sonocotta/esp32-audio-dock/hardware/3-louder-esp32/rev-h7/2508-louder-esp32-h7-schematic.pdf

## U1³⁹ GND

## MCU

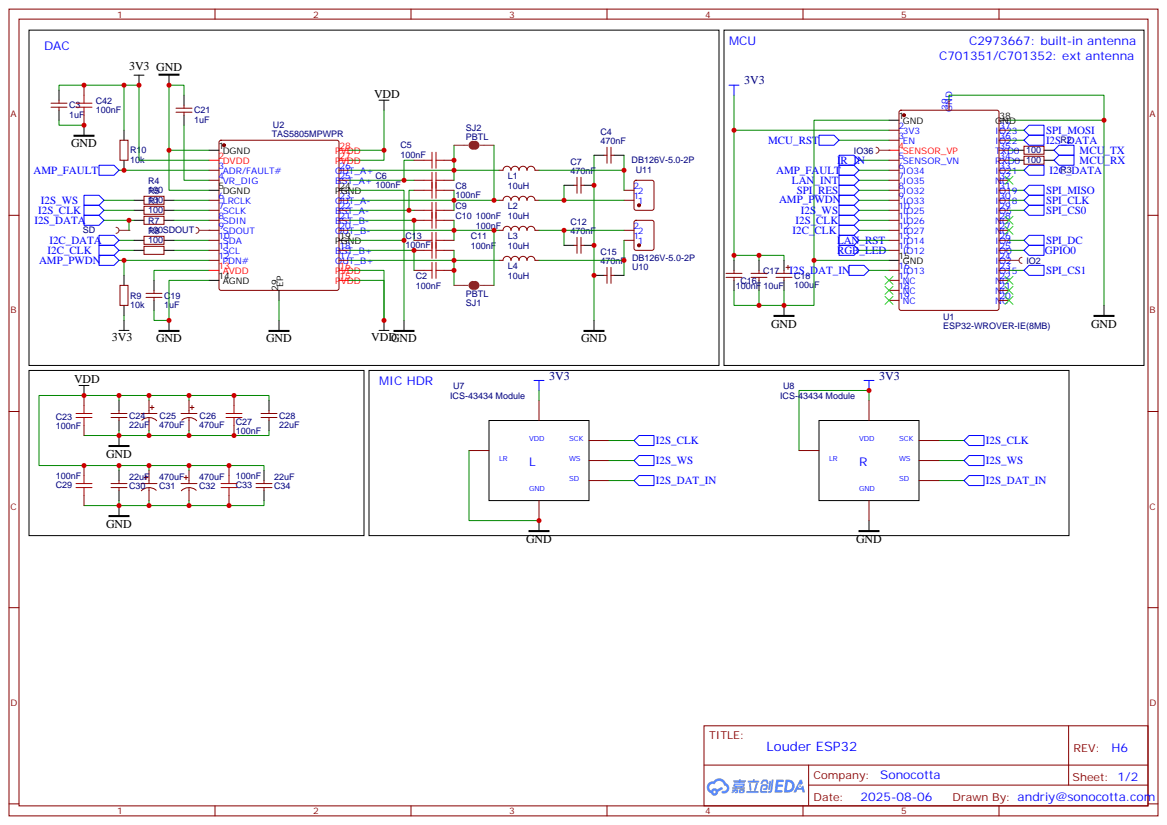
[picture p3: page 1]

Drawn By: andriy@sonocotta.com

## USB-TO-SERIAL BRIDGE USR-ES1 LAN module (W5500)

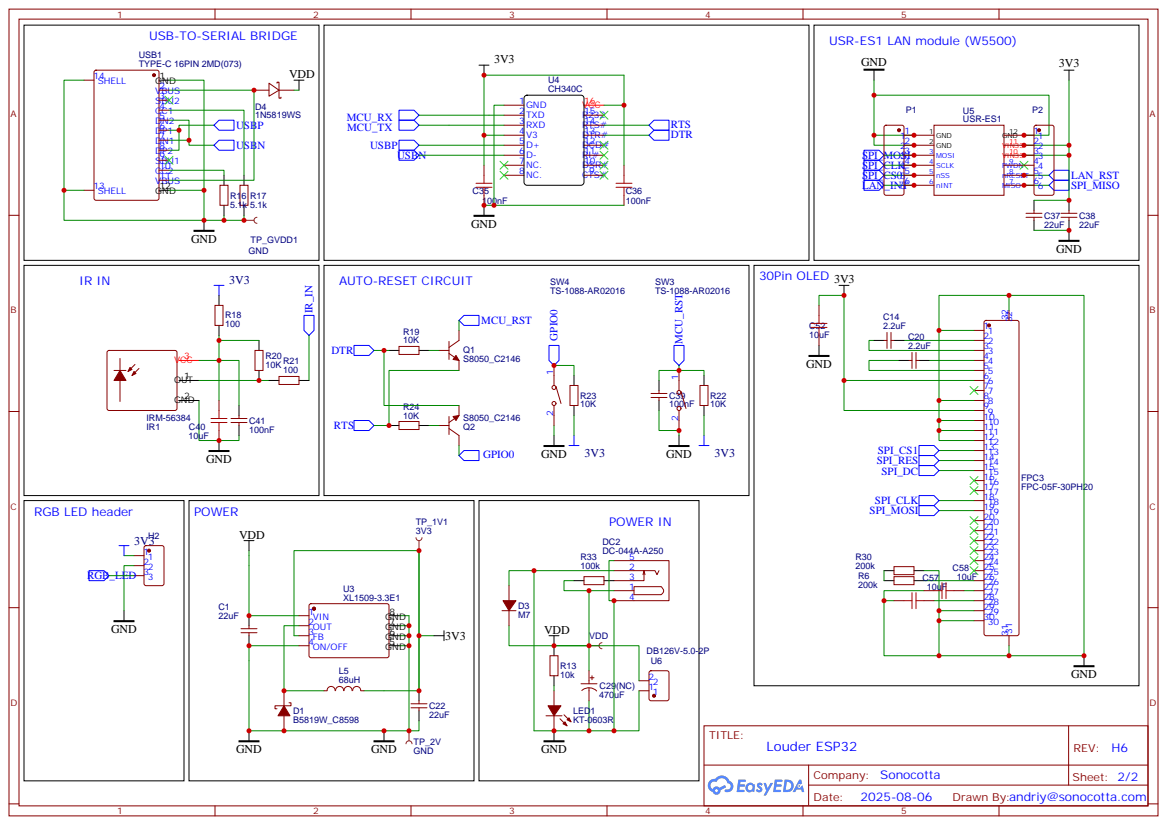
[picture p4: page 2]

Drawn By:andriy@sonocotta.com
