sonocotta/esp32-audio-dock/hardware/10-louder-esp32-pro/rev-c-pd-edition/2605-louder-esp32s3-plus-pd-c-schematic.pdf

# IO20 14IO19 13IO8 12IO18 11IO17 10IO16 9

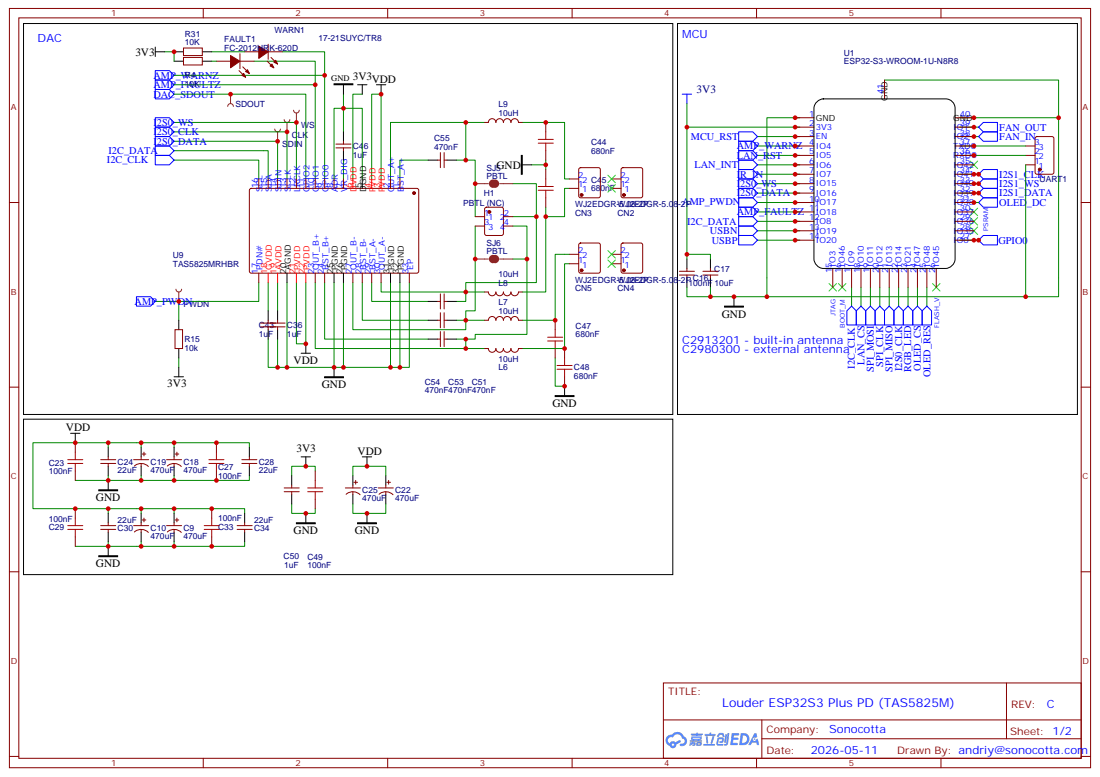
[picture p5: page 1]

9GPIO1 10 GPIO2 11 LRCLK 12 SCLK 13 SDIN 14 SDA 15 SCL 16 PDN# 17GVDD 18AVDD 19AGND 20PVDD 21PVDD 22OUT_B+ 23BST_B+ 24

Drawn By: andriy@sonocotta.com

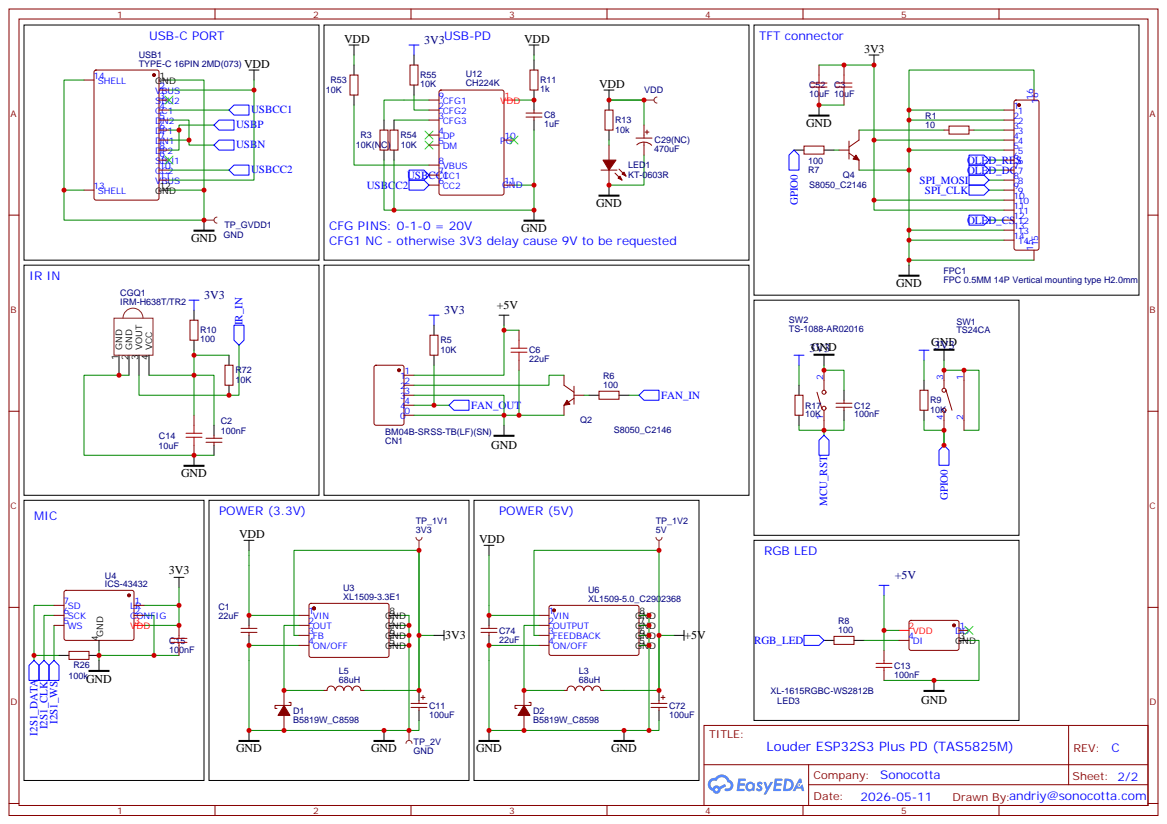
[picture p6: page 2]

CFG PINS: 0-1-0 = 20V
CFG1 NC - otherwise 3V3 delay cause 9V to be requested

FPC1
FPC 0.5MM 14P Vertical mounting type H2.0mm

Drawn By:andriy@sonocotta.com

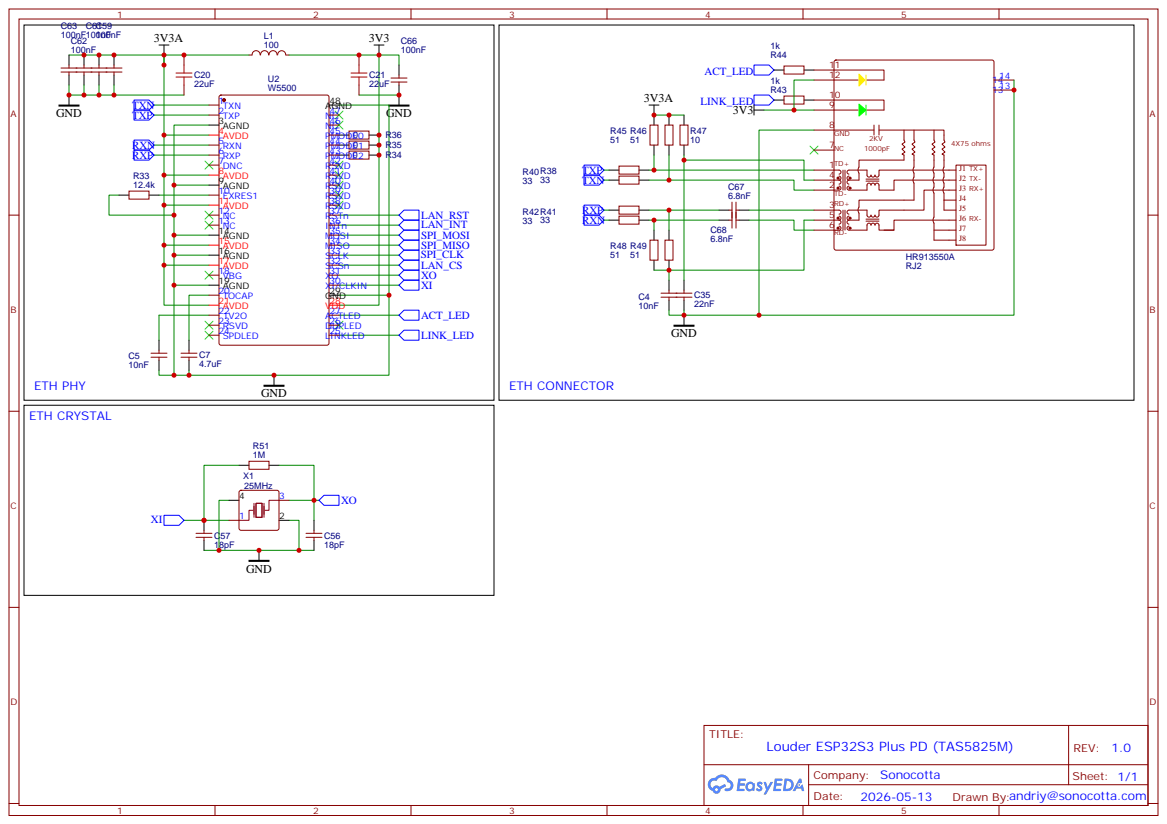
[picture p7: page 3]

Drawn By:andriy@sonocotta.com
