sonocotta/esp32-audio-dock/hardware/2-loud-esp32/rev-e3/2603-loud-esp32-e3-schematic.pdf

# OUTN 10 GND 11 N.C. 12 N.C. 13 LRCLK 14 GND 15 BCLK 16

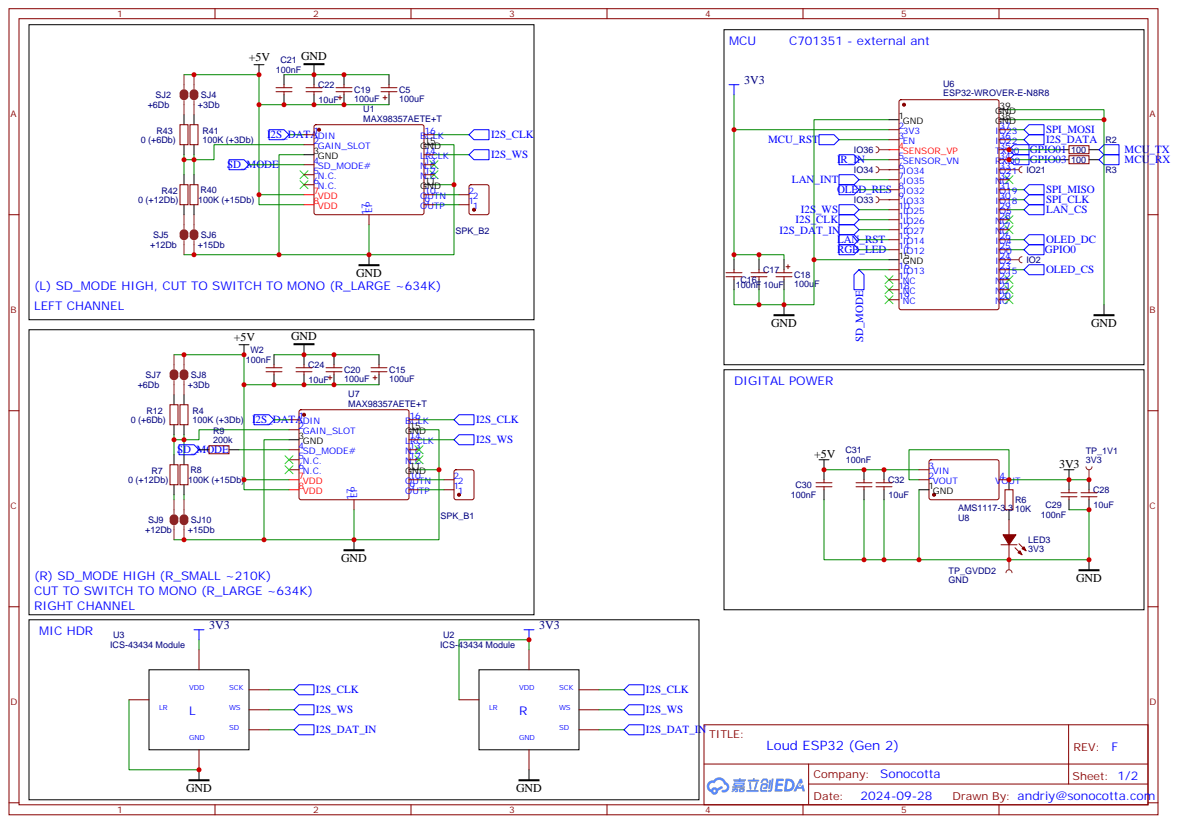
[picture p10: page 1]

(L) SD_MODE HIGH, CUT TO SWITCH TO MONO (R_LARGE ~634K)
LEFT CHANNEL

(R) SD_MODE HIGH (R_SMALL ~210K)
CUT TO SWITCH TO MONO (R_LARGE ~634K)
RIGHT CHANNEL
MIC HDR

Drawn By: andriy@sonocotta.com

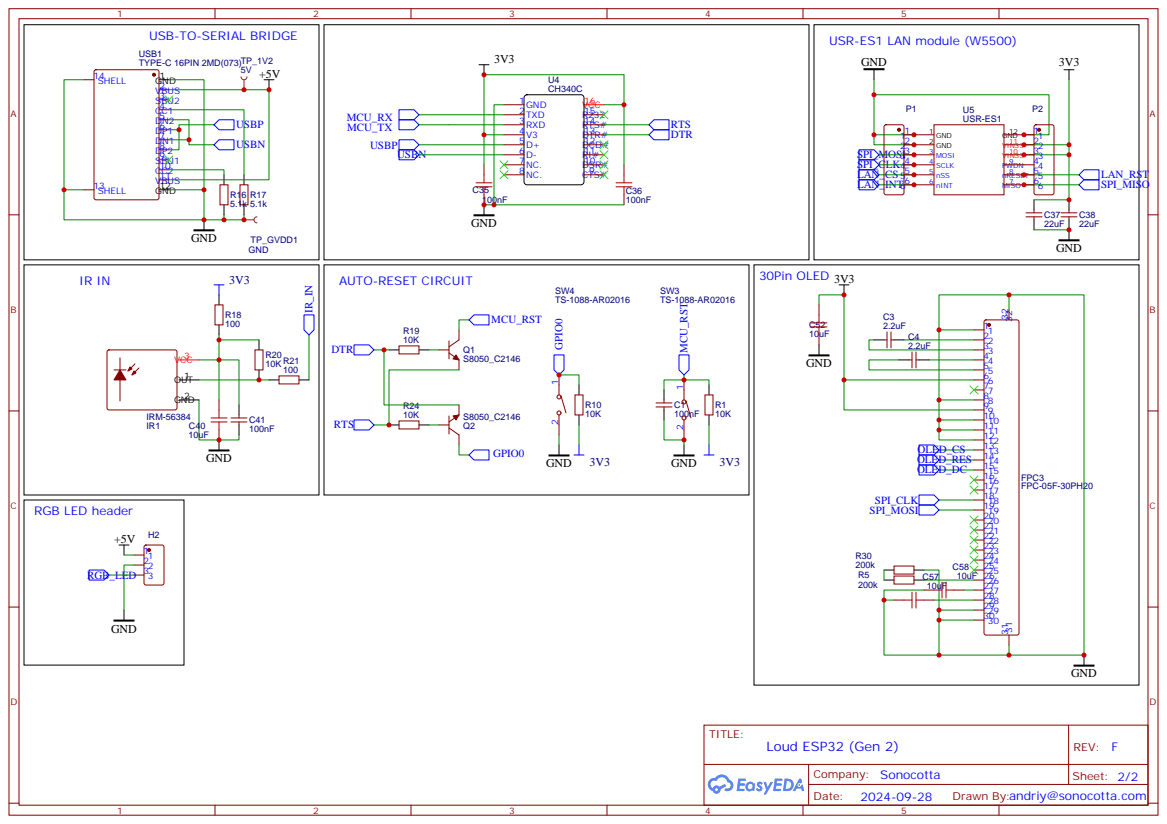
[picture p11: page 2]

Drawn By:andriy@sonocotta.com
