sonocotta/esp32-audio-dock/hardware/7-louder-esp32-plus/rev-b/2602-louder-esp32-plus-b-schematic.pdf

### U2³⁹ GND

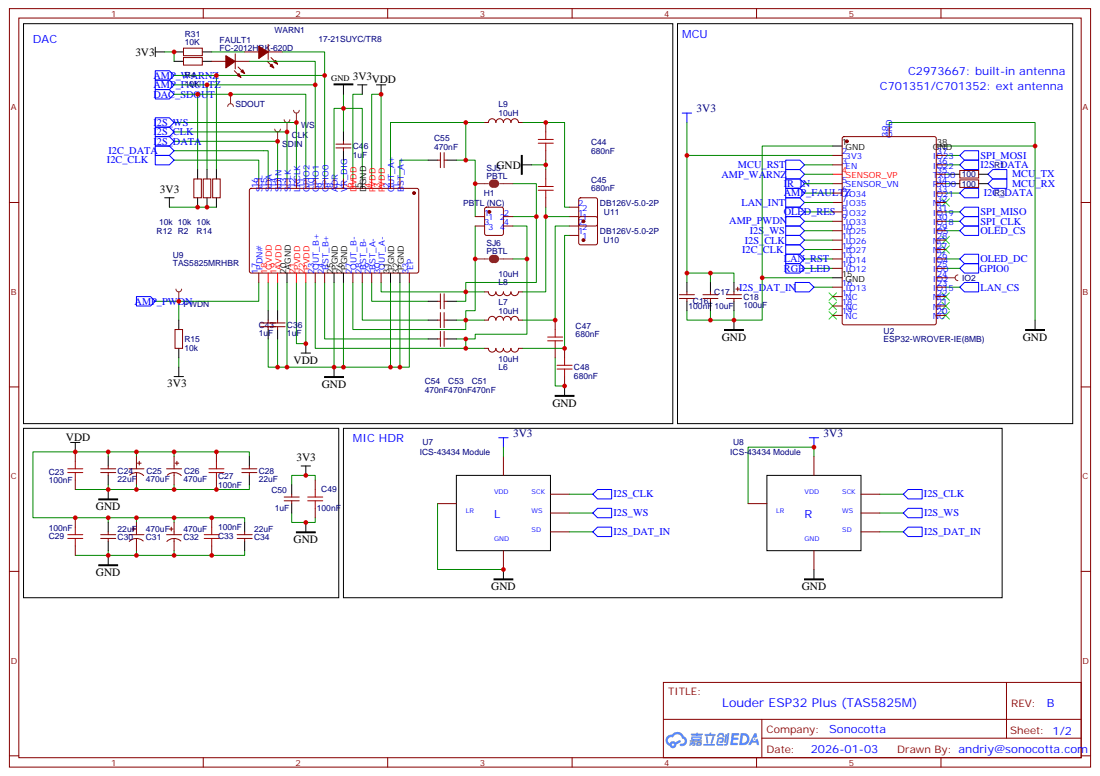
[picture p14: page 1]

9GPIO1 10 GPIO2 11 LRCLK 12 SCLK 13 SDIN 14 SDA 15 SCL 16 PDN# 17GVDD 18AVDD 19AGND 20PVDD 21PVDD 22OUT_B+ 23BST_B+ 24

Drawn By: andriy@sonocotta.com

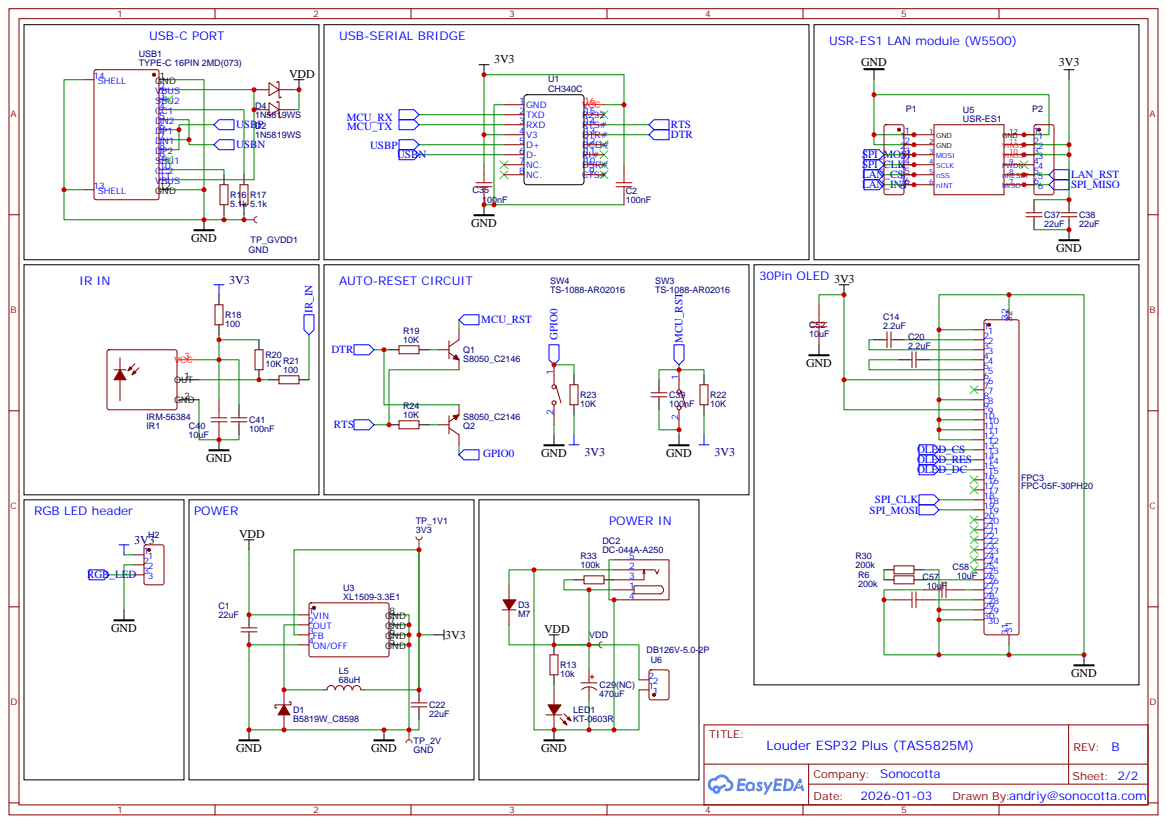
[picture p15: page 2]

Drawn By:andriy@sonocotta.com
