sonocotta/esp32-audio-dock/hardware/7-louder-esp32-plus/rev-a-s3/2601-louder-esp32s3-plus-a-schematic.pdf

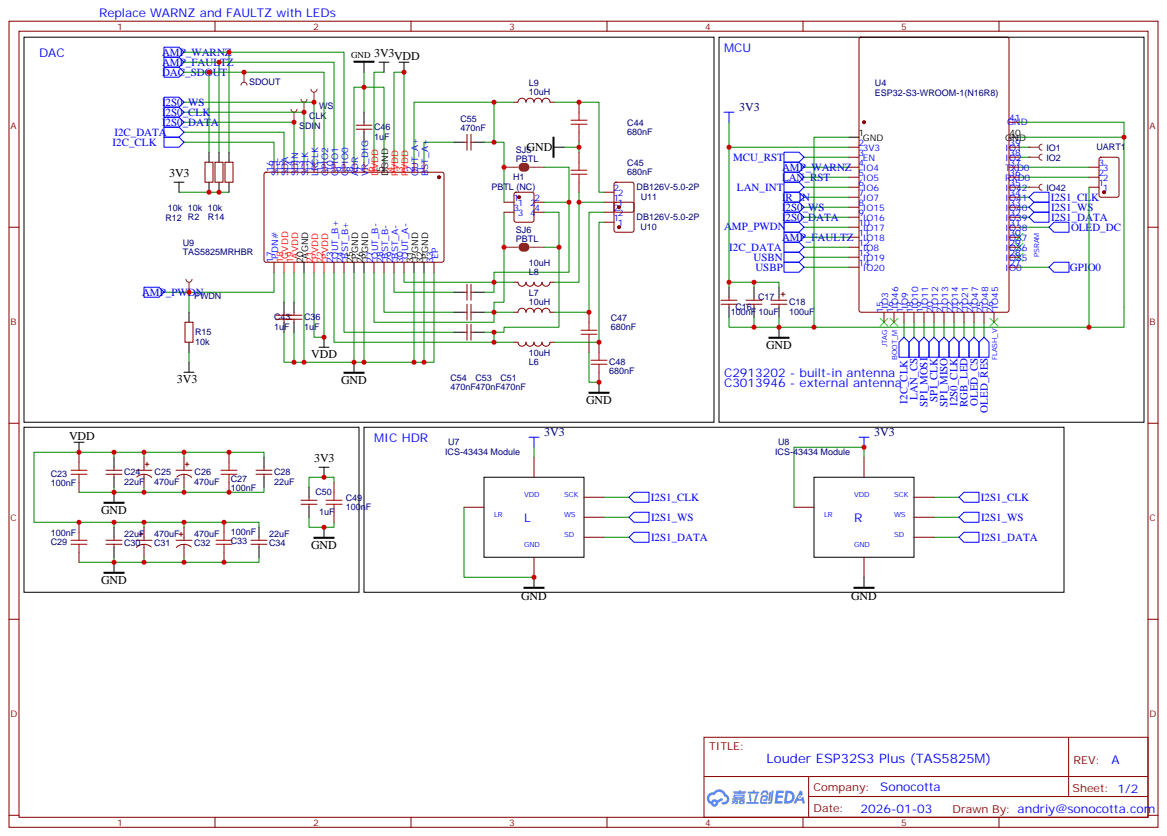
[picture p16: page 1]

Replace WARNZ and FAULTZ with LEDs

9GPIO1 10 GPIO2 11 LRCLK 12 SCLK 13 SDIN 14 SDA 15 SCL 16 PDN# 17GVDD 18AVDD 19AGND 20PVDD 21PVDD 22OUT_B+ 23BST_B+ 24

Drawn By: andriy@sonocotta.com

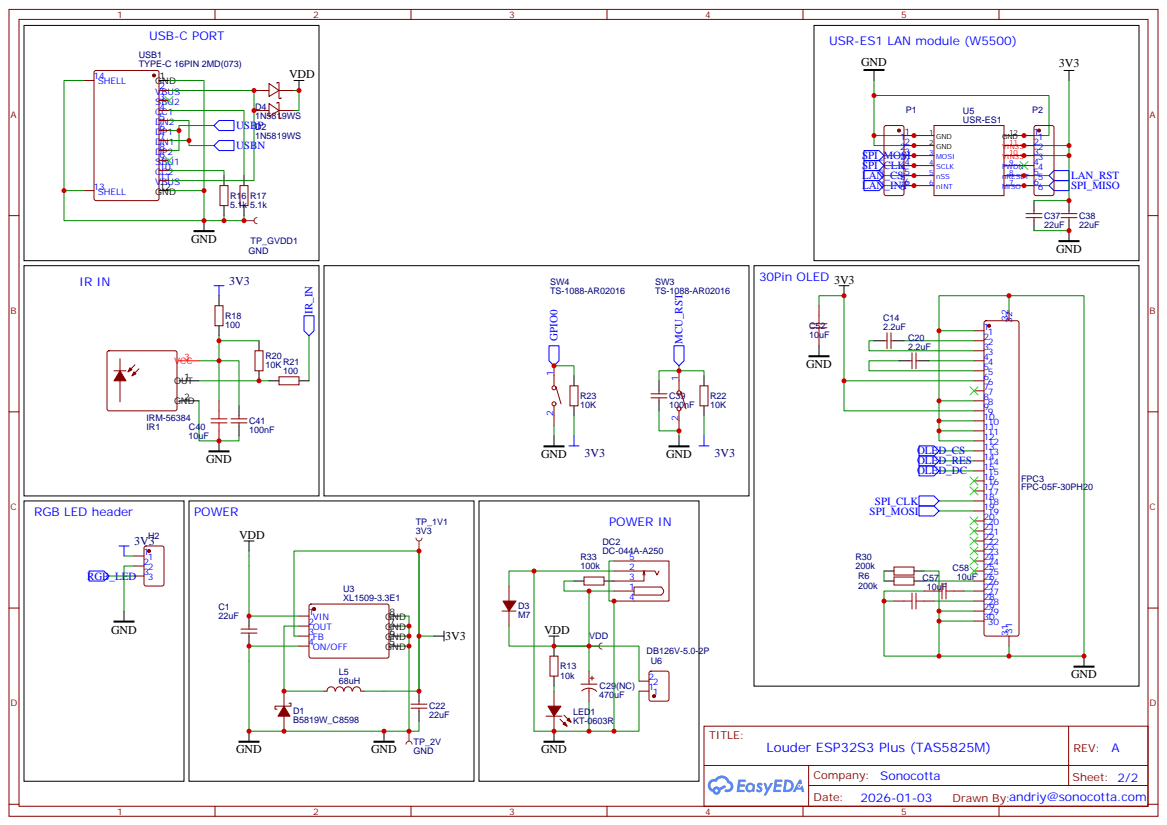
[picture p17: page 2]

Drawn By:andriy@sonocotta.com
