sonocotta/esp32-audio-dock/hardware/1-hifi-esp32/rev-f4/2511-hifi-esp32-f4-schematic.pdf

## MCU

## ANALOG POWER

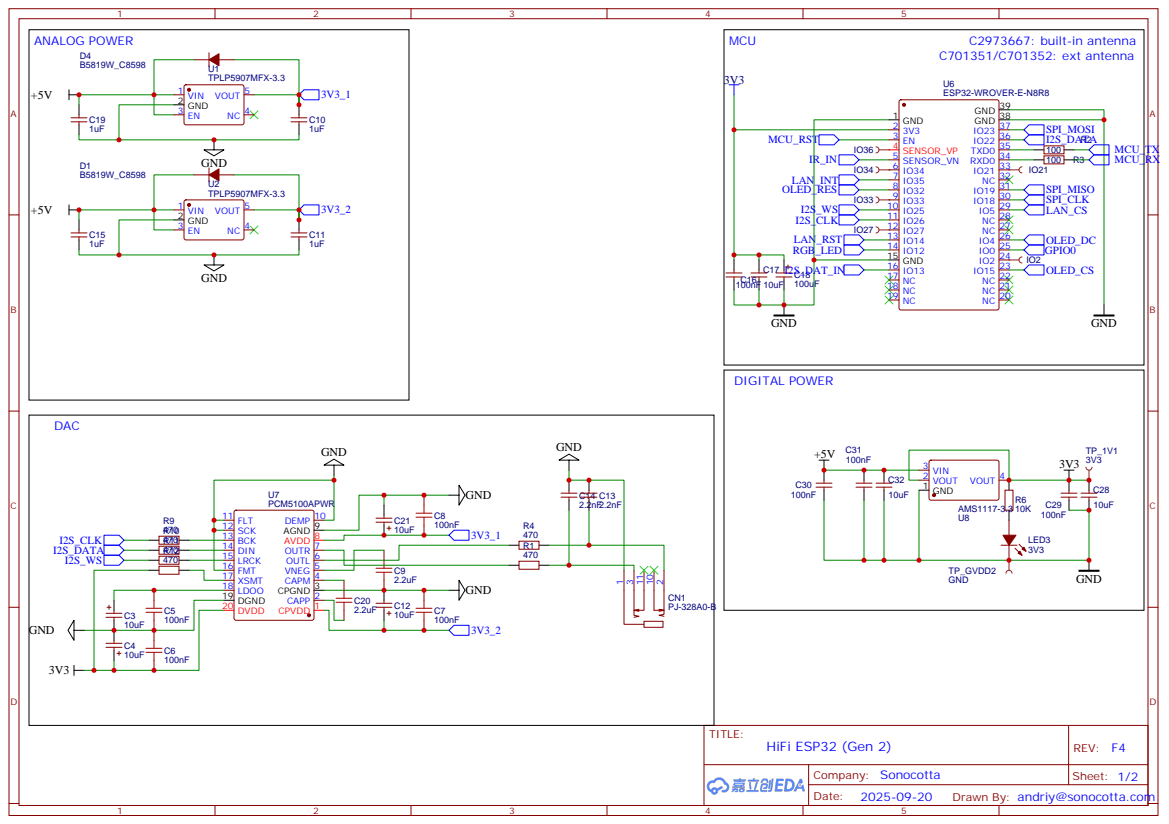
[picture p18: page 1]

Drawn By: andriy@sonocotta.com

## USB-TO-SERIAL BRIDGE USR-ES1 LAN module (W5500)

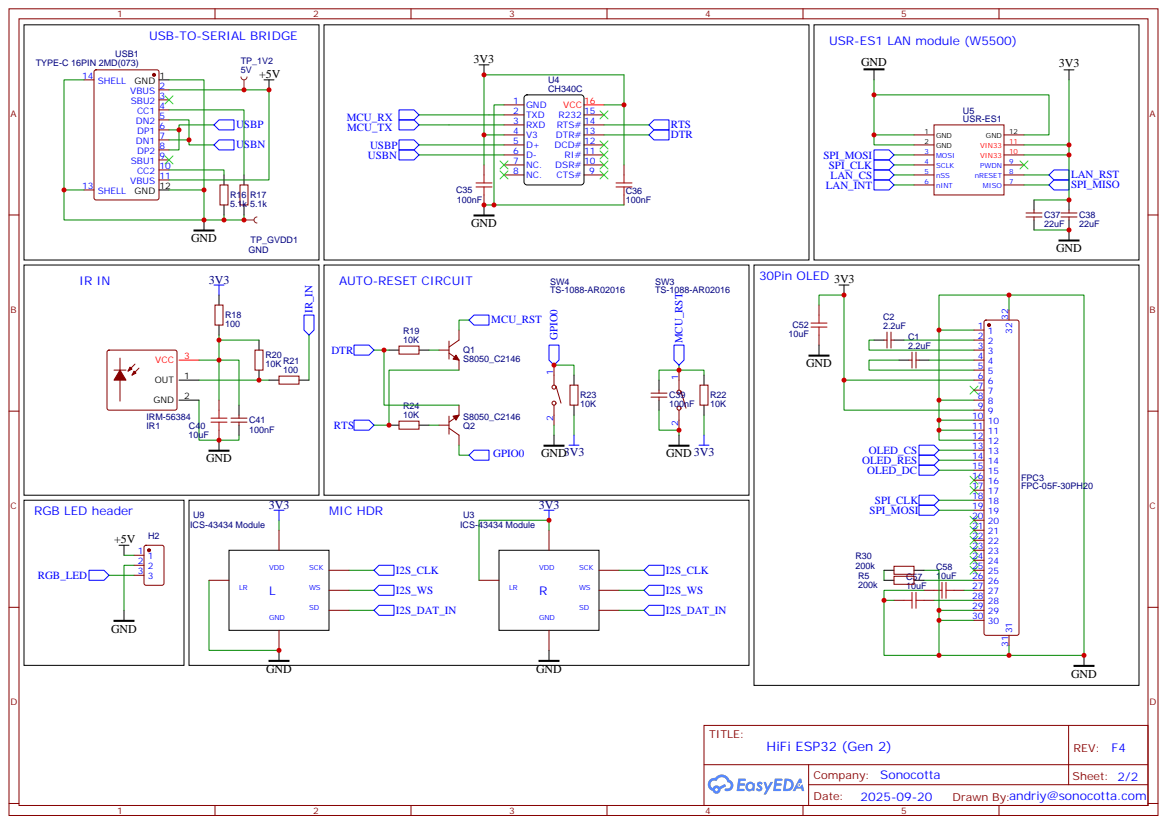
[picture p19: page 2]

Drawn By:andriy@sonocotta.com
