sonocotta/esp32-audio-dock/hardware/5-hifi-esp32-plus/rev-h1/2511-hifi-esp32s3-plus-h1-schematic.pdf

## ANALOG POWER

## MCU

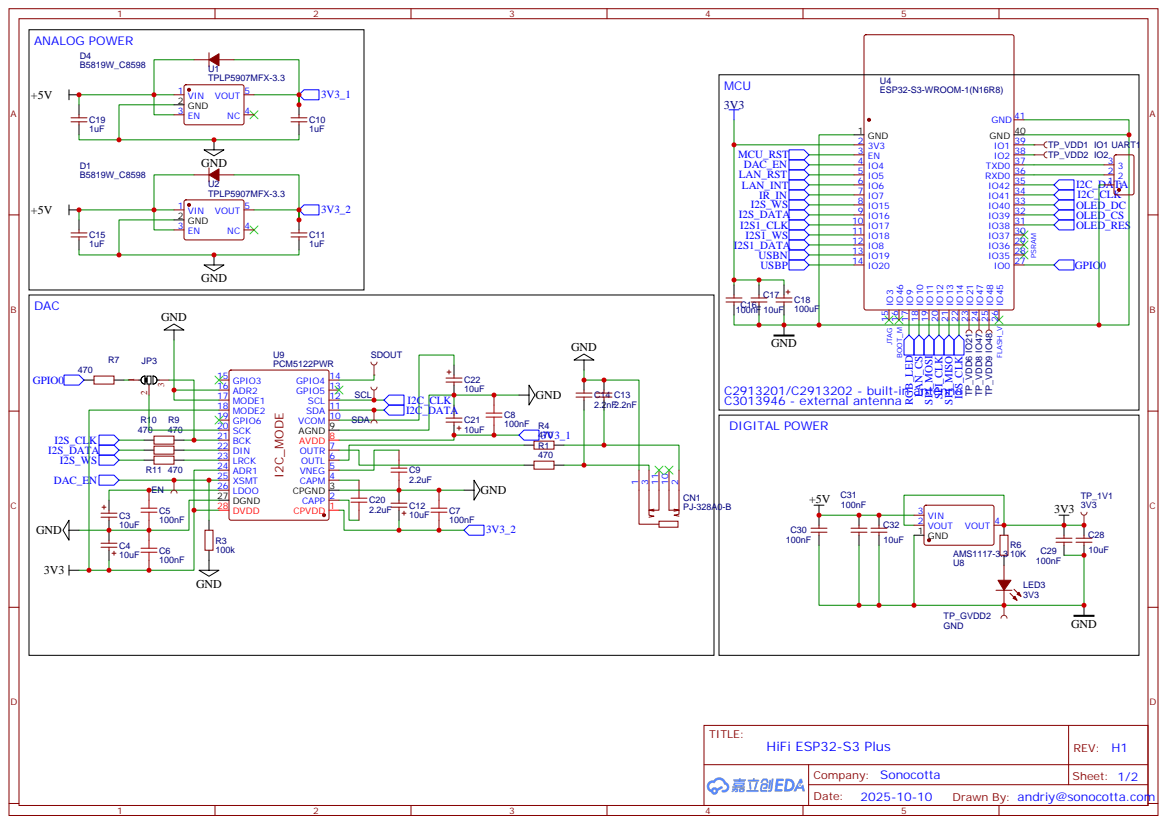
[picture p20: page 1]

Drawn By: andriy@sonocotta.com

## USB-TO-SERIAL BRIDGE USR-ES1 LAN module (W5500)

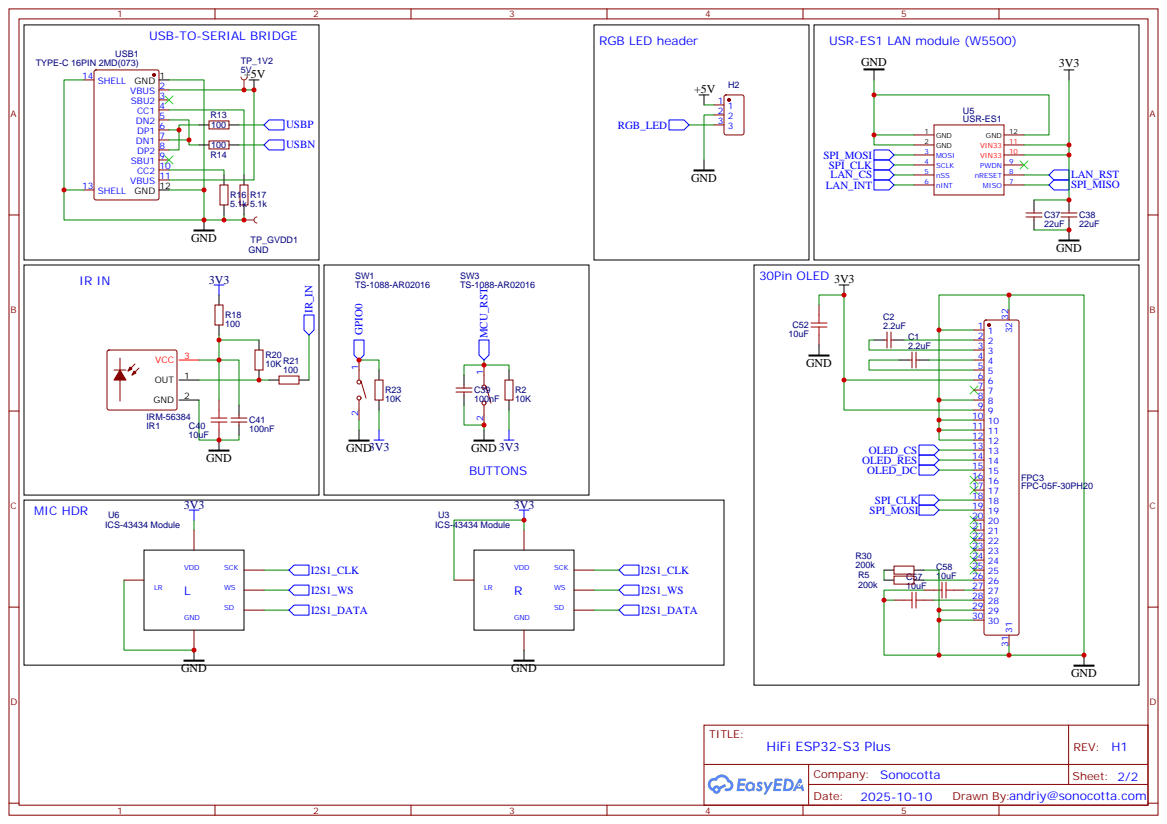
[picture p21: page 2]

Drawn By:andriy@sonocotta.com
