sonocotta/esp32-audio-dock/hardware/5-hifi-esp32-plus/rev-j/2511-hifi-esp32-plus-j-schematic.pdf

## ANALOG POWER

## C701351/C701352: ext antenna

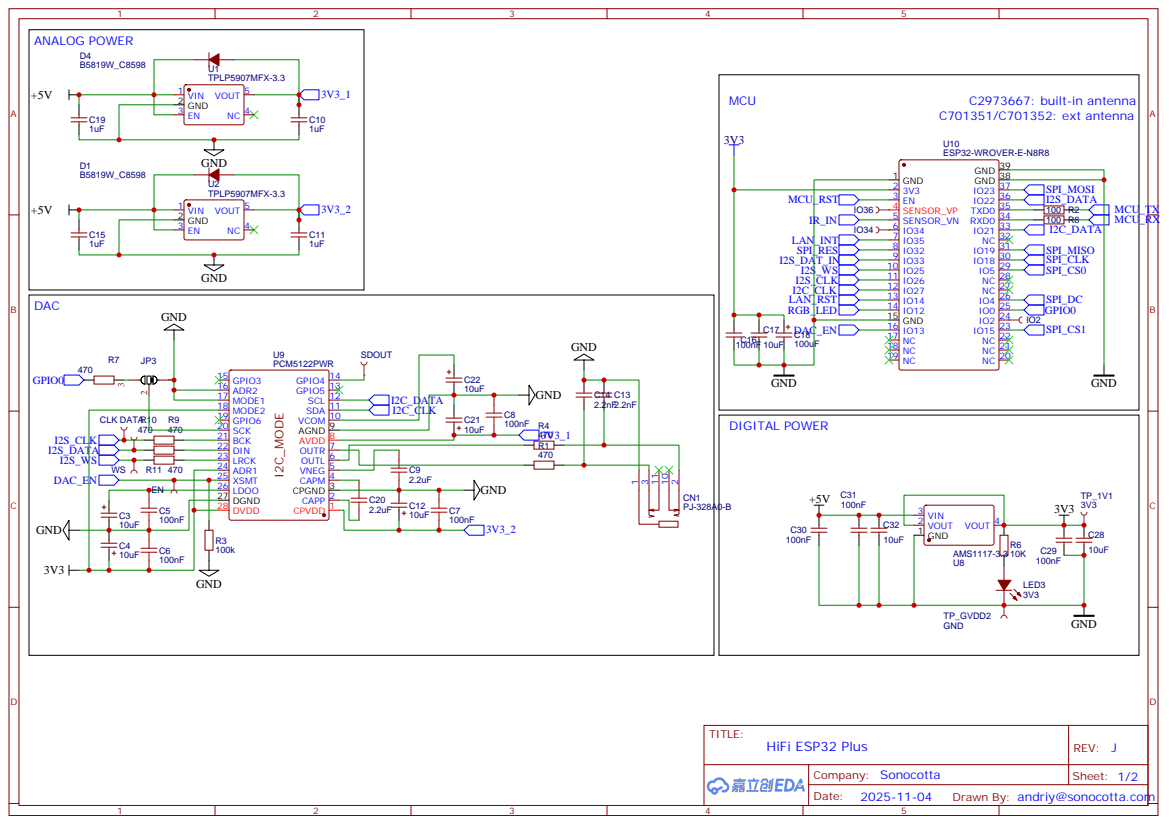
[picture p22: page 1]

Drawn By: andriy@sonocotta.com

## USB-TO-SERIAL BRIDGE USR-ES1 LAN module (W5500)

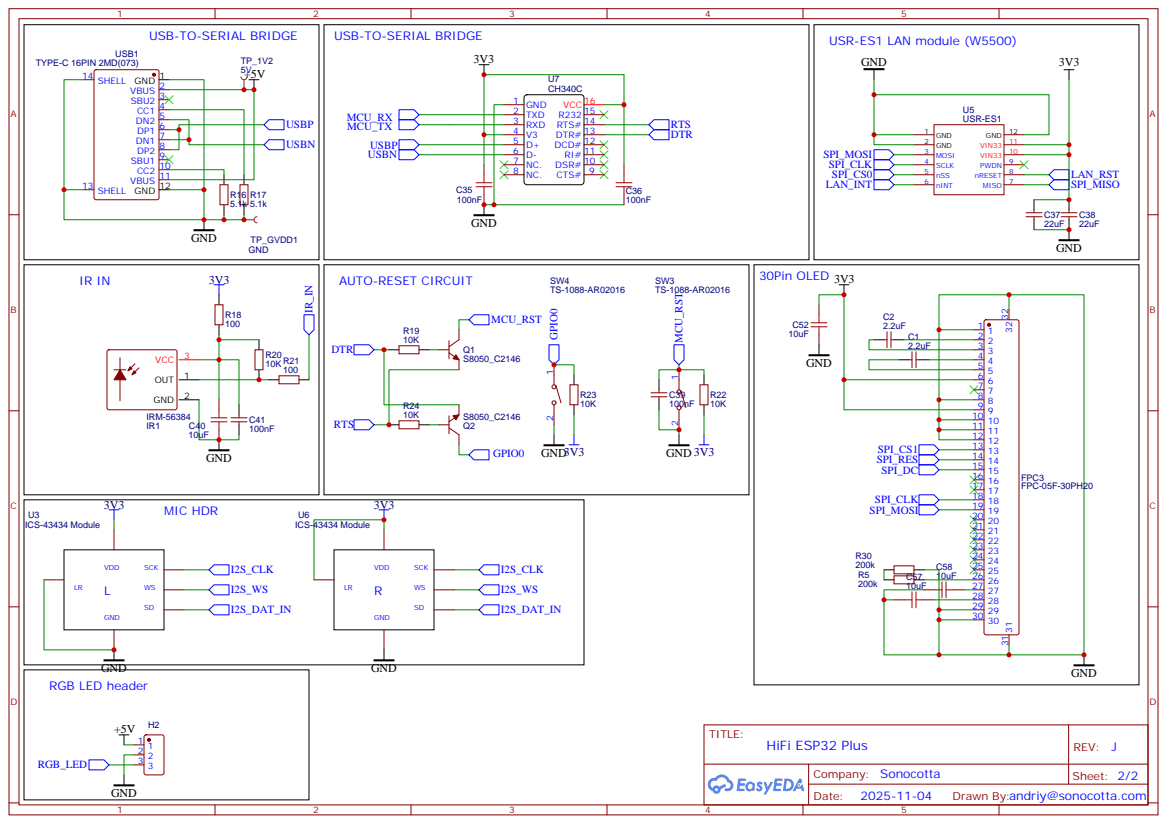
[picture p23: page 2]

USB-TO-SERIAL BRIDGE

Drawn By:andriy@sonocotta.com
