sonocotta/esp32-audio-dock/hardware/5-hifi-esp32-plus/rev-j1/2511-hifi-esp32-plus-j1-schematic.pdf

## ANALOG POWER

## C701351/C701352: ext antenna

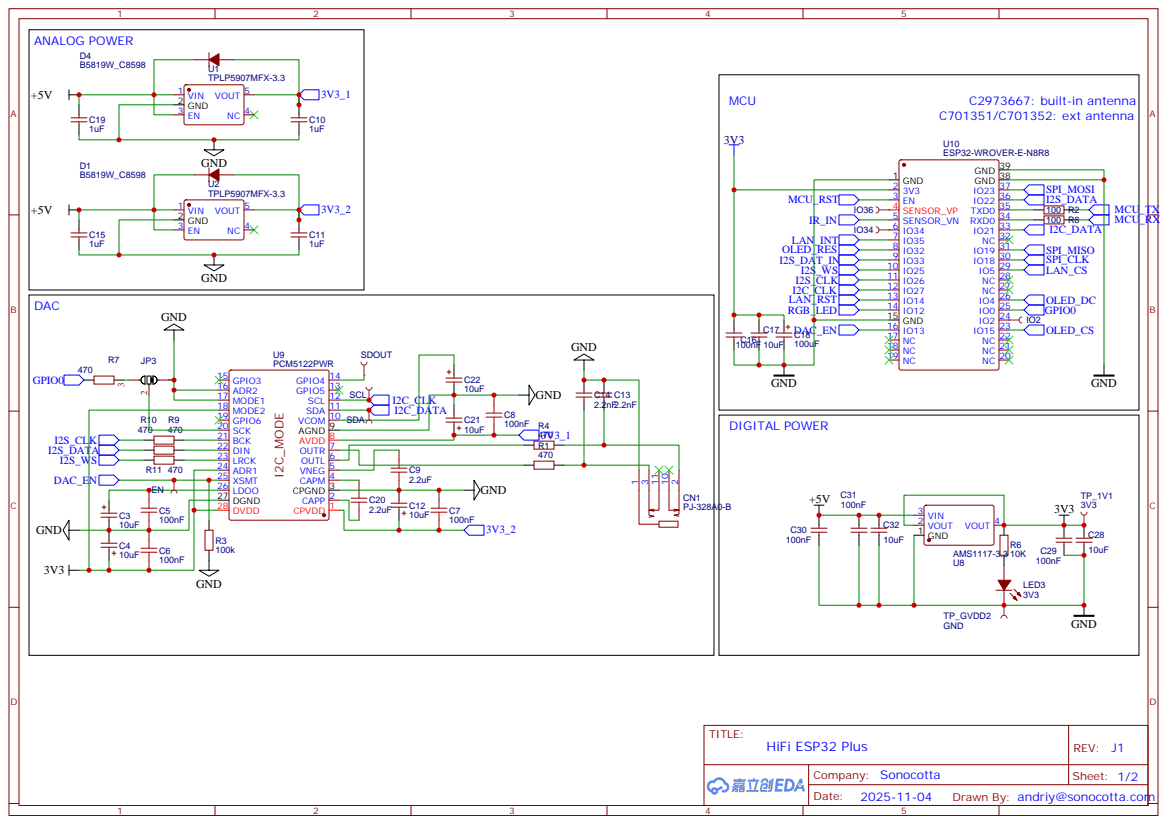
[picture p24: page 1]

Drawn By: andriy@sonocotta.com

## USB-TO-SERIAL BRIDGE USR-ES1 LAN module (W5500)

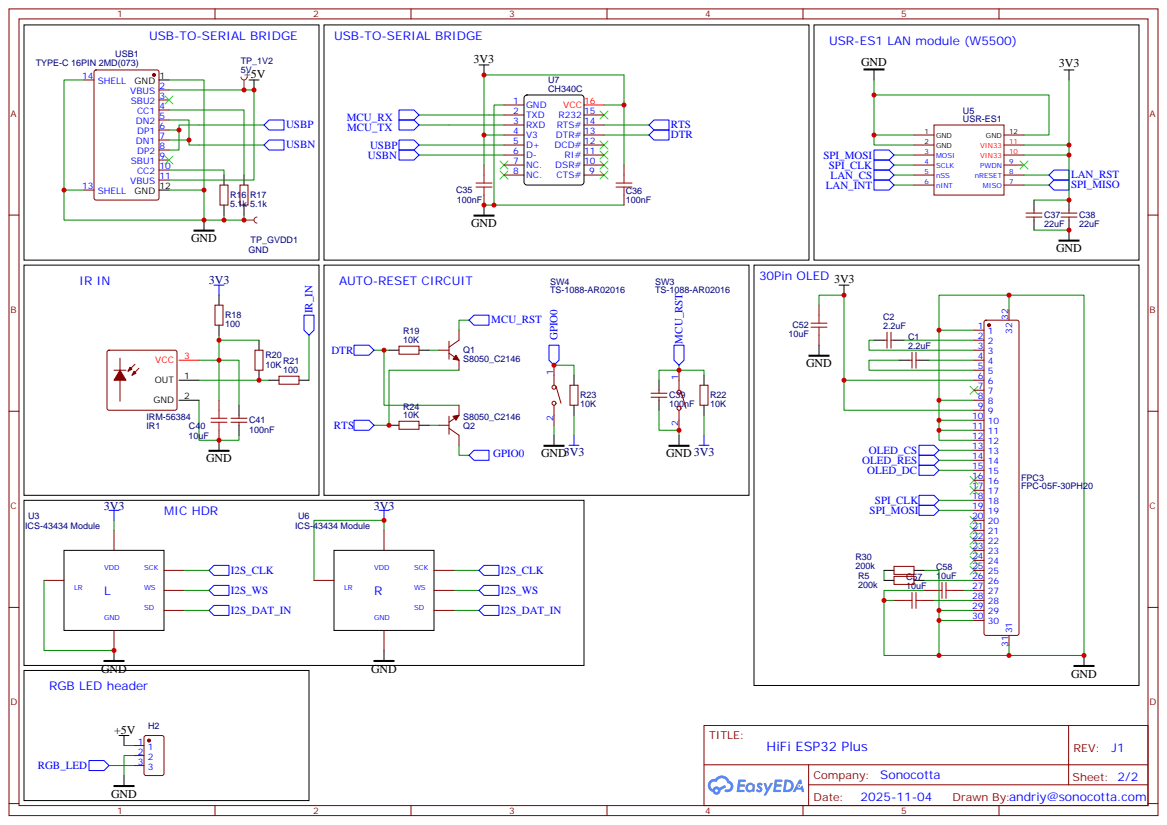
[picture p25: page 2]

USB-TO-SERIAL BRIDGE

Drawn By:andriy@sonocotta.com
