sonocotta/esp32-audio-dock/hardware/1-hifi-esp32/rev-f3/2509-hifi-esp32-f3-schematic.pdf

## MCU

## ANALOG POWER

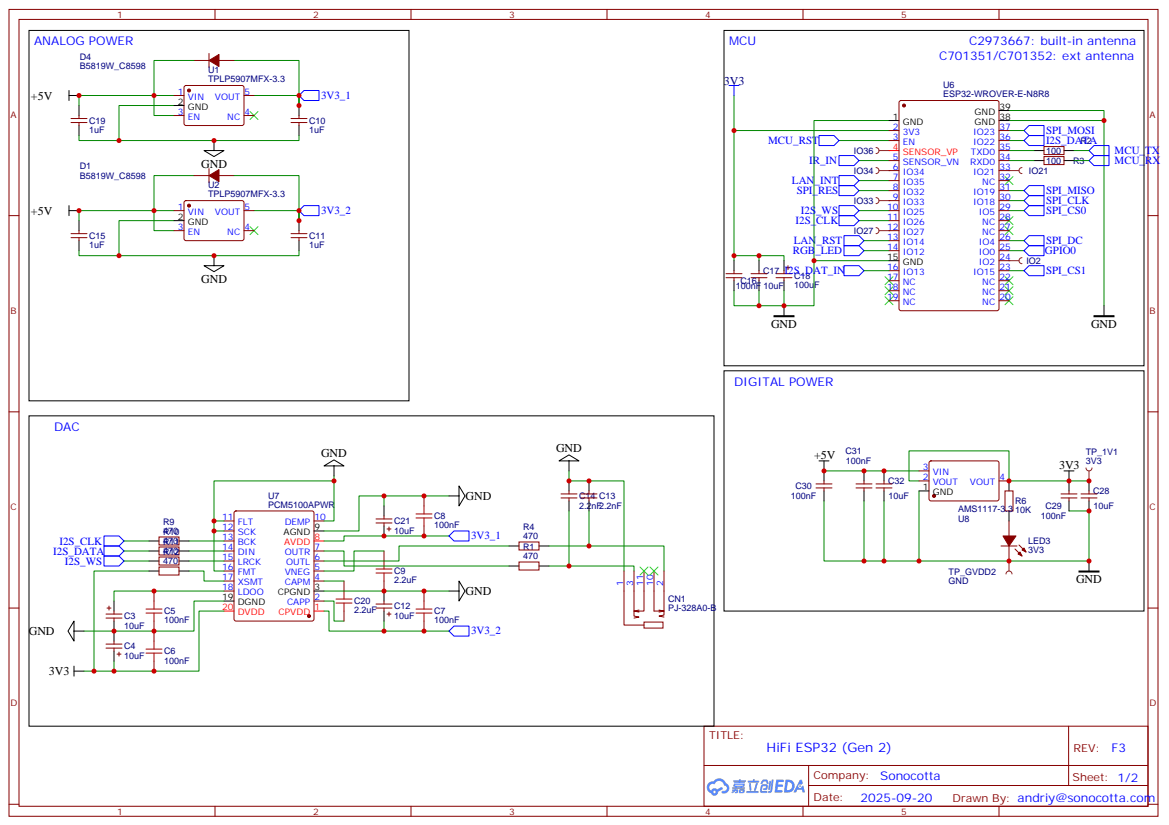
[picture p26: page 1]

Drawn By: andriy@sonocotta.com

## USB-TO-SERIAL BRIDGE USR-ES1 LAN module (W5500)

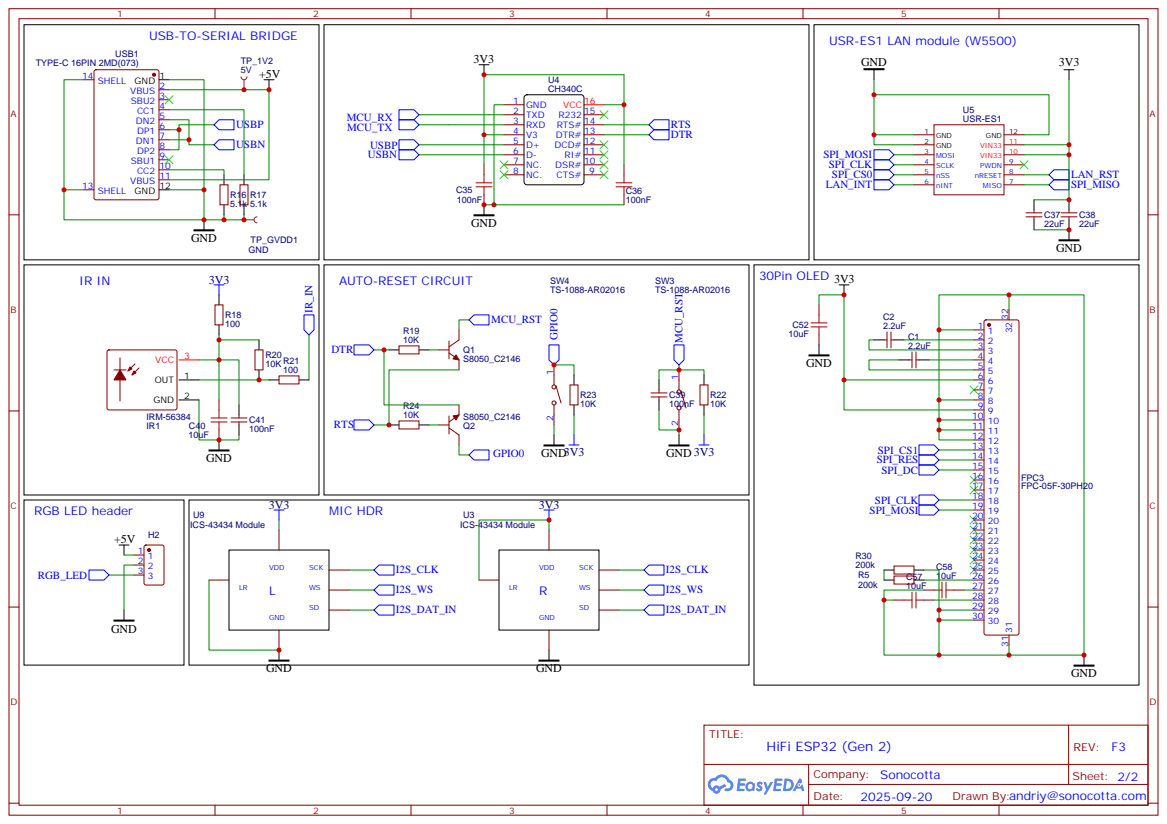
[picture p27: page 2]

Drawn By:andriy@sonocotta.com
