sonocotta/esp32-audio-dock/hardware/3-louder-esp32/rev-h7/2508-louder-esp32-h7-pcb.pdf

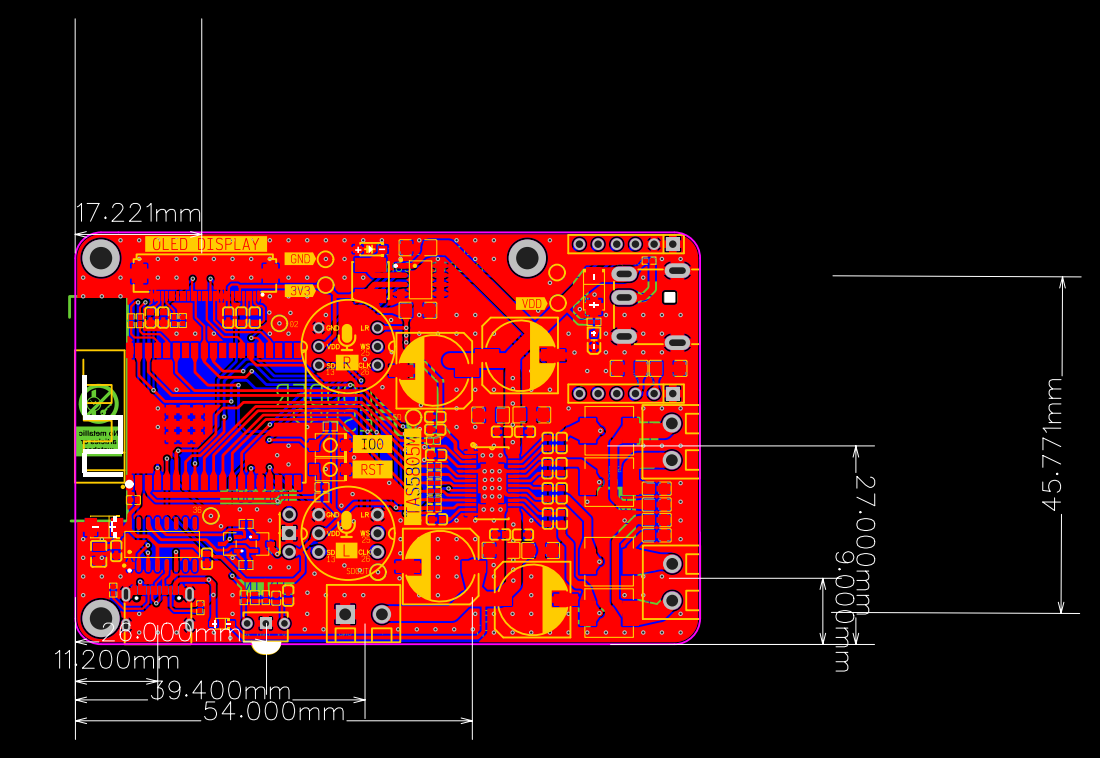
[picture p41: page 1]
