sonocotta/esp32-audio-dock/hardware/8-amped-esp32-plus/rev-d0/2606-amped-esp32-plus-d0-pcb.pdf

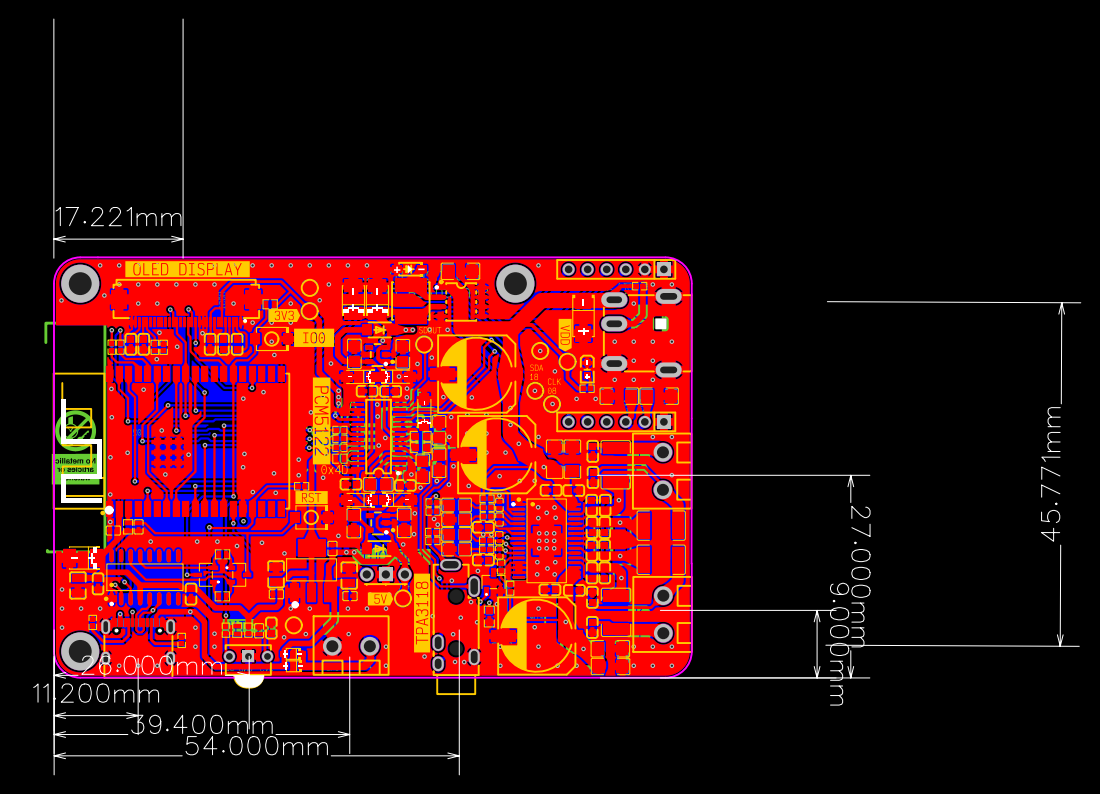
[picture p42: page 1]
