sonocotta/esp32-audio-dock/hardware/8-amped-esp32-plus/rev-d0/2606-amped-esp32-plus-d0-schematic.pdf

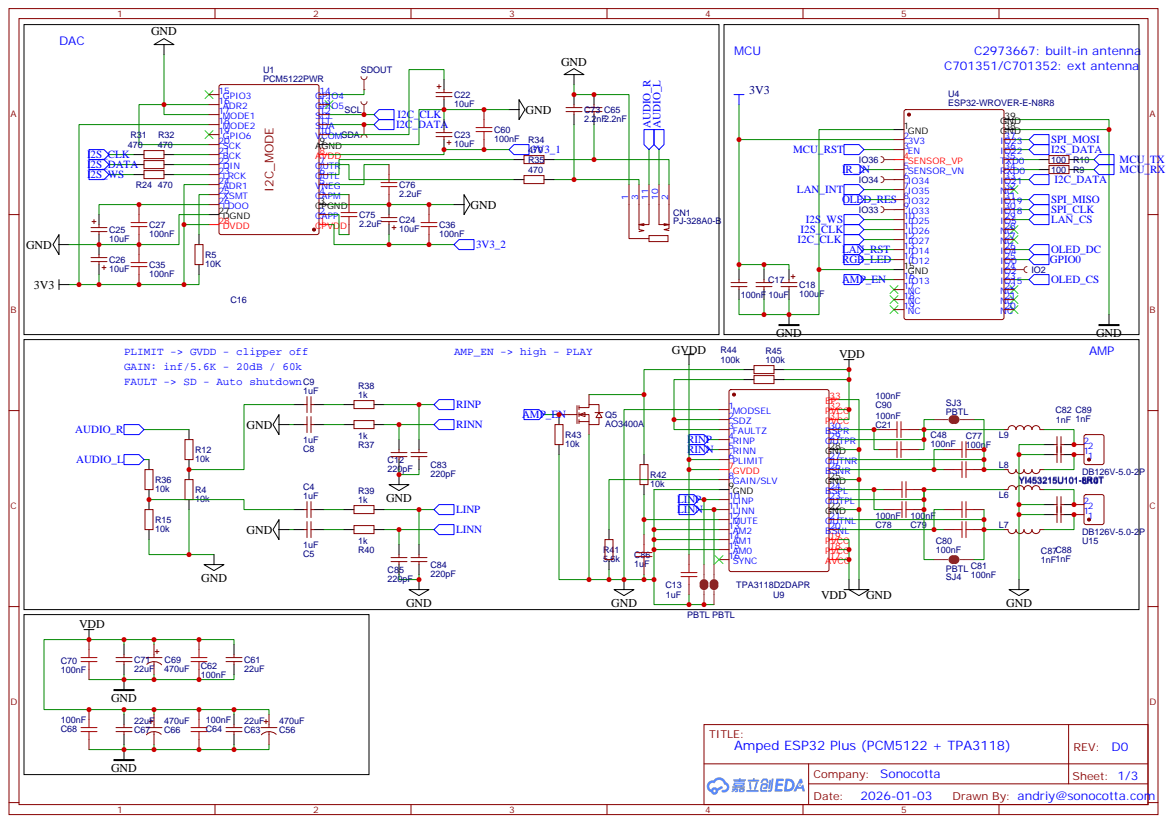
[picture p43: page 1]

PLIMIT -> GVDD - clipper off
GAIN: inf/5.6K - 20dB / 60k
FAULT -> SD - Auto shutdown

Drawn By: andriy@sonocotta.com

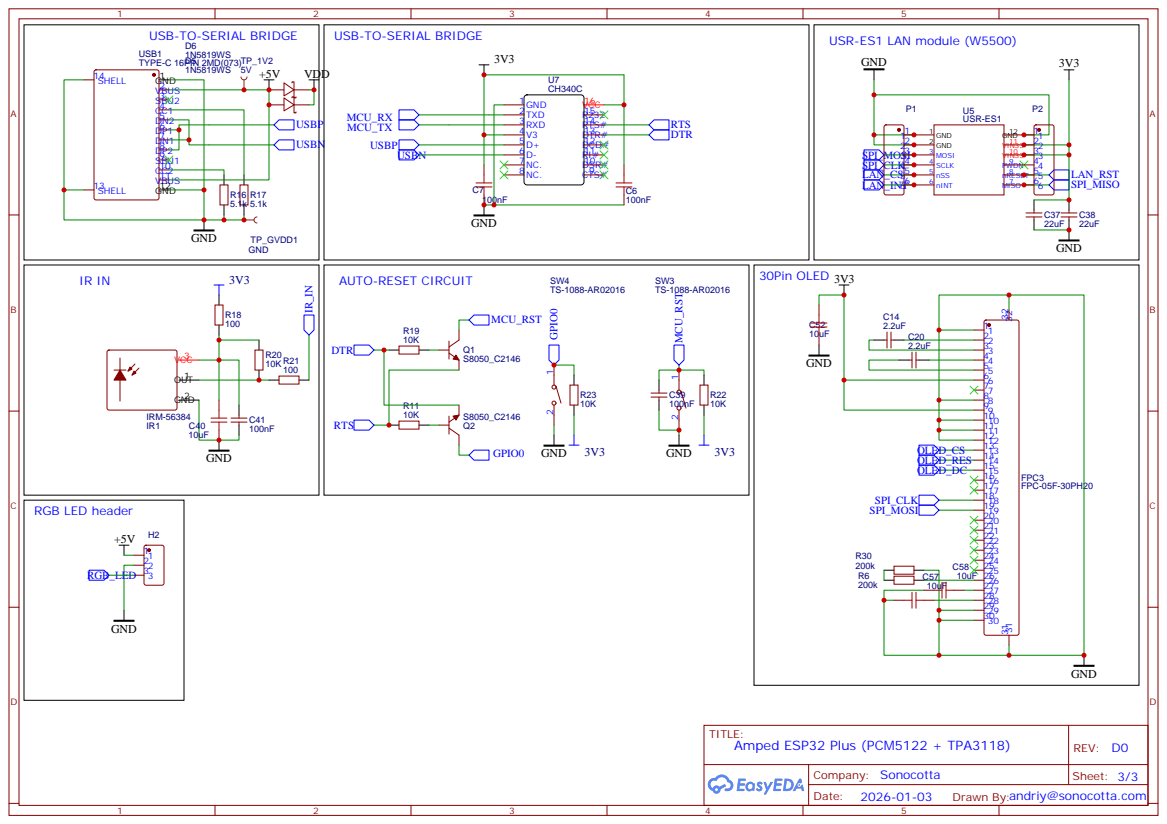
[picture p44: page 2]

USB-TO-SERIAL BRIDGE

Drawn By:andriy@sonocotta.com

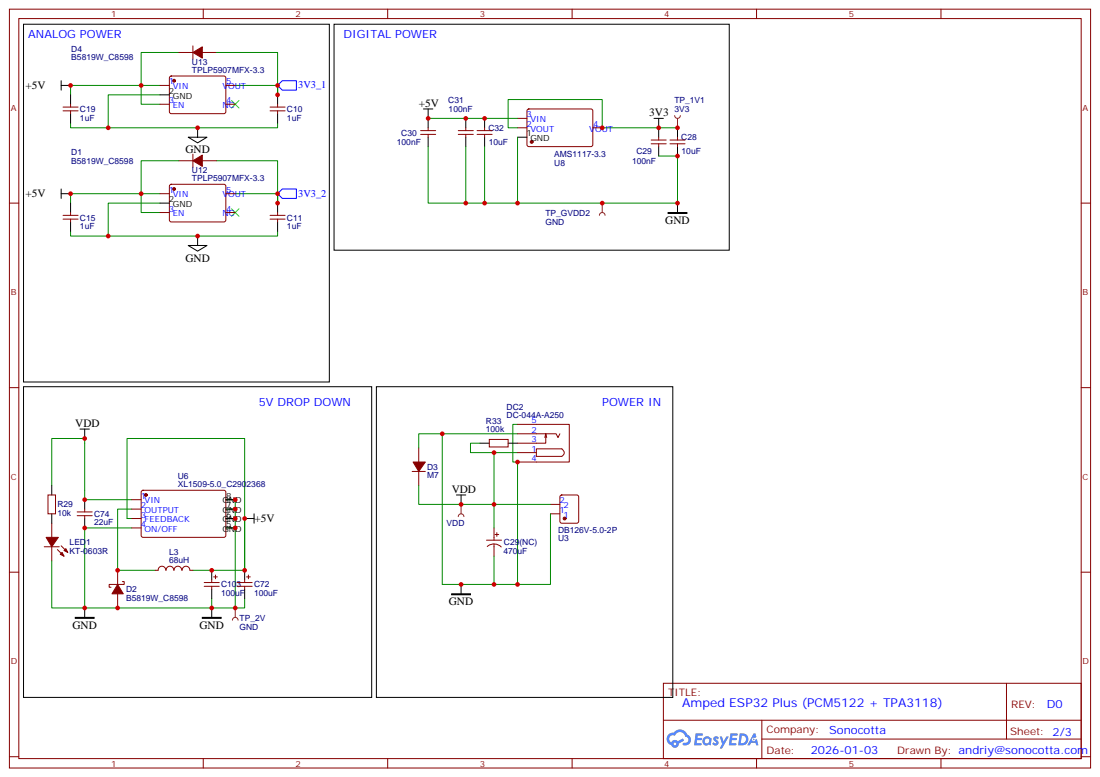
[picture p45: page 3]

Drawn By: andriy@sonocotta.com
