sonocotta/esp32-audio-dock/hardware/8-amped-esp32-plus/rev-e0/2606-amped-esp32s3-plus-e0-pcb.pdf

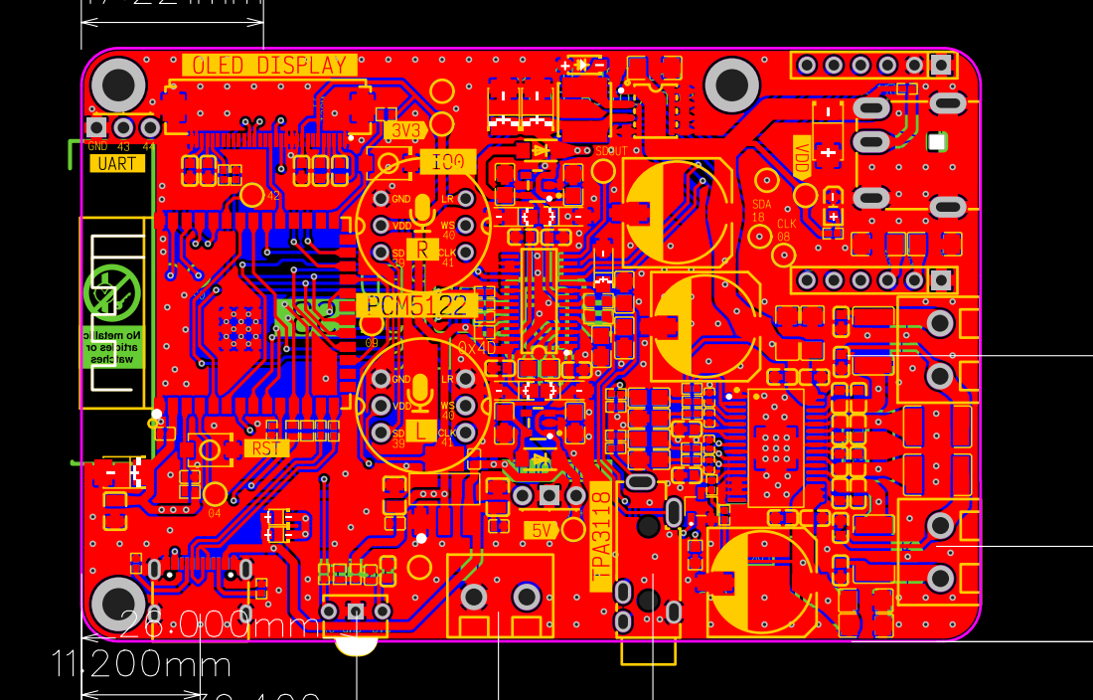
[picture p46: page 1]
