sonocotta/esp32-audio-dock/hardware/8-amped-esp32-plus/rev-e0/2606-amped-esp32s3-plus-e0-schematic.pdf

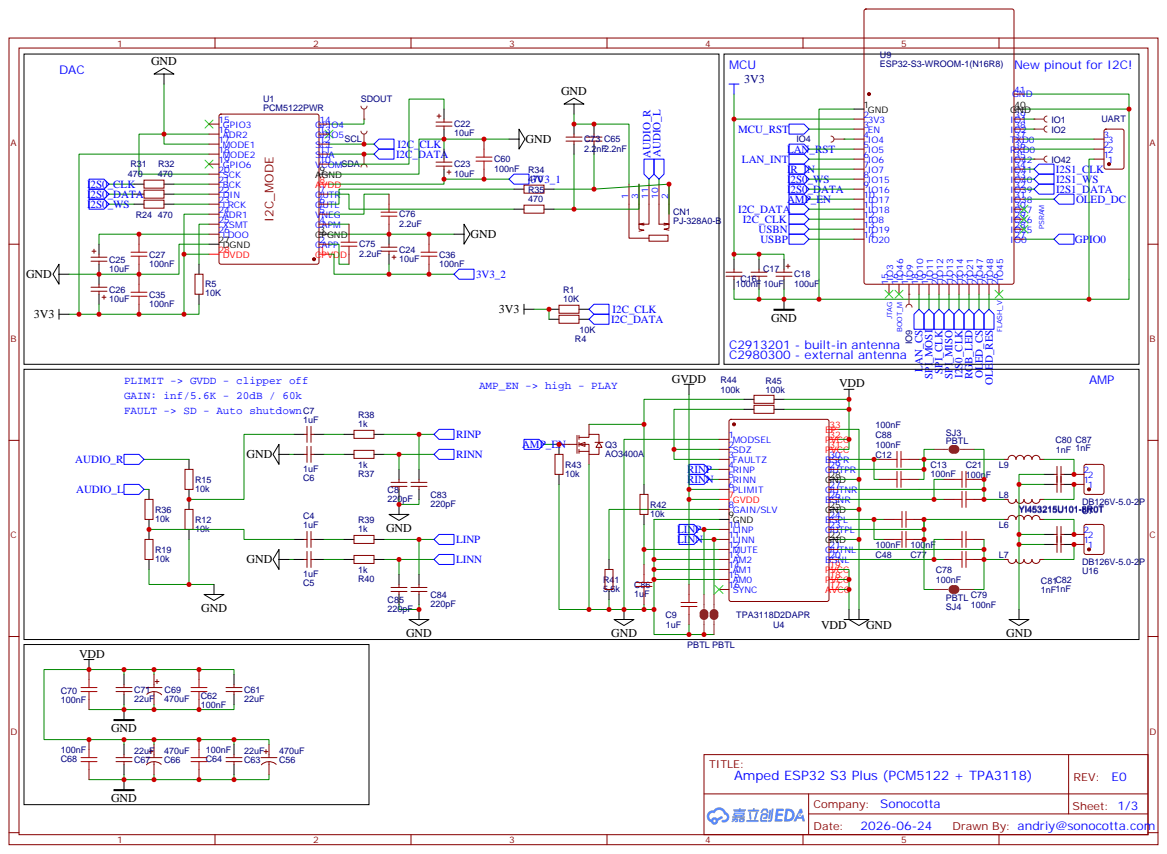
[picture p47: page 1]

PLIMIT -> GVDD - clipper off
GAIN: inf/5.6K - 20dB / 60k
FAULT -> SD - Auto shutdown

Drawn By: andriy@sonocotta.com

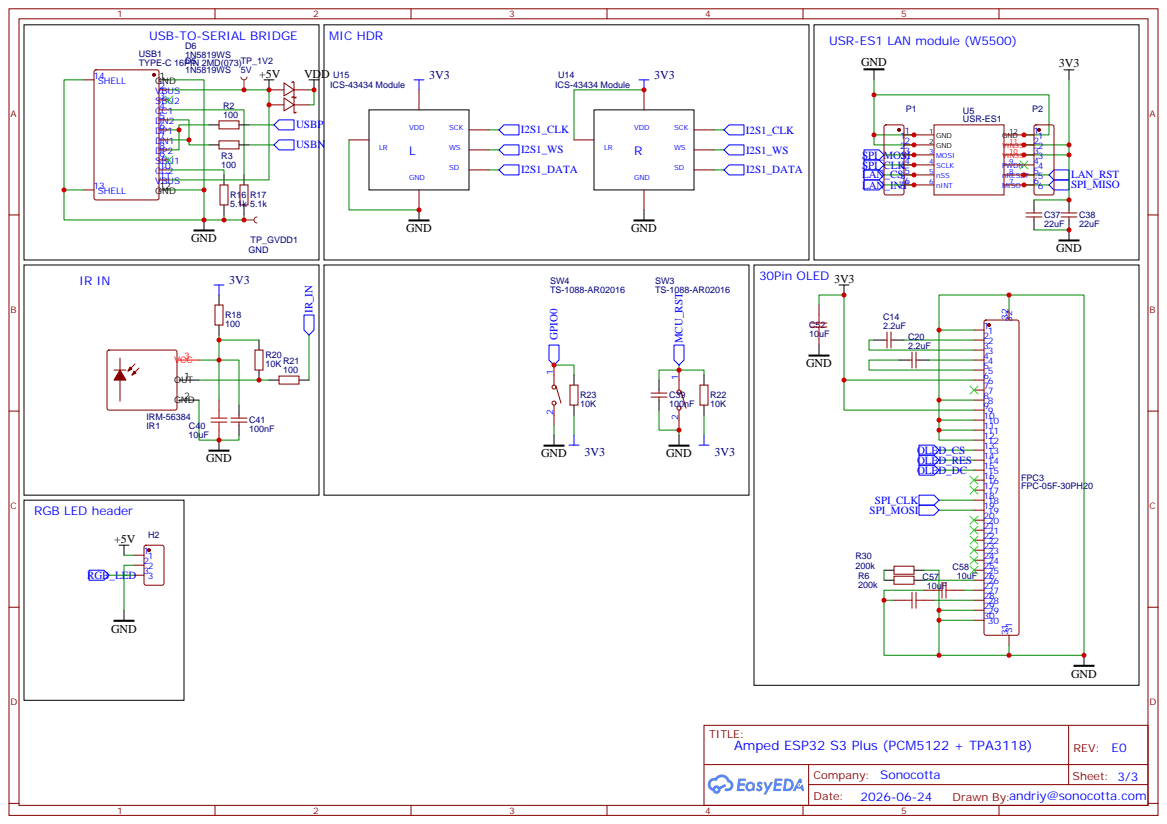
[picture p48: page 2]

Drawn By:andriy@sonocotta.com

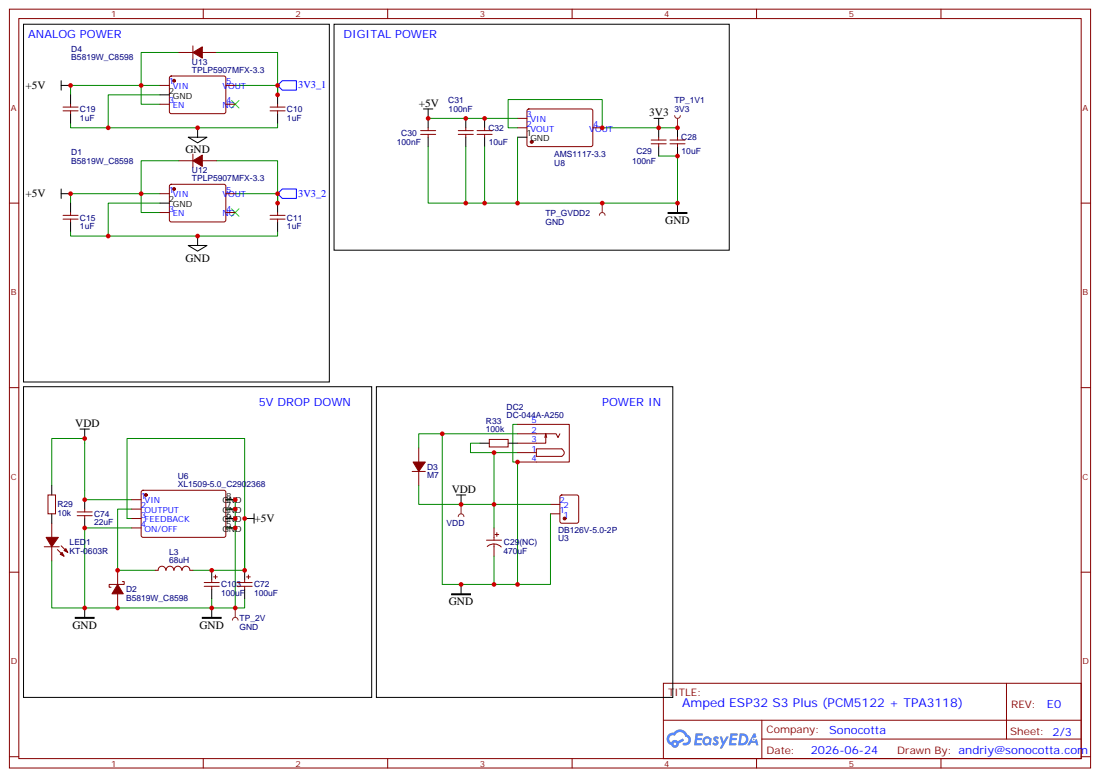
[picture p49: page 3]

Drawn By: andriy@sonocotta.com
