sonocotta/esp32-audio-dock/hardware/9-louder-esp32-mini/rev-b-55mm/2606-louder-esp32-mini-pd-b-pcb.pdf

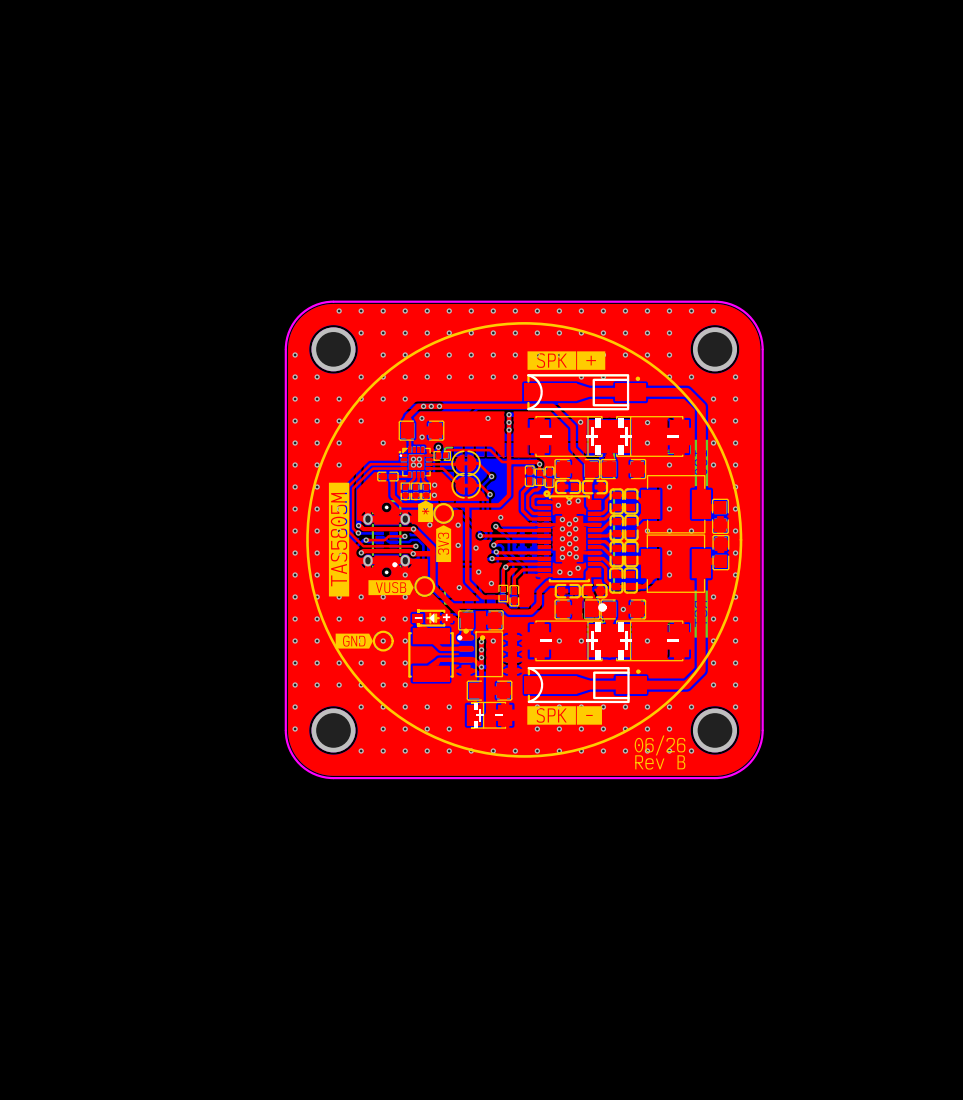
[picture p50: page 1]
