sonocotta/esp32-audio-dock/hardware/9-louder-esp32-mini/rev-b-55mm/2606-louder-esp32-mini-pd-b-schematic.pdf

## DAC

## MCU

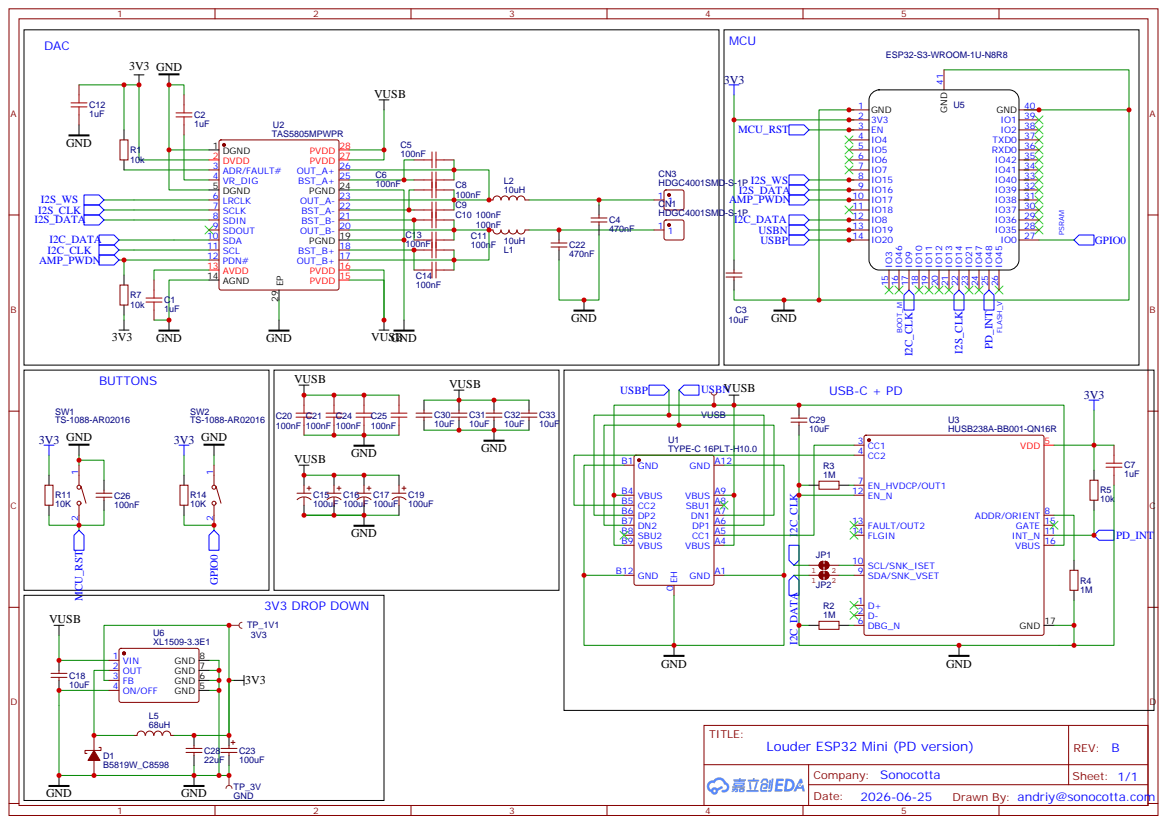
[picture p51: page 1]

Drawn By: andriy@sonocotta.com
