sonocotta/esp32-audio-dock/hardware/9-louder-esp32-mini/rev-b1-55mm/2607-louder-esp32-mini-pd-b1-pcb.pdf

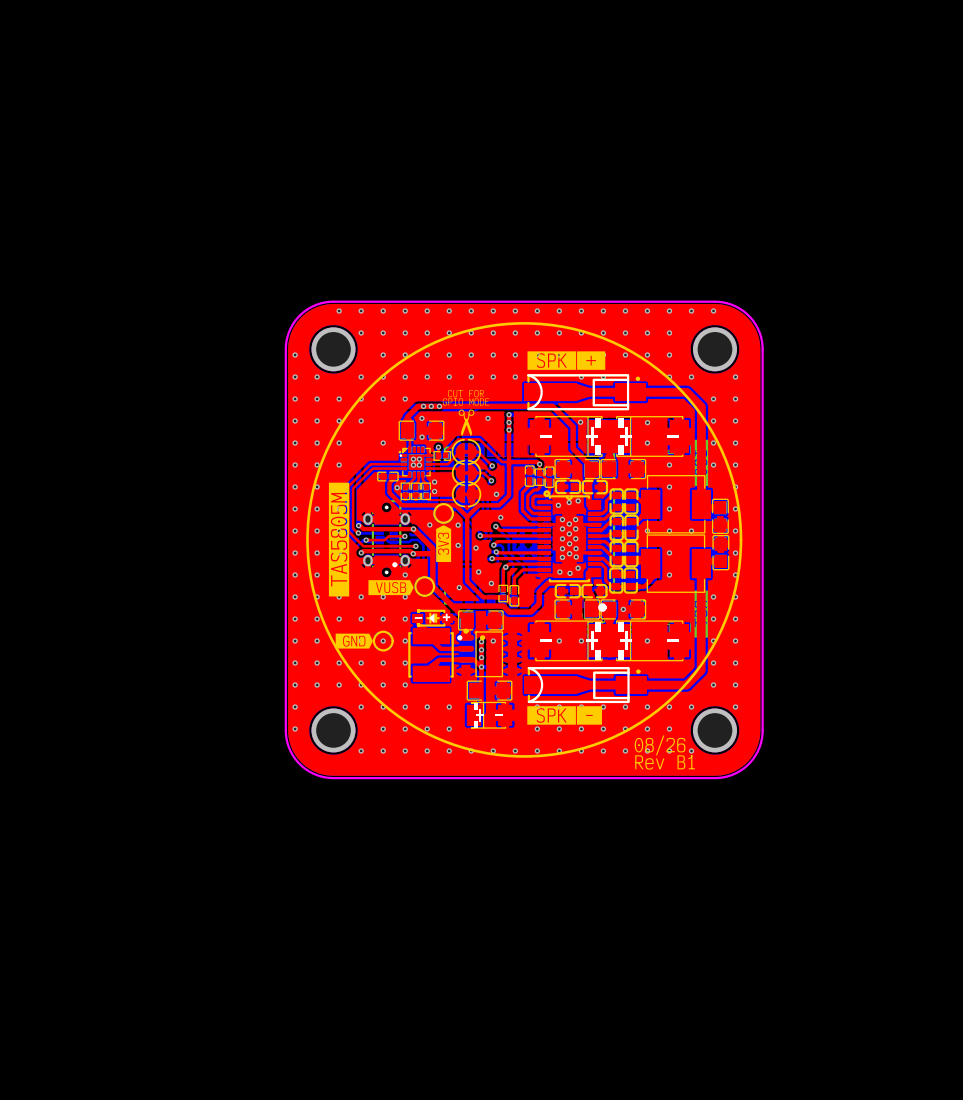
[picture p52: page 1]
