sonocotta/esp32-audio-dock/hardware/9-louder-esp32-mini/rev-b1-55mm/2607-louder-esp32-mini-pd-b1-schematic.pdf

## DAC

## MCU

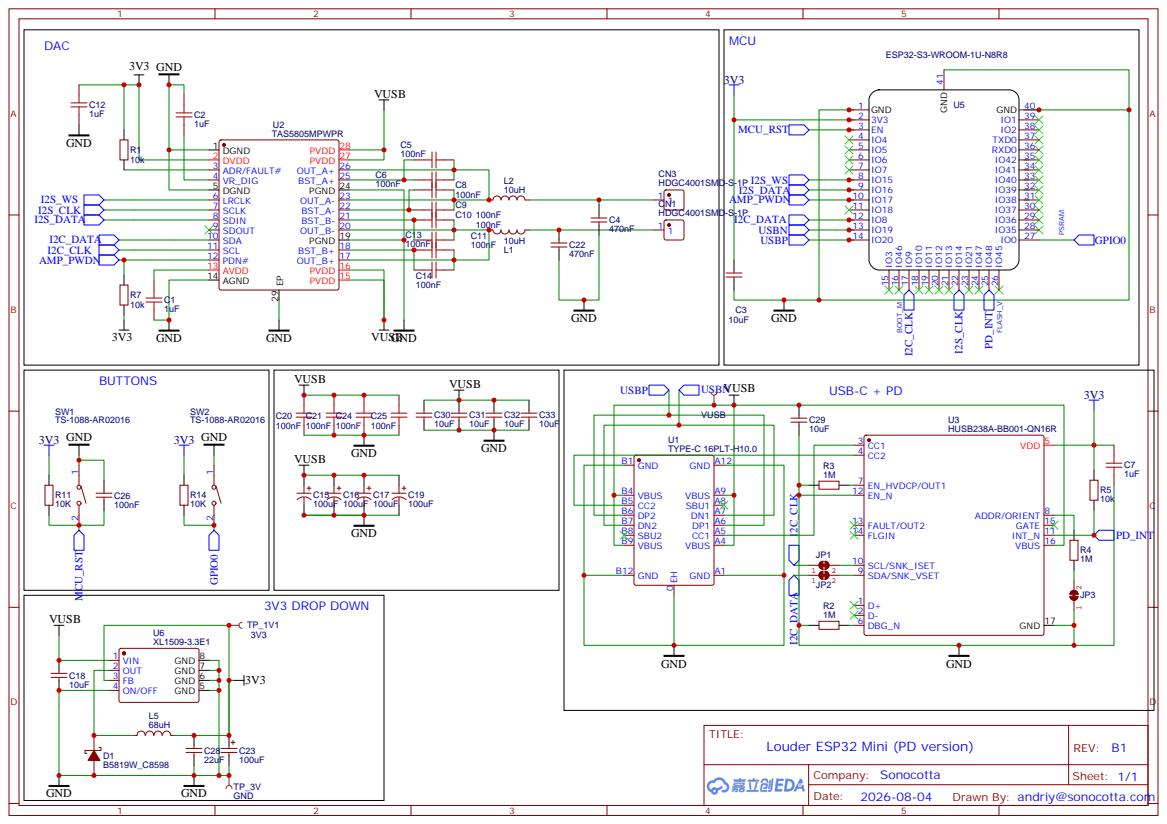
[picture p53: page 1]

Drawn By: andriy@sonocotta.com
