sonocotta/esp32-audio-dock/hardware/10-louder-esp32-pro/rev-c-pd-edition/2605-louder-esp32s3-plus-pd-c-pcb.pdf

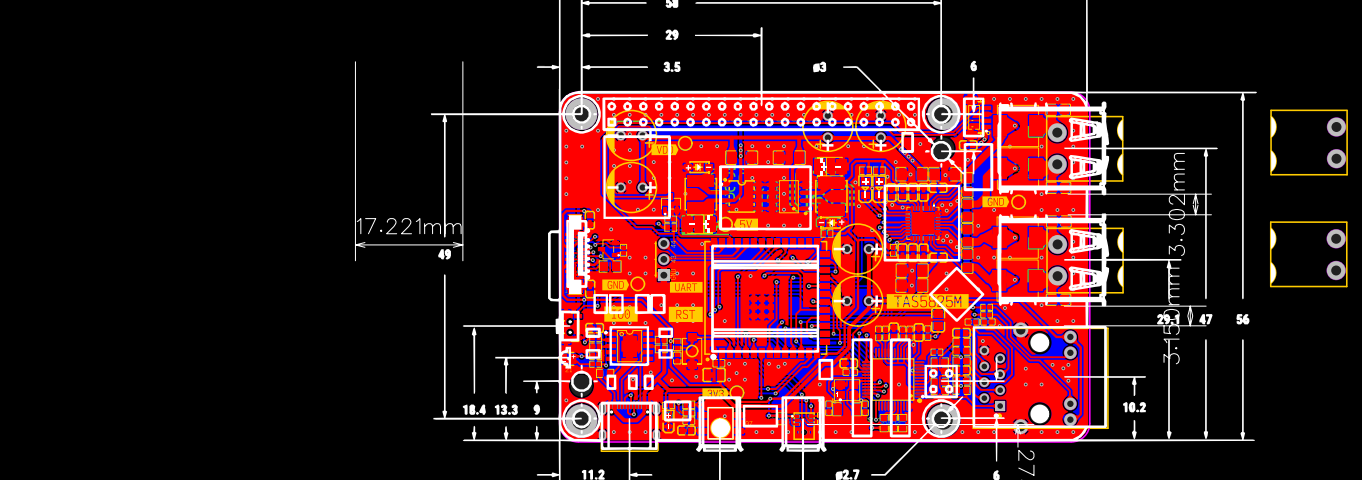
[picture p54: page 1]
