sonocotta/esp32-audio-dock/hardware/4-amped-esp32/rev-k0/2605-amped-esp32s3-k0-pcb.pdf

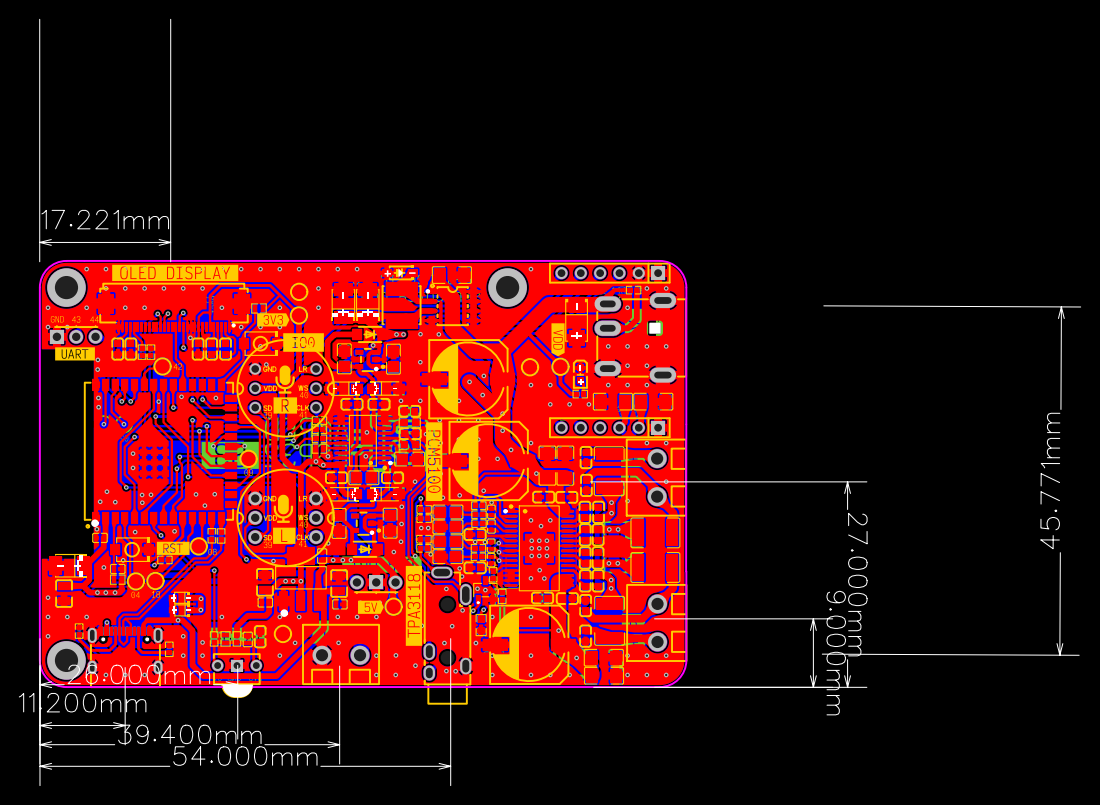
[picture p55: page 1]
