sonocotta/esp32-audio-dock/hardware/4-amped-esp32/rev-k0/2605-amped-esp32s3-k0-schematic.pdf

# IO20 14IO19 13IO8 12IO18 11IO17 10IO16 9

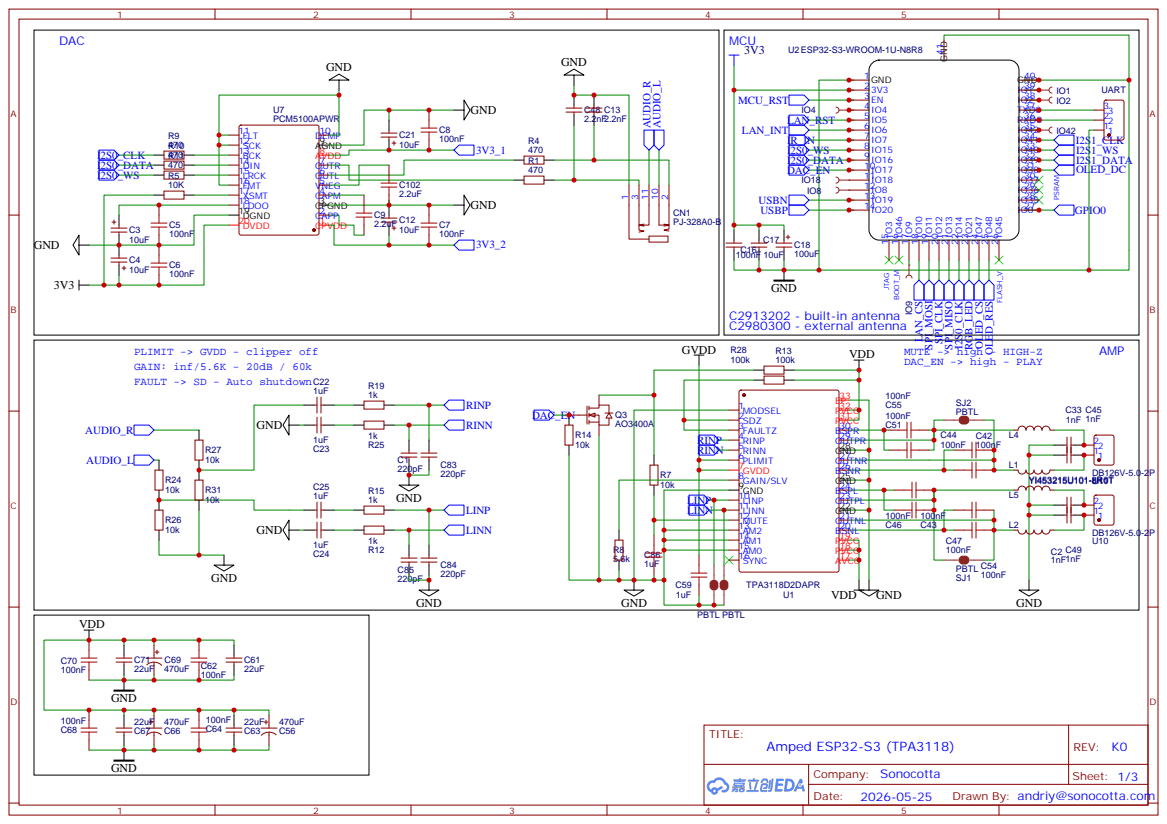
[picture p56: page 1]

PLIMIT -> GVDD - clipper off
GAIN: inf/5.6K - 20dB / 60k
FAULT -> SD - Auto shutdown

Drawn By: andriy@sonocotta.com

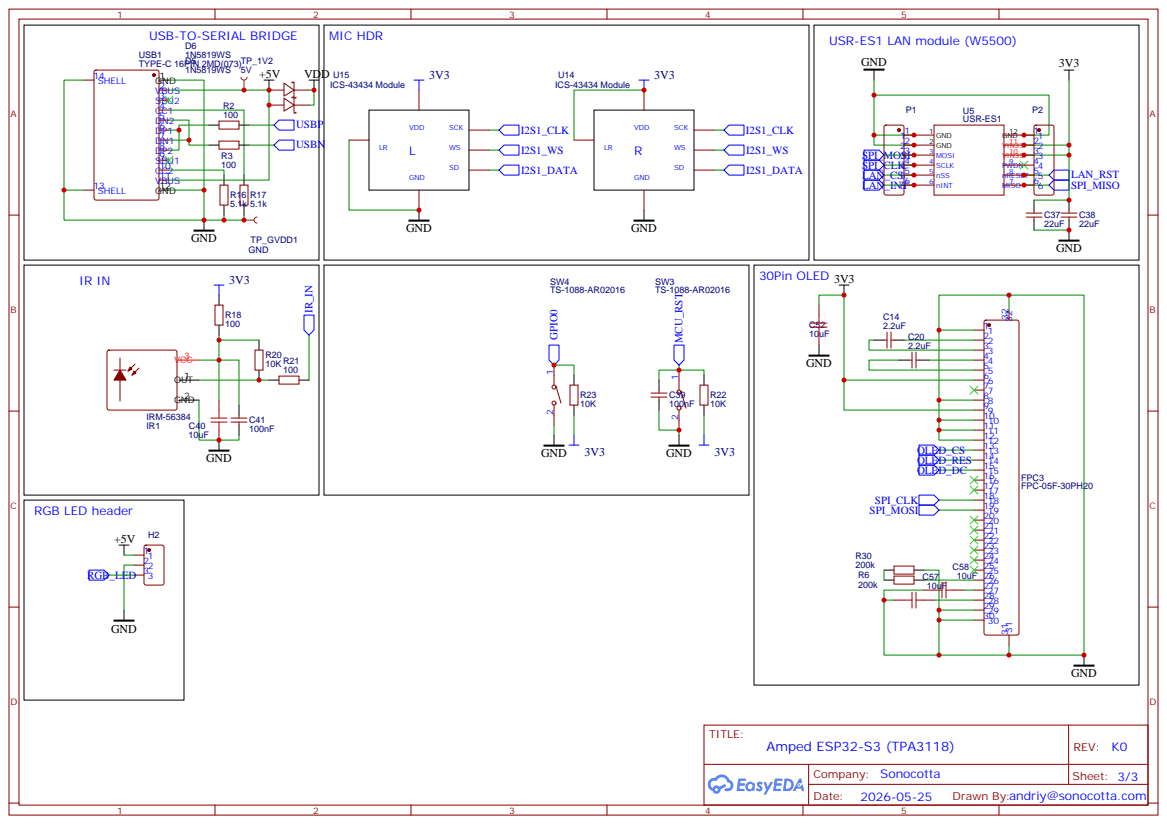
[picture p57: page 2]

Drawn By:andriy@sonocotta.com

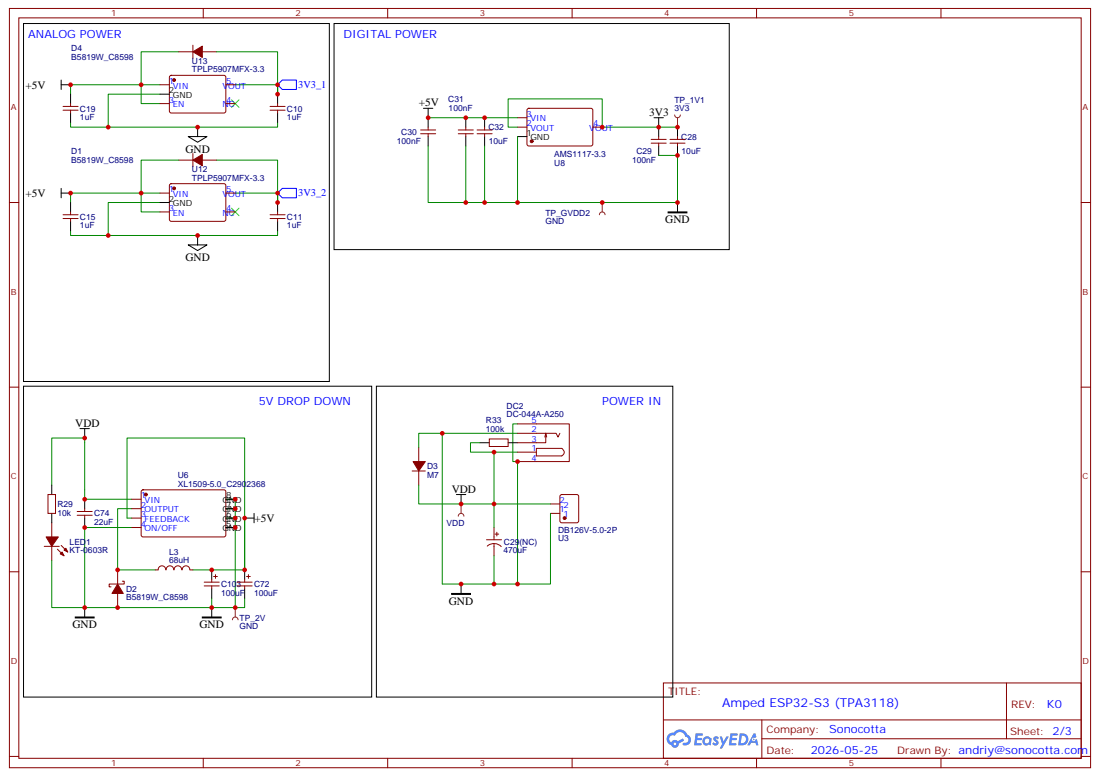
[picture p58: page 3]

Drawn By: andriy@sonocotta.com
