sonocotta/esp32-audio-dock/hardware/5-hifi-esp32-plus/rev-h2/2605-hifi-esp32s3-plus-h2-pcb.pdf

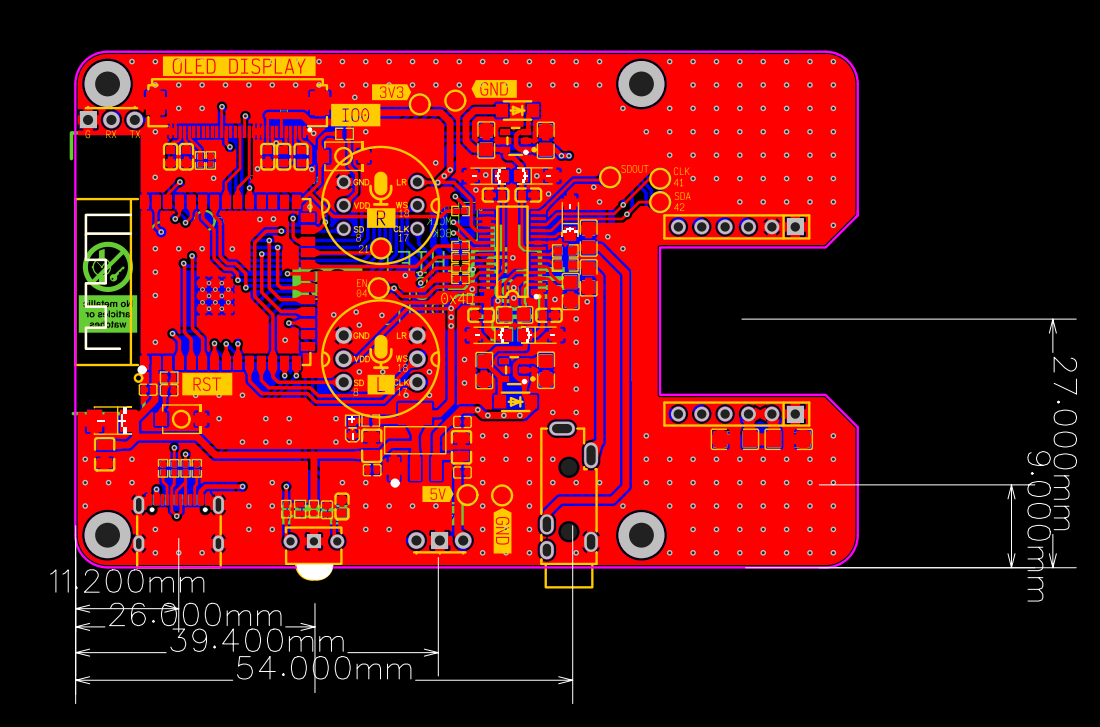
[picture p59: page 1]
