sonocotta/esp32-audio-dock/hardware/6-loud-esp32-plus/rev-a1-s3/2605-loud-esp32s3-plus-a1-pcb.pdf

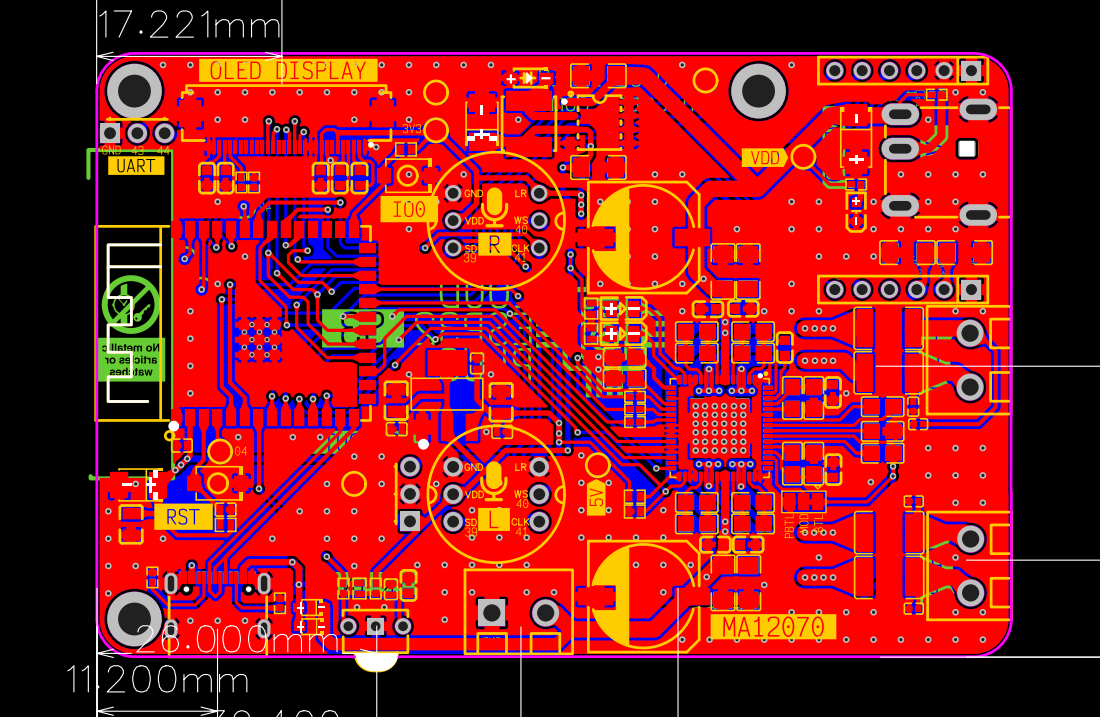
[picture p60: page 1]
