sonocotta/esp32-audio-dock/hardware/6-loud-esp32-plus/rev-a1-s3/2605-loud-esp32s3-plus-a1-schematic.pdf

CLK 32 ENABLE# 33 MUTE# 34 PVSS 35 PVSS 36 CF1BN 37 OUT1B 38 OUT1B 39 CF1BP 40 PVDD 41 PVDD 42 CF1AP 43 OUT1A 44 OUT1A 45 CF1AN 46 PVSS 47 PVSS 48 NC49 MSEL1 50 MSEL0 51 CGD1N 52 CGD1P 53 VGDC 54 DVDD 55 CDC 56 CFDCP 57 CFDCN 58 DVSS 59 CGD0P 60 CGD0N 61 CFGDP 62 CFGDN 63 NC64 EP65

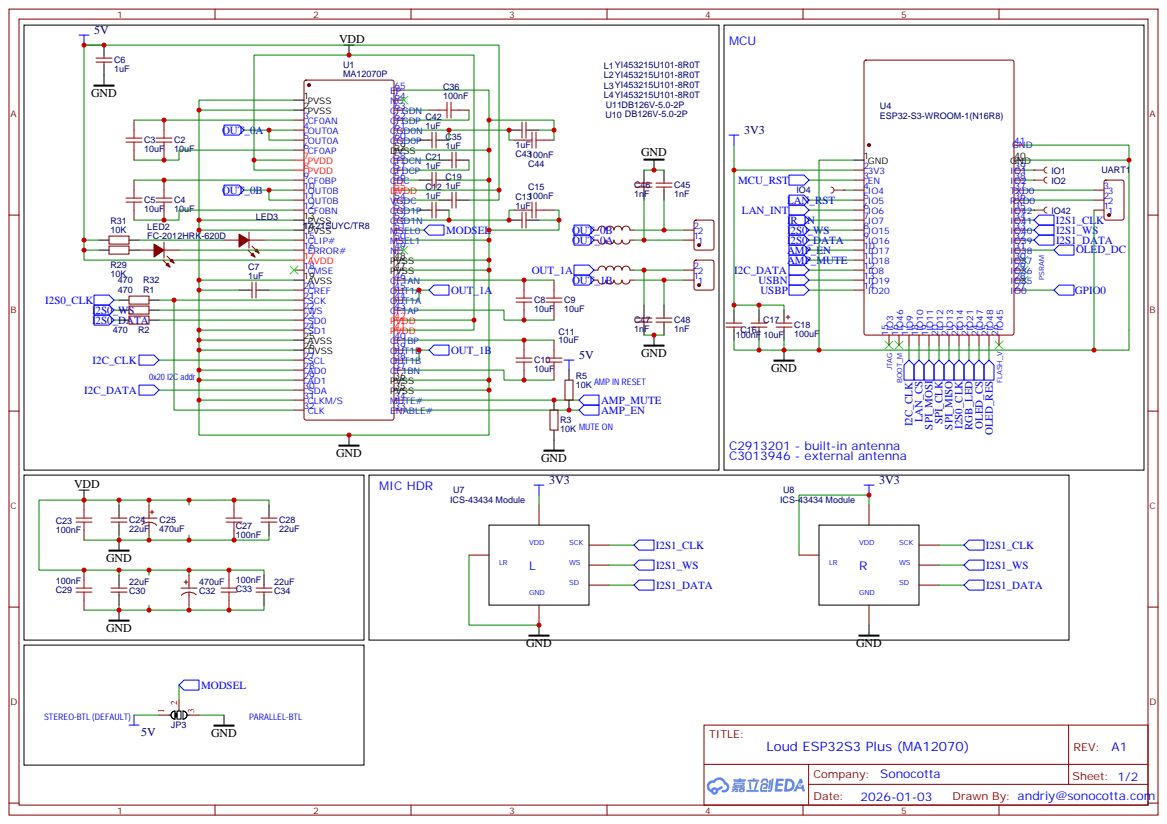
[picture p61: page 1]

Drawn By: andriy@sonocotta.com

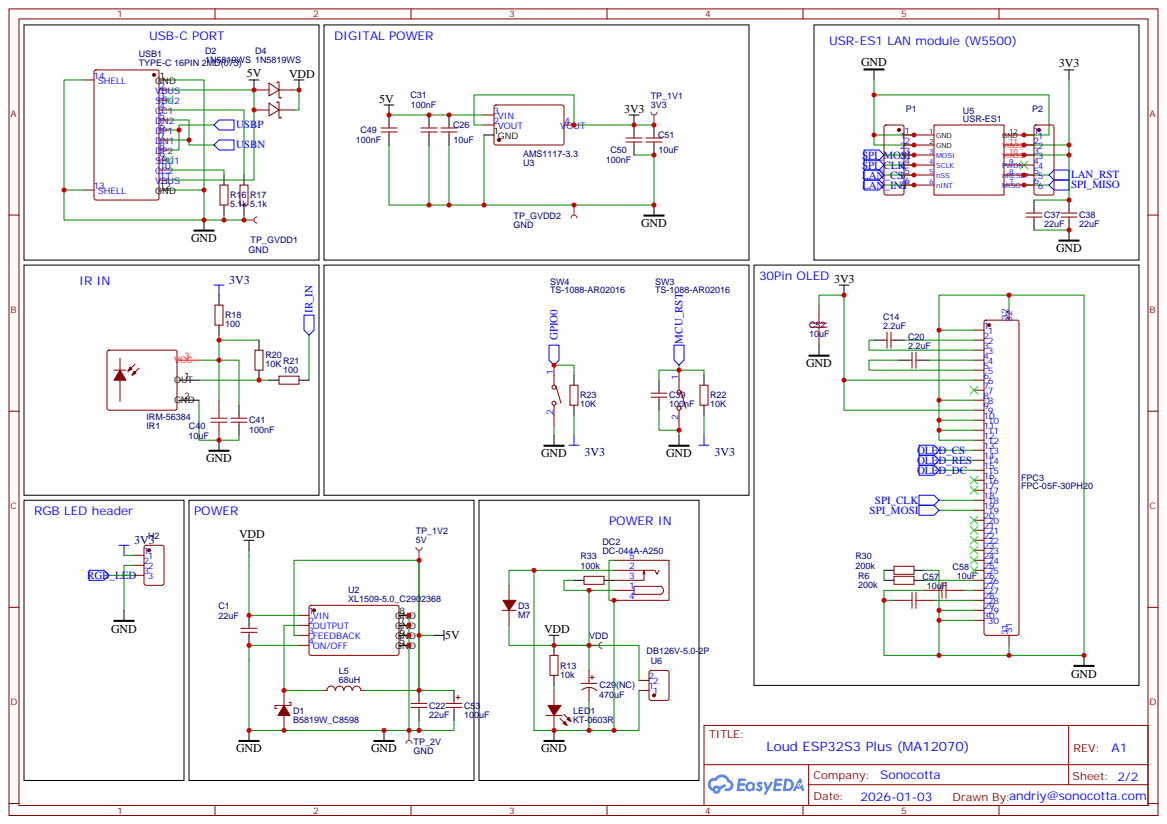
[picture p62: page 2]

Drawn By:andriy@sonocotta.com
