sonocotta/esp32-audio-dock/hardware/6-loud-esp32-plus/rev-b0/2605-loud-esp32-plus-b0-pcb.pdf

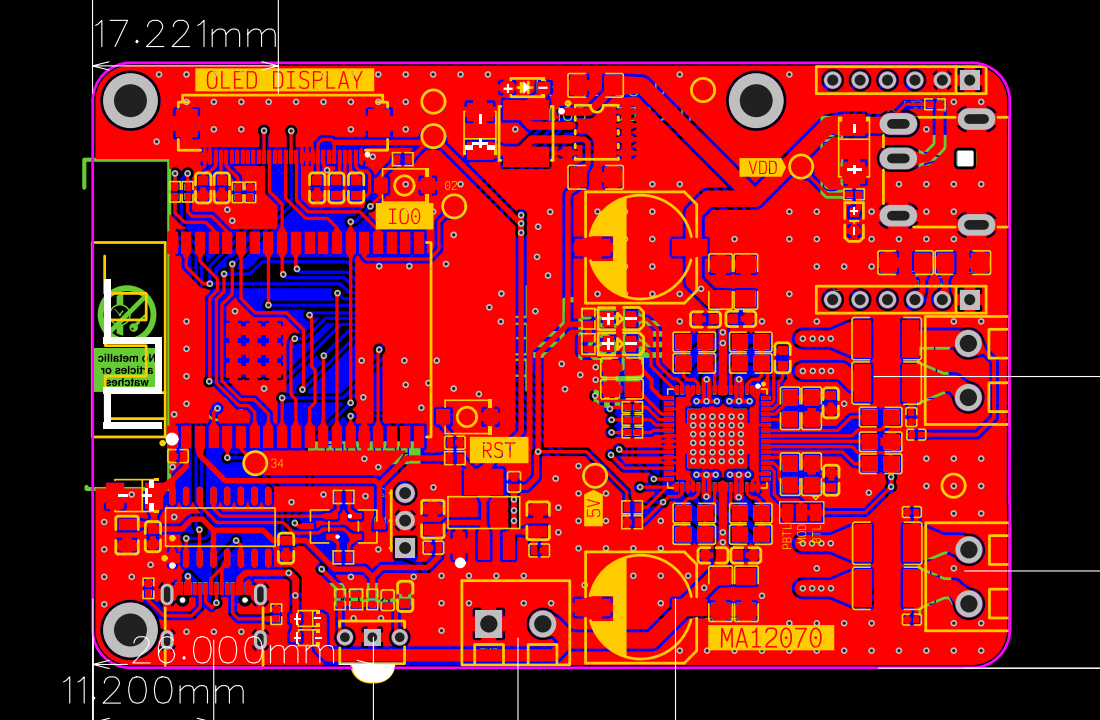
[picture p63: page 1]
