sonocotta/esp32-audio-dock/hardware/7-louder-esp32-plus/rev-a1-s3/2605-louder-esp32s3-plus-a1-pcb.pdf

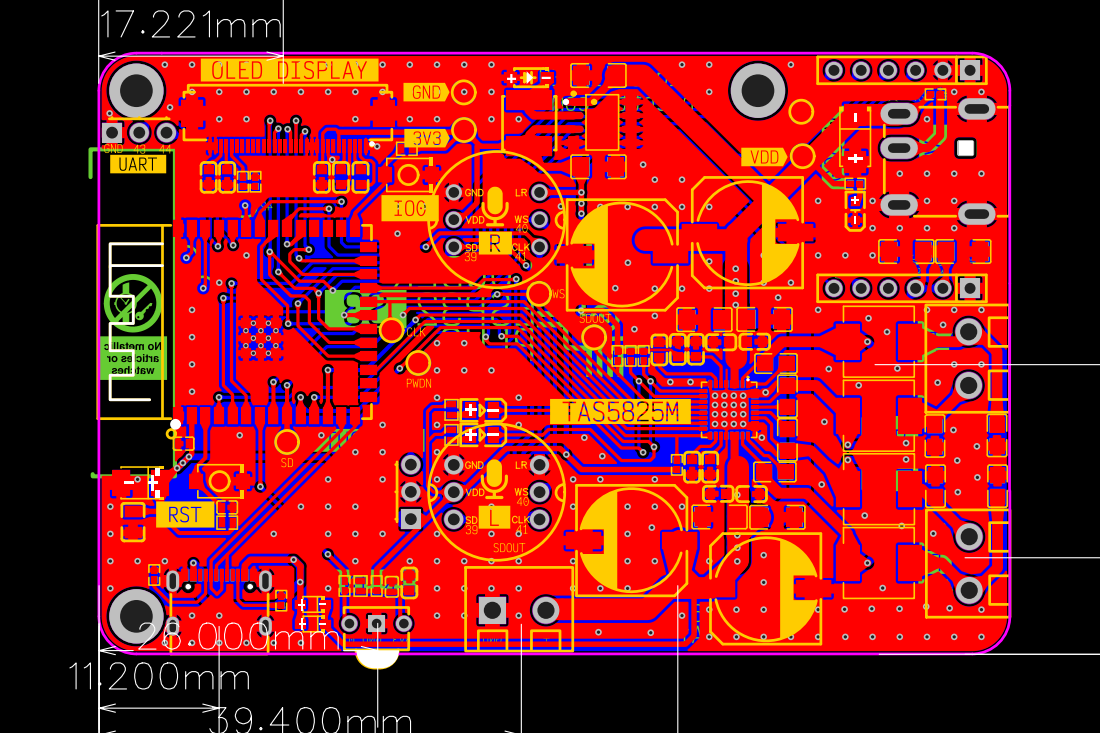
[picture p66: page 1]
