sonocotta/esp32-audio-dock/hardware/7-louder-esp32-plus/rev-a1-s3/2605-louder-esp32s3-plus-a1-schematic.pdf

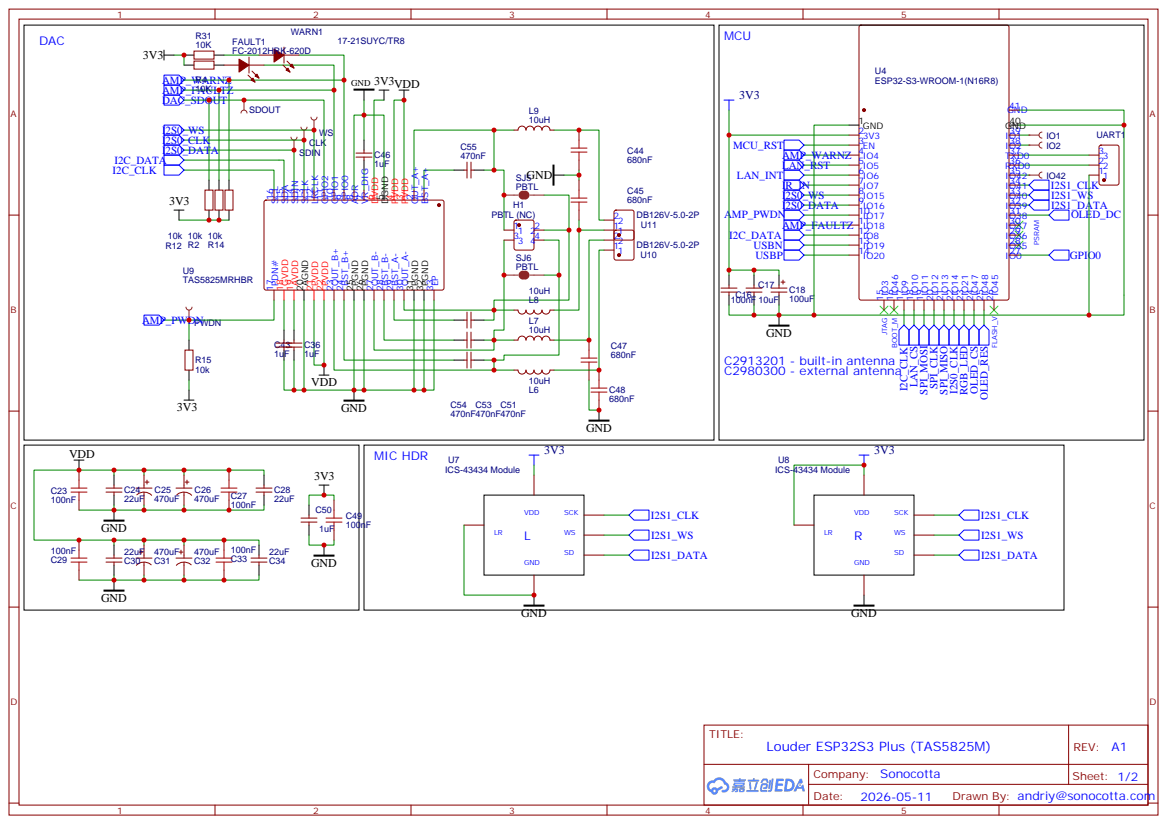
[picture p67: page 1]

9GPIO1 10 GPIO2 11 LRCLK 12 SCLK 13 SDIN 14 SDA 15 SCL 16 PDN# 17GVDD 18AVDD 19AGND 20PVDD 21PVDD 22OUT_B+ 23BST_B+ 24

Drawn By: andriy@sonocotta.com

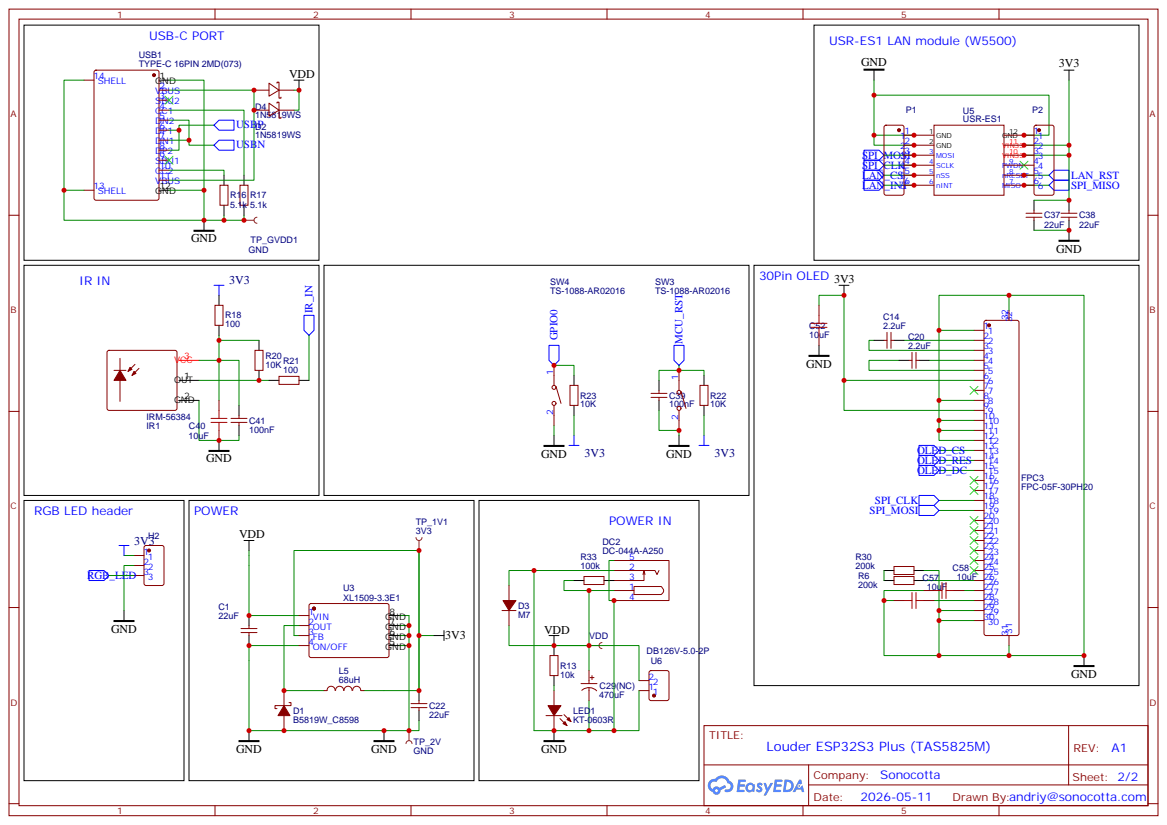
[picture p68: page 2]

Drawn By:andriy@sonocotta.com
