sonocotta/esp32-audio-dock/hardware/9-louder-esp32-mini/rev-a-42mm/2605-louder-esp32-mini-a-schematic.pdf

## DAC

## MCU

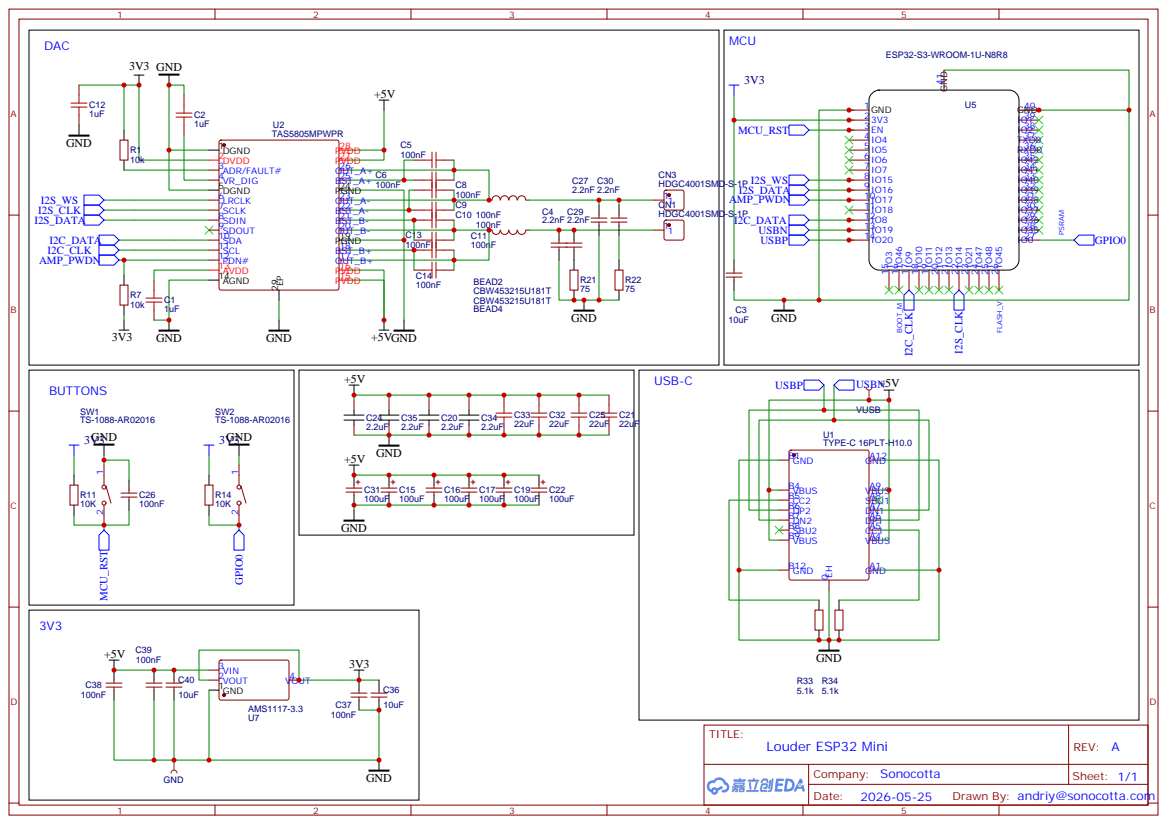
[picture p69: page 1]

Drawn By: andriy@sonocotta.com
