sonocotta/esp32-audio-dock/hardware/9-louder-esp32-mini/rev-a-42mm/2605-louder-esp32-mini-pcb.pdf

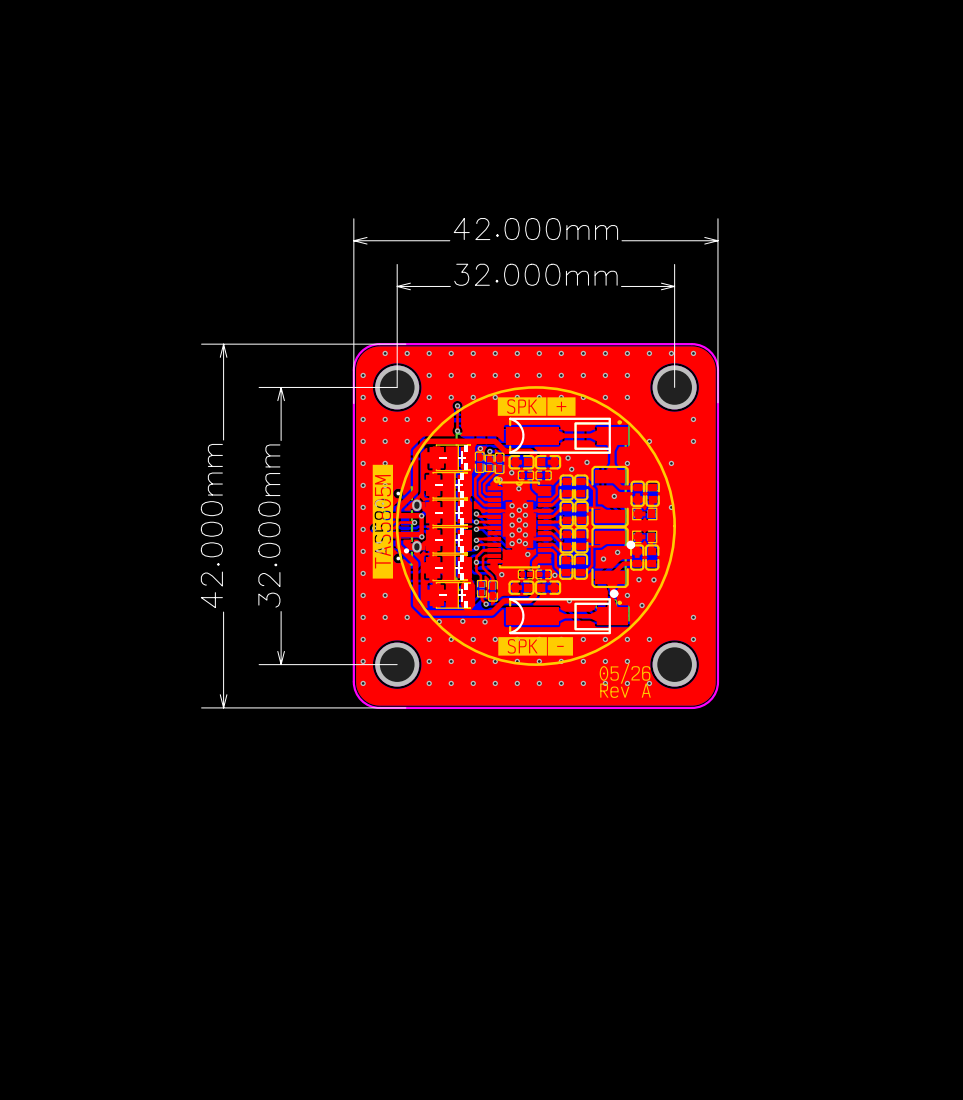
[picture p70: page 1]
