sonocotta/esp32-audio-dock/hardware/1-hifi-esp32/rev-g3/2603-hifi-esp32s3-g3-pcb.pdf

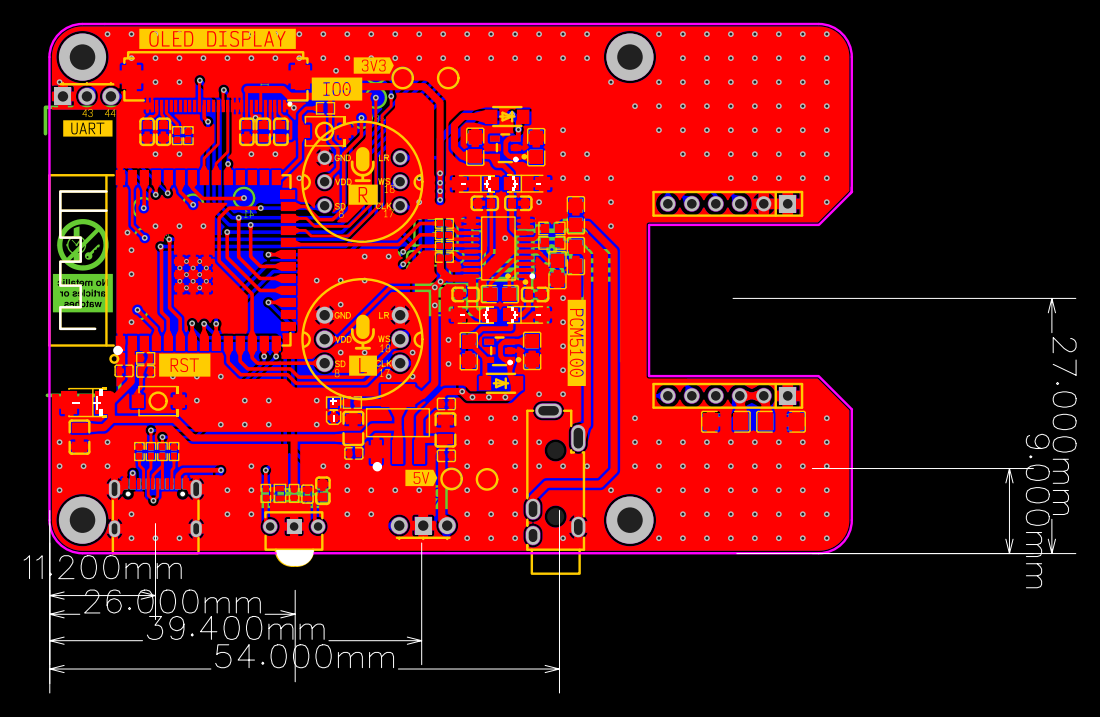
[picture p71: page 1]
