sonocotta/esp32-audio-dock/hardware/1-hifi-esp32/rev-g3/2603-hifi-esp32s3-g3-schematic.pdf

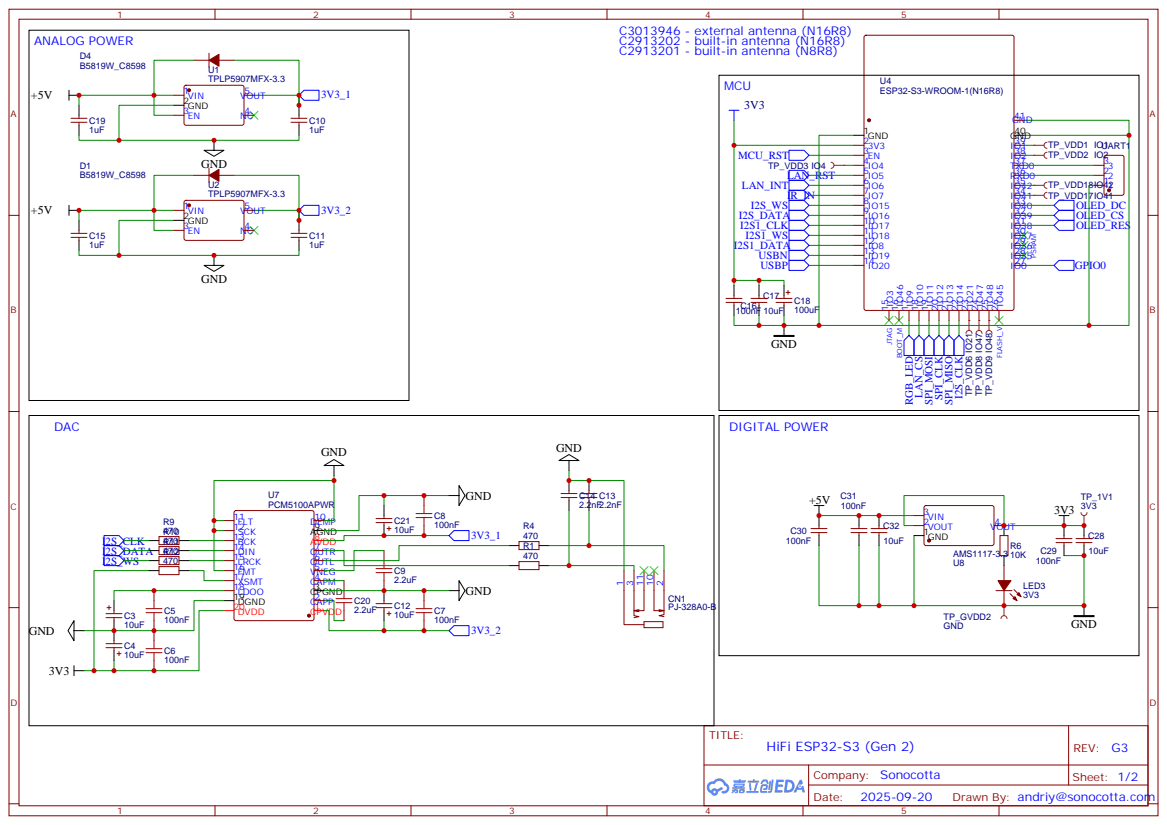
[picture p72: page 1]

Drawn By: andriy@sonocotta.com

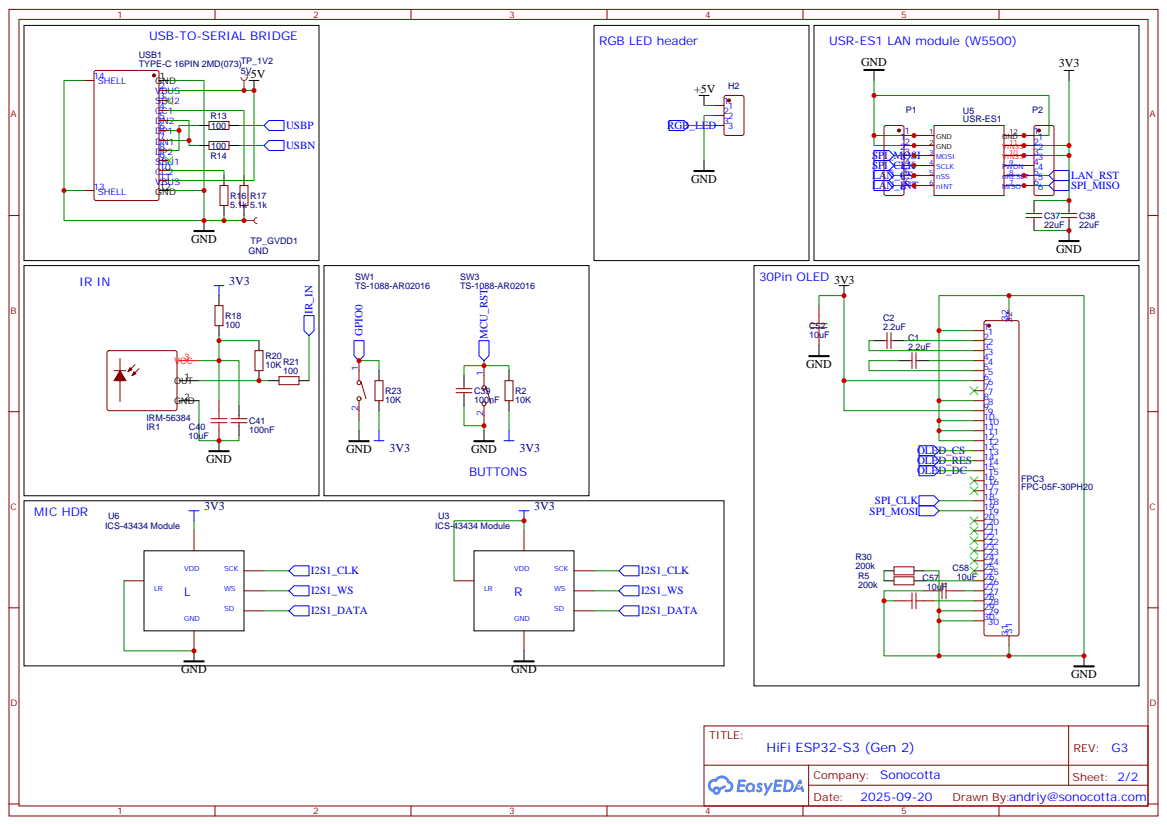
[picture p73: page 2]

Drawn By:andriy@sonocotta.com
