sonocotta/esp32-audio-dock/hardware/2-loud-esp32/rev-e3/2603-loud-esp32-e3-pcb.pdf

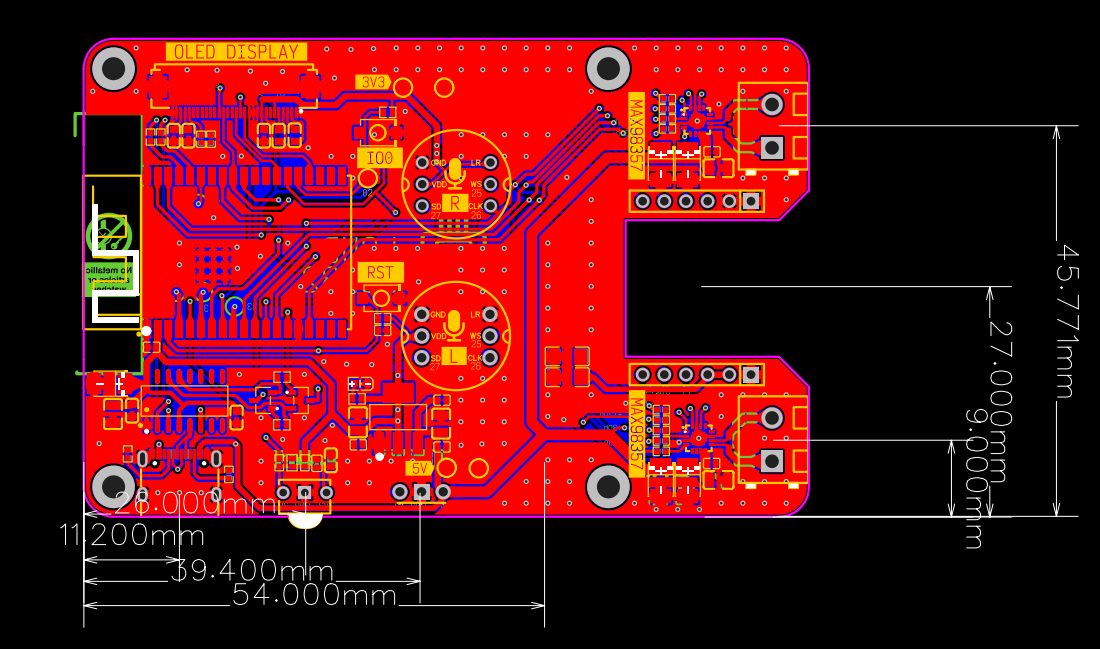
[picture p74: page 1]
