sonocotta/esp32-audio-dock/hardware/2-loud-esp32/rev-g/2603-loud-esp32s3-g-pcb.pdf

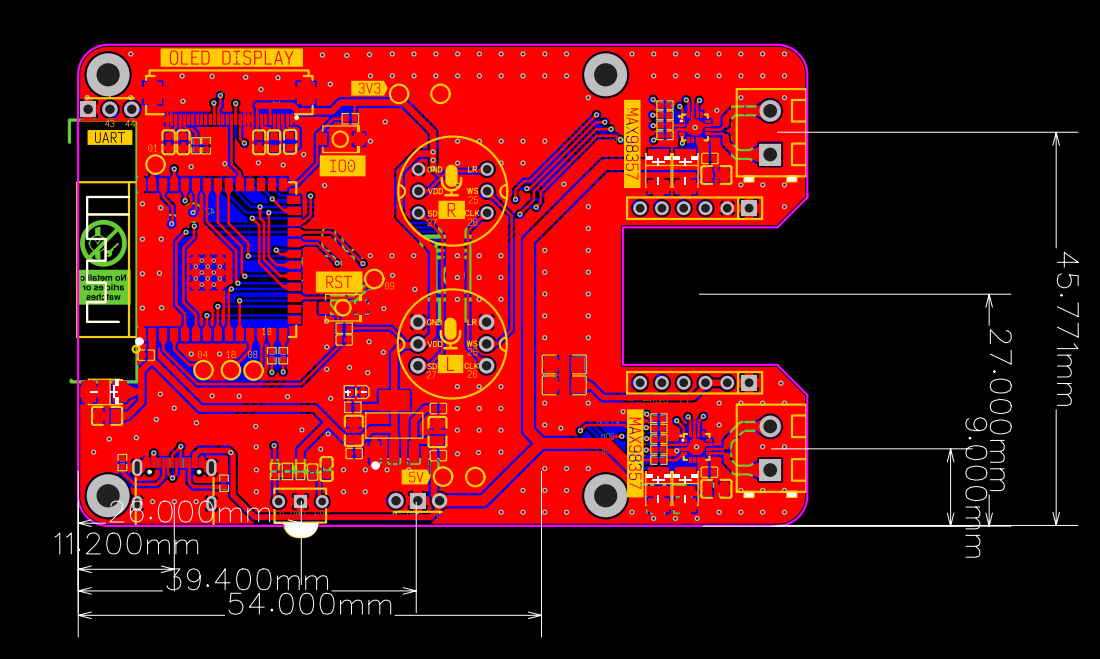
[picture p75: page 1]
