sonocotta/esp32-audio-dock/hardware/7-louder-esp32-plus/rev-b/2602-louder-esp32s3-plus-b-pcb.pdf

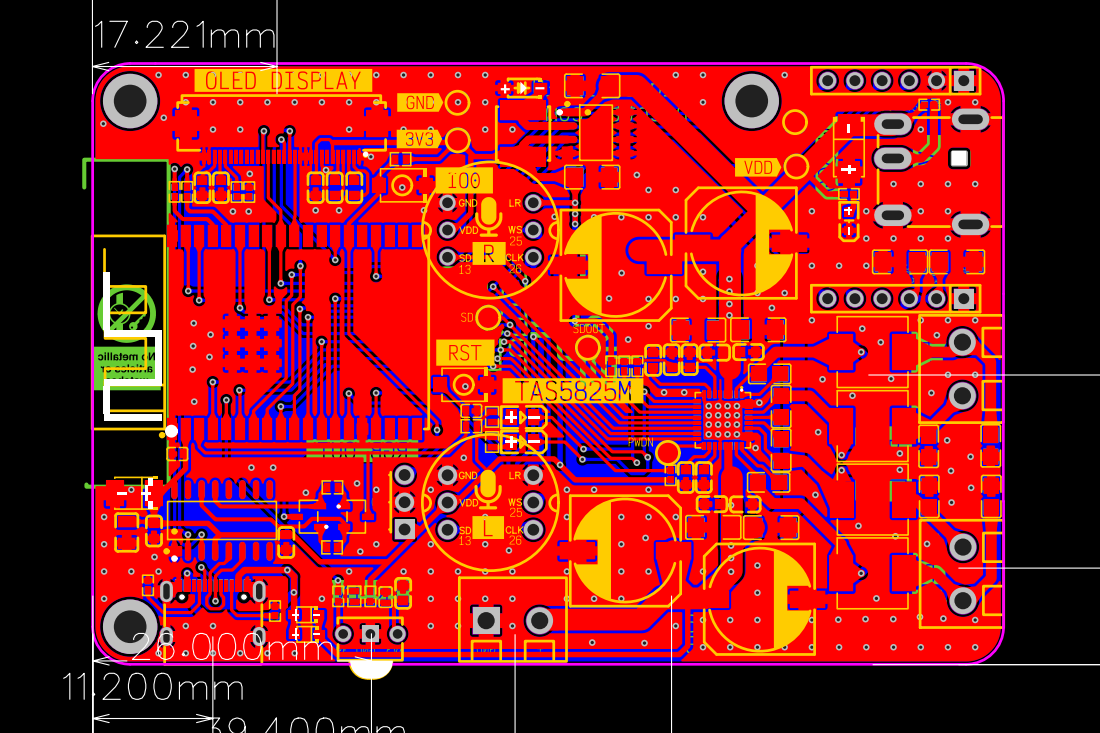
[picture p76: page 1]
