sonocotta/esp32-audio-dock/hardware/8-amped-esp32-plus/rev-c/2602-amped-esp32s3-plus-c-pcb.pdf

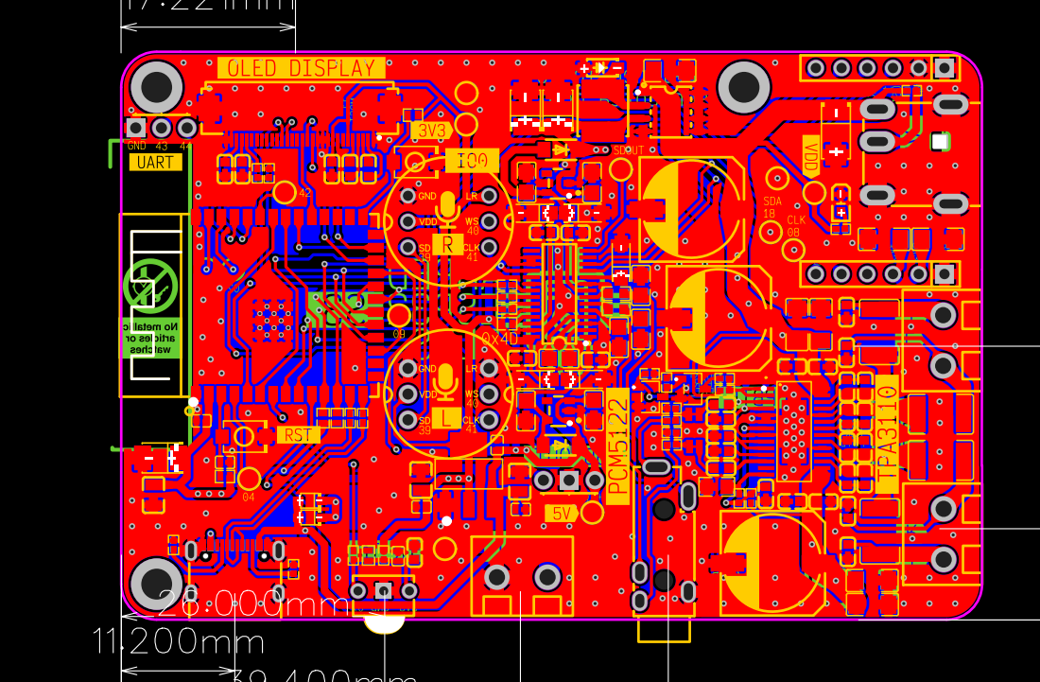
[picture p77: page 1]
