sonocotta/esp32-audio-dock/hardware/8-amped-esp32-plus/rev-c/2602-amped-esp32s3-plus-c-schematic.pdf

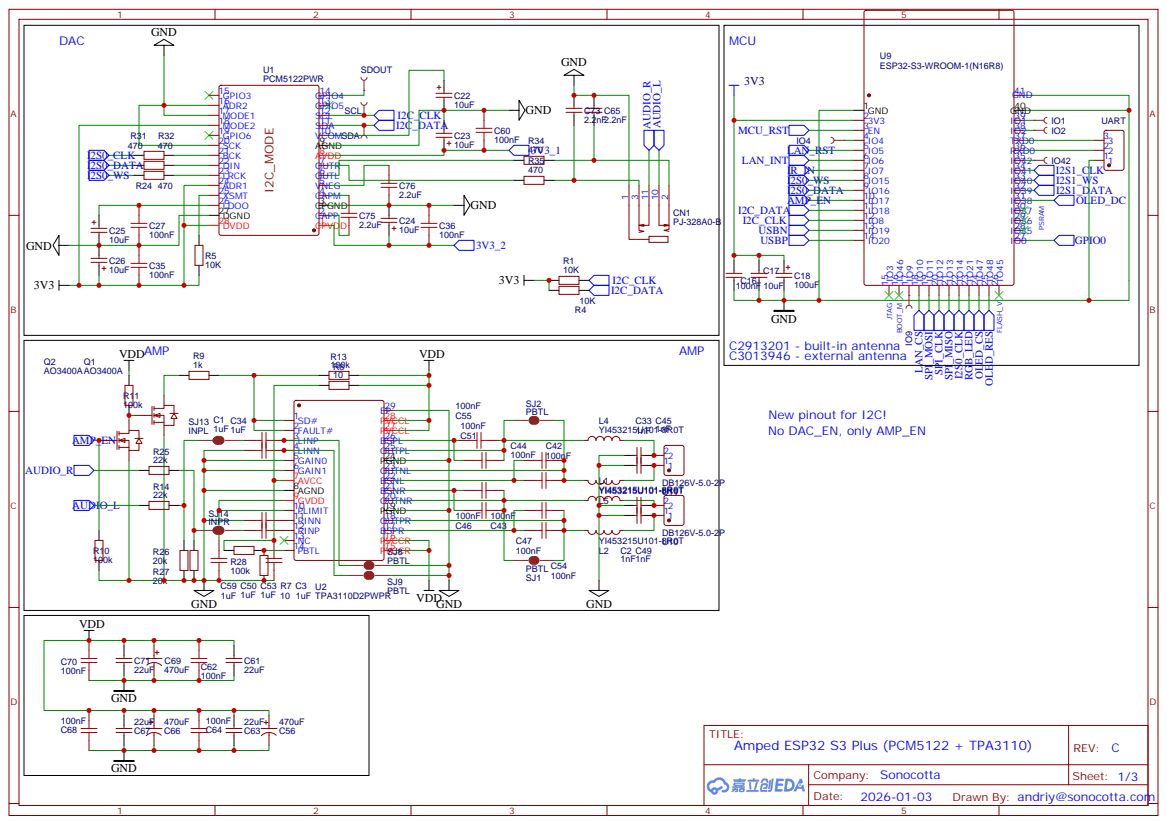
[picture p78: page 1]

Drawn By: andriy@sonocotta.com

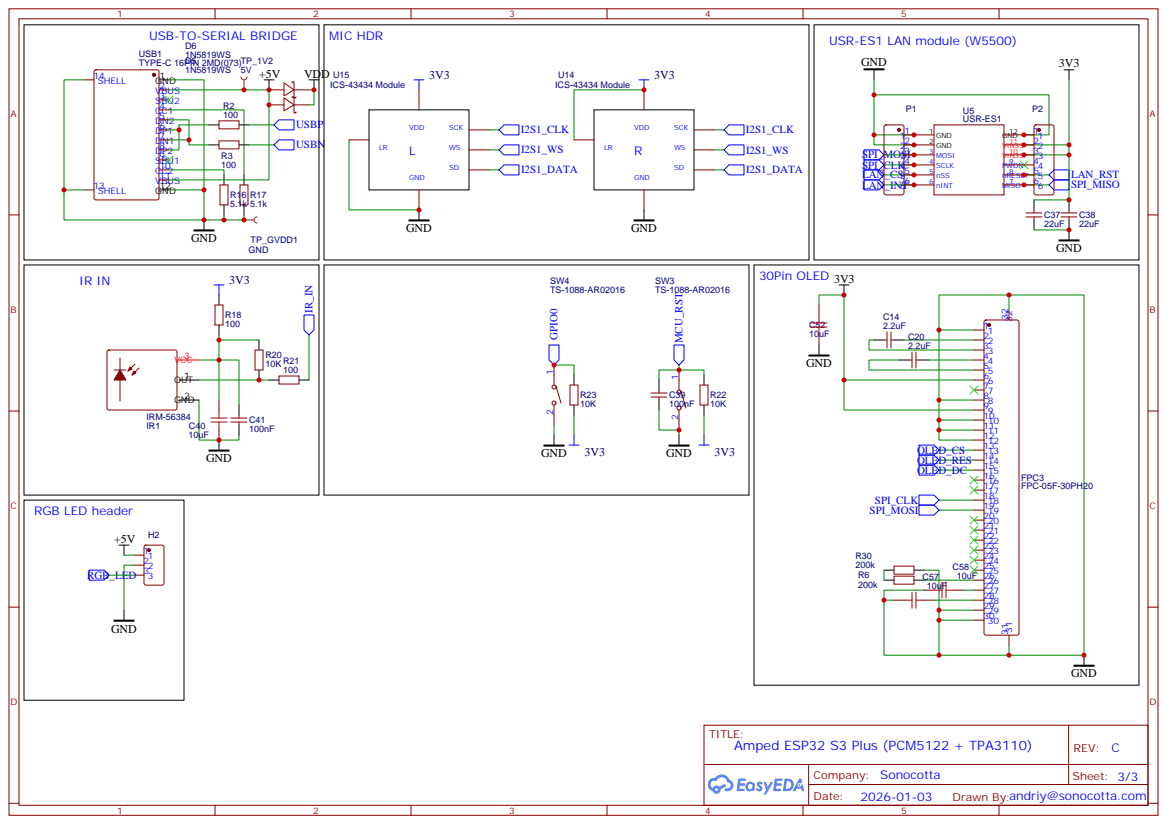
[picture p79: page 2]

Drawn By:andriy@sonocotta.com

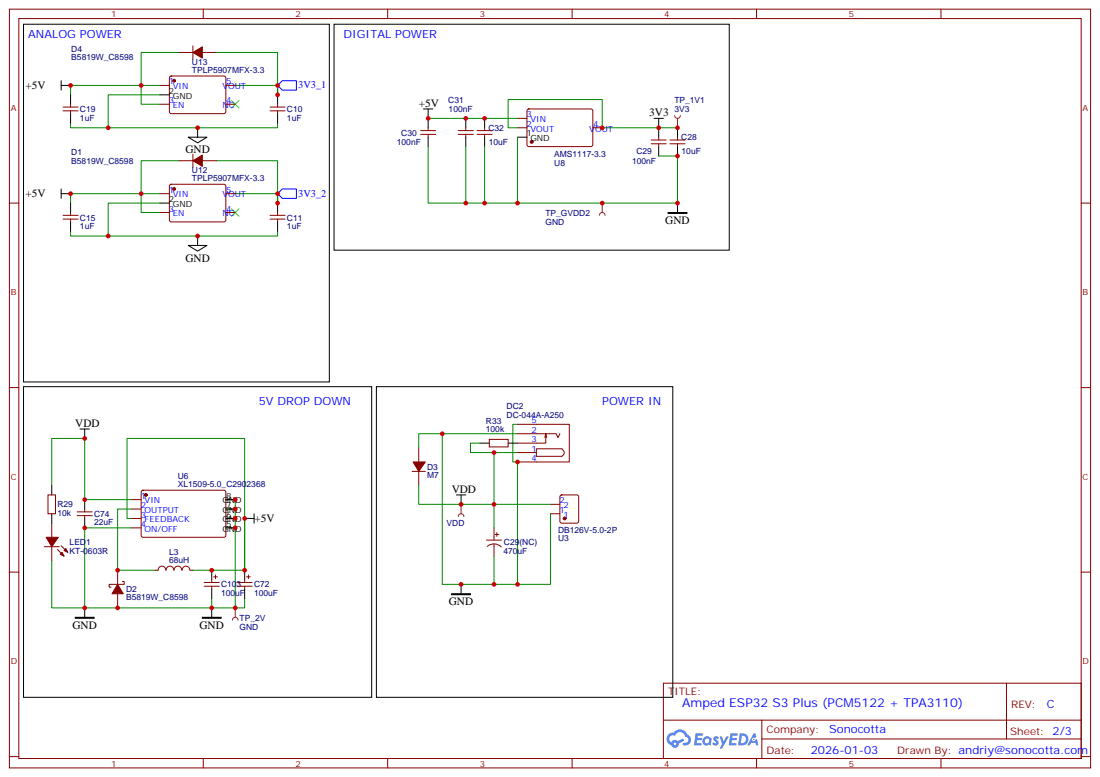
[picture p80: page 3]

Drawn By: andriy@sonocotta.com
