sonocotta/esp32-audio-dock/hardware/3-louder-esp32/rev-k1/2601-louder-esp32s3-k1-pcb.pdf

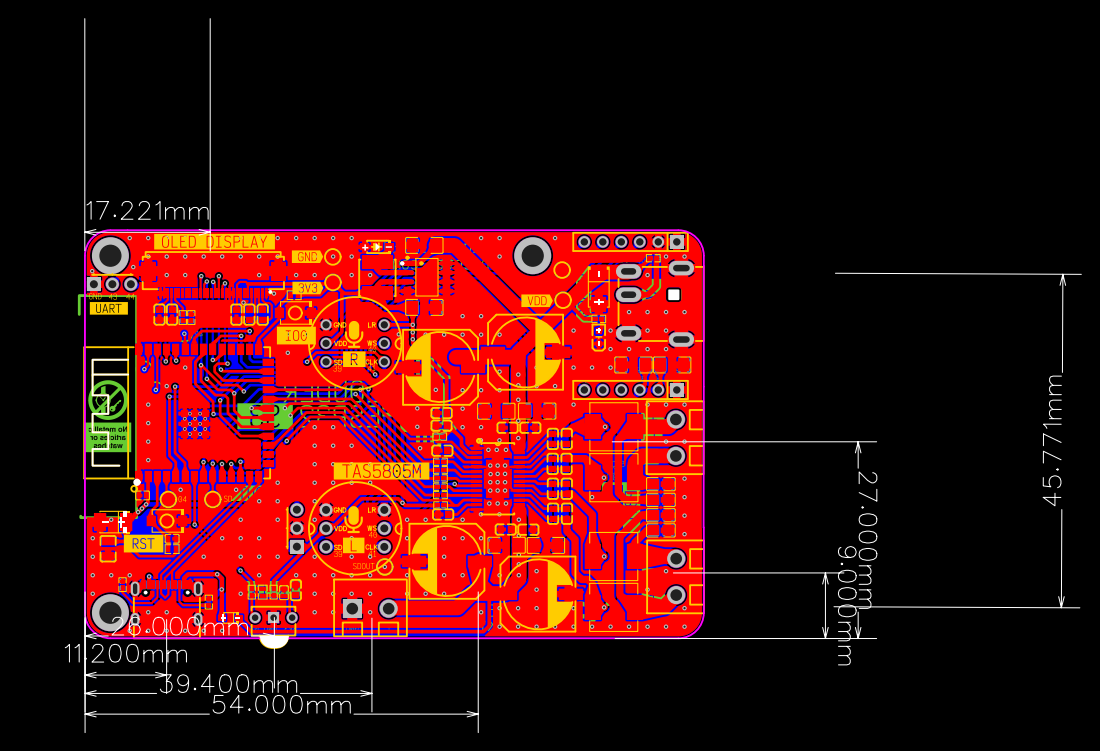
[picture p81: page 1]
