sonocotta/esp32-audio-dock/hardware/3-louder-esp32/rev-k1/2601-louder-esp32s3-k1-schematic.pdf

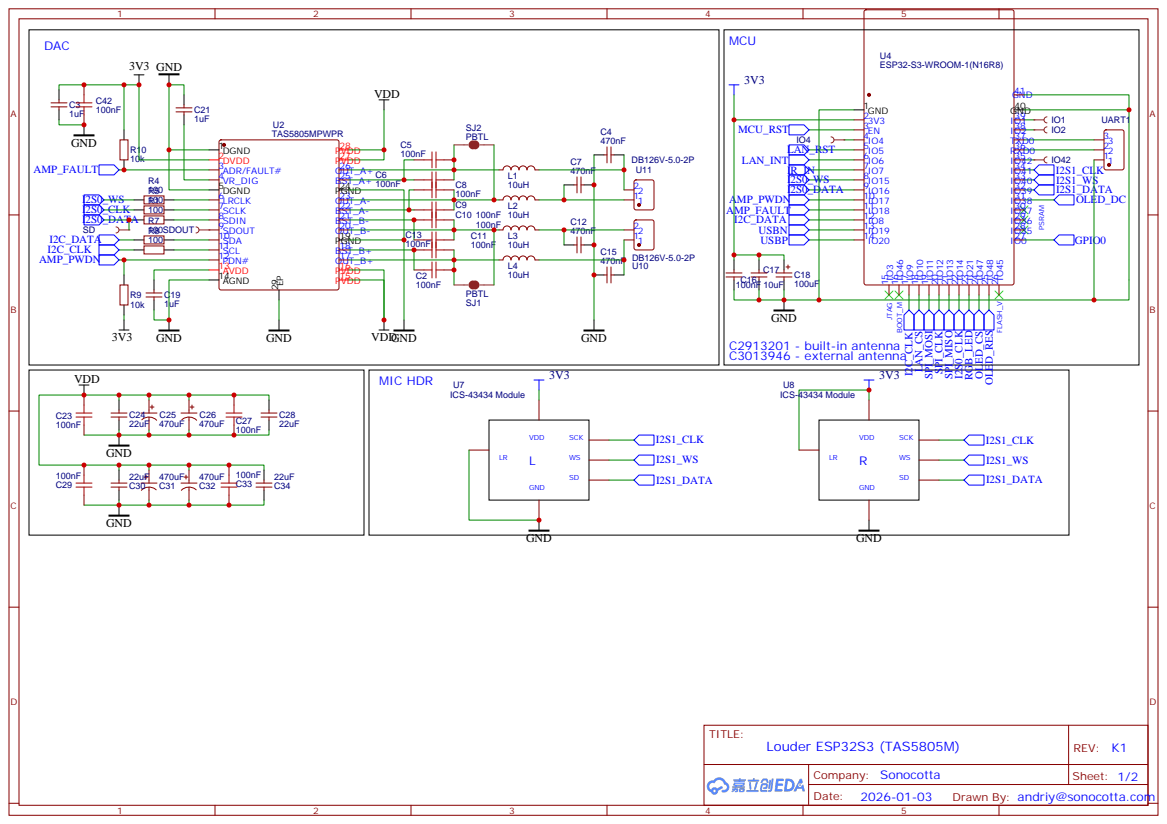
[picture p82: page 1]

Drawn By: andriy@sonocotta.com

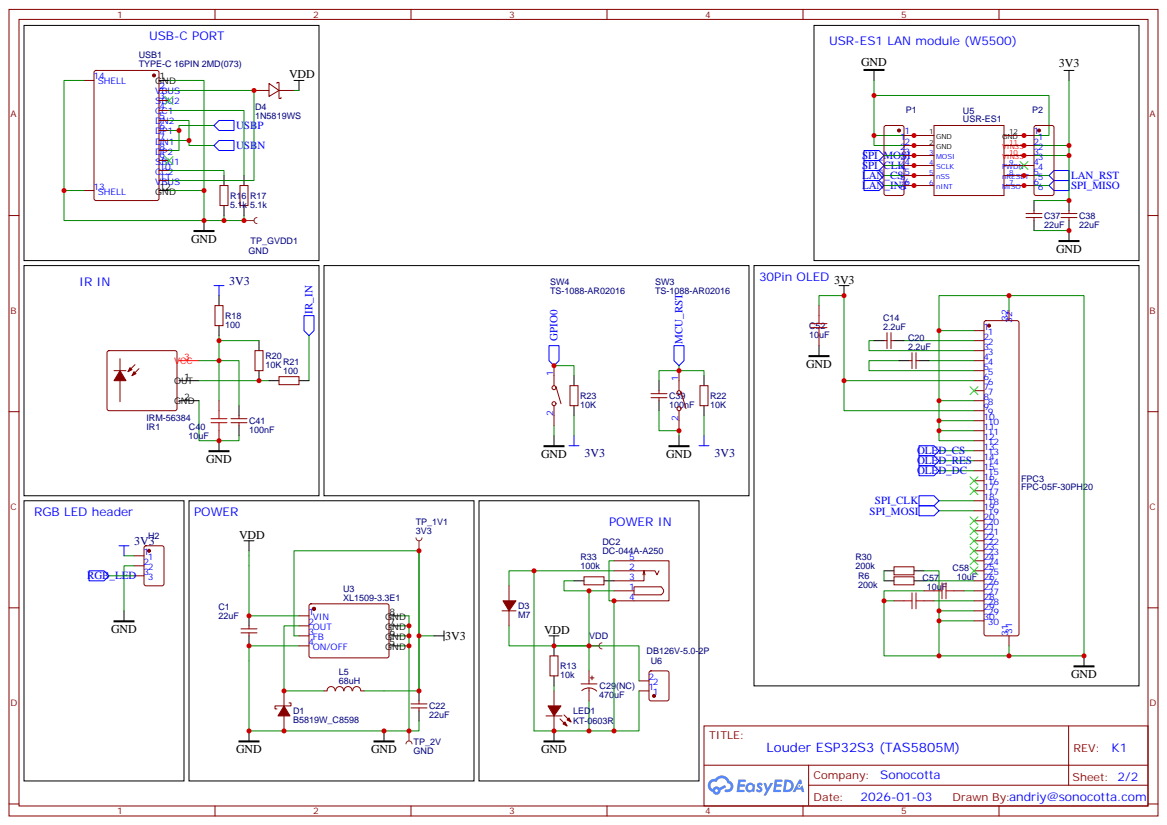
[picture p83: page 2]

Drawn By:andriy@sonocotta.com
