sonocotta/esp32-audio-dock/hardware/6-loud-esp32-plus/rev-a-s3/2601-loud-esp32s3-plus-a-pcb.pdf

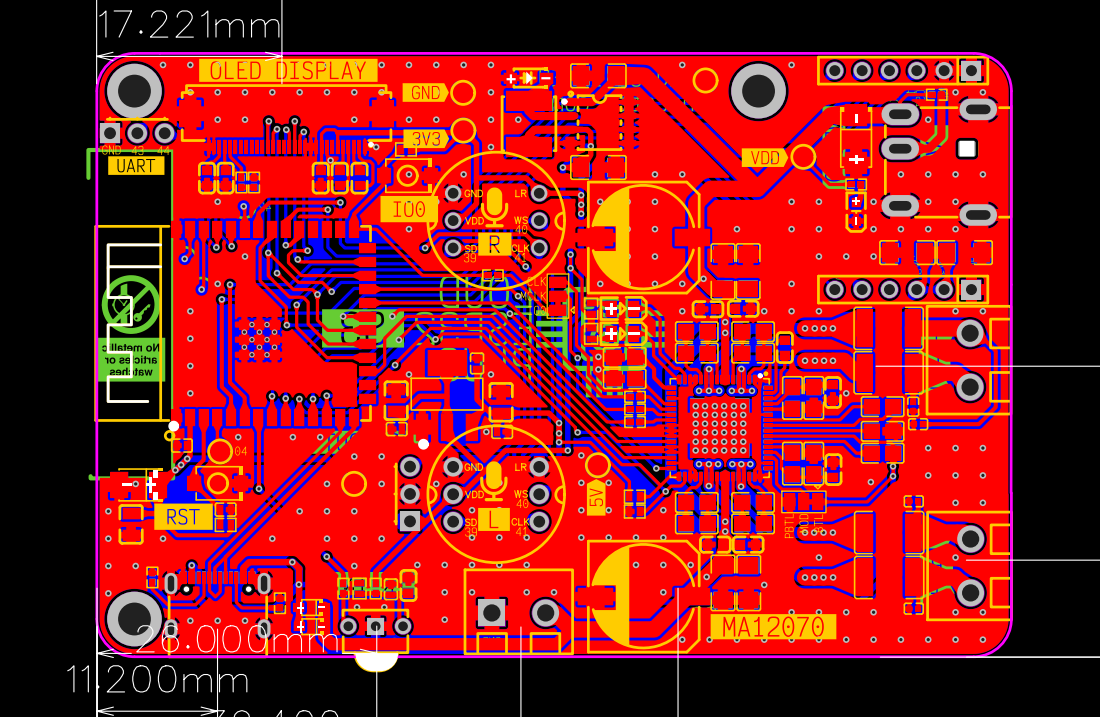
[picture p84: page 1]
