sonocotta/esp32-audio-dock/hardware/7-louder-esp32-plus/rev-a-s3/2601-louder-esp32s3-plus-a-pcb.pdf

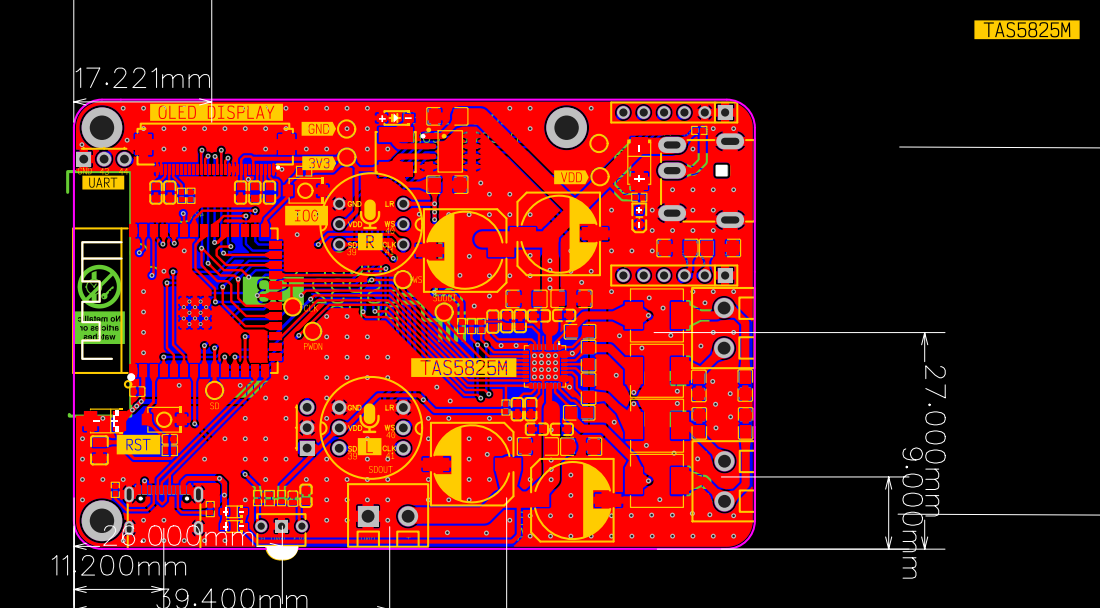
[picture p87: page 1]
