sonocotta/esp32-audio-dock/hardware/1-hifi-esp32/rev-f4/2511-hifi-esp32-f4-pcb.pdf

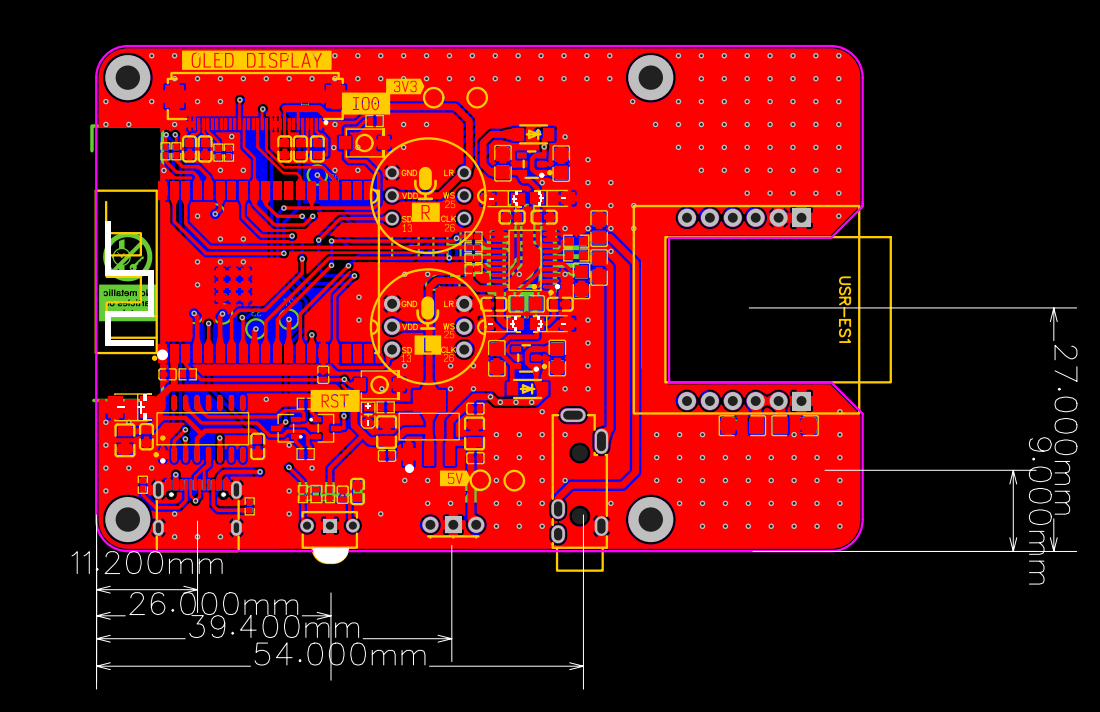
[picture p88: page 1]
