sonocotta/esp32-audio-dock/hardware/4-amped-esp32/rev-h1/2511-amped-esp32-h1-pcb.pdf

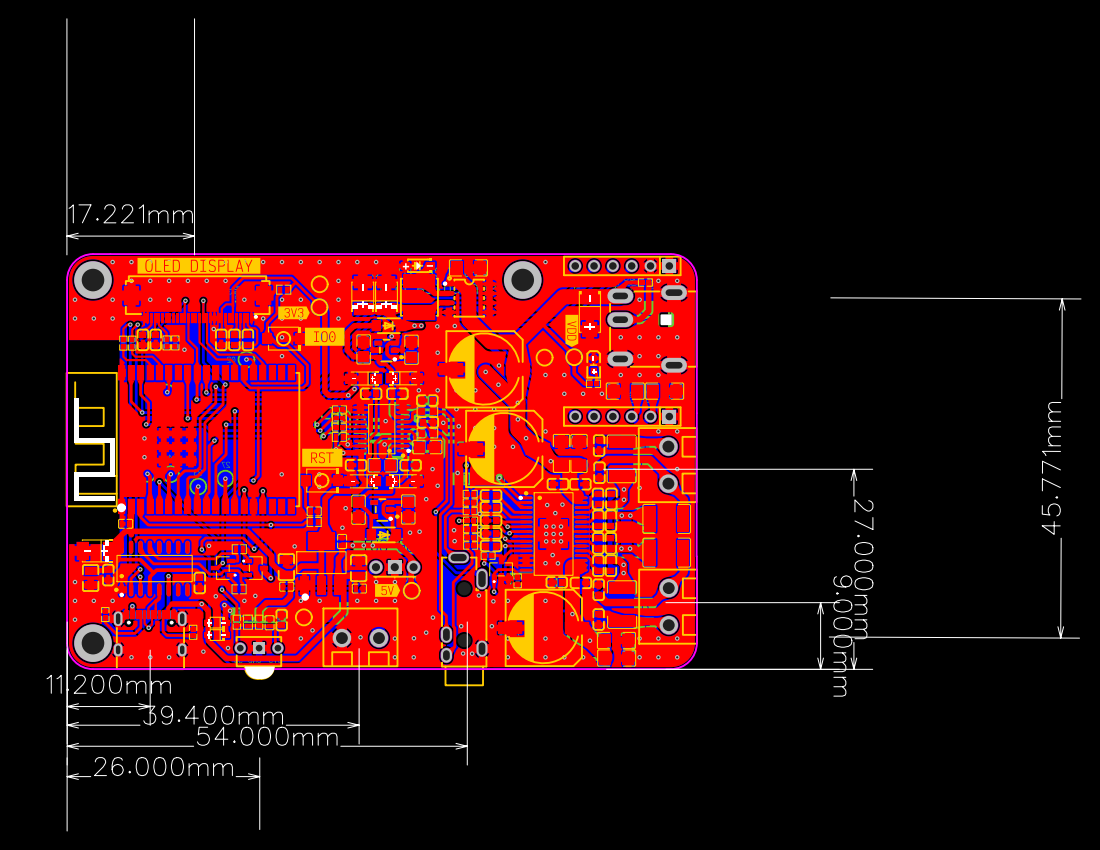
[picture p89: page 1]
