sonocotta/esp32-audio-dock/hardware/4-amped-esp32/rev-h1/2511-amped-esp32-h1-schematic.pdf

### U1GND ³⁹

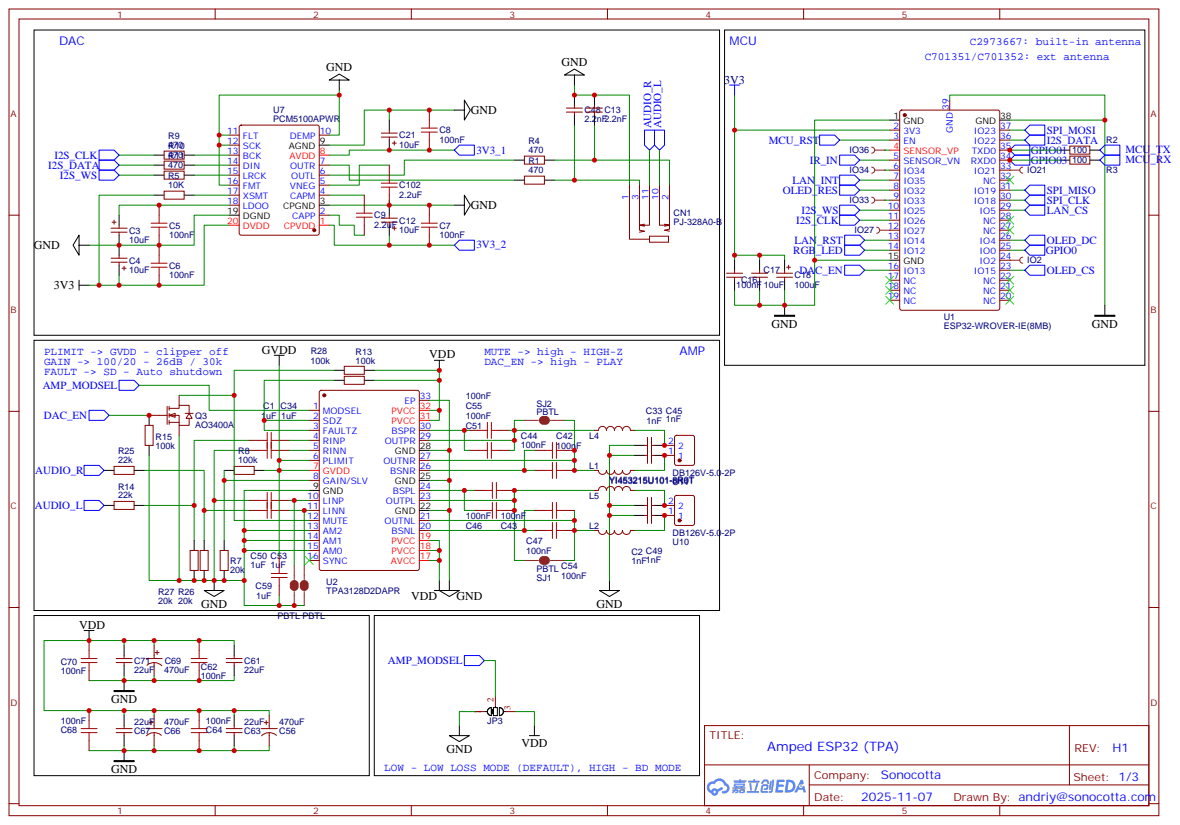
[picture p90: page 1]

PLIMIT -> GVDD - clipper off
FAULT -> SD - Auto shutdown
AMP_MODSEL

LOW - LOW LOSS MODE (DEFAULT), HIGH - BD MODE

Drawn By: andriy@sonocotta.com

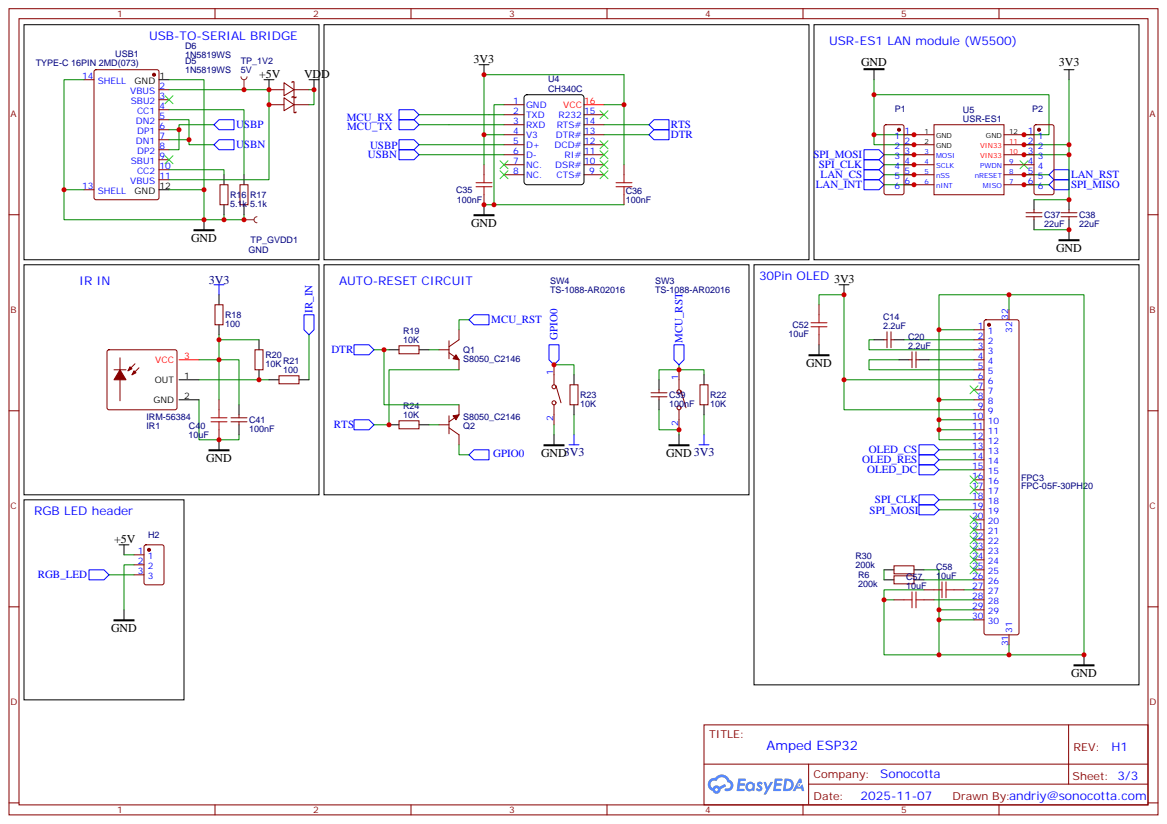
[picture p91: page 2]

USB-TO-SERIAL BRIDGE
USB1

Drawn By:andriy@sonocotta.com

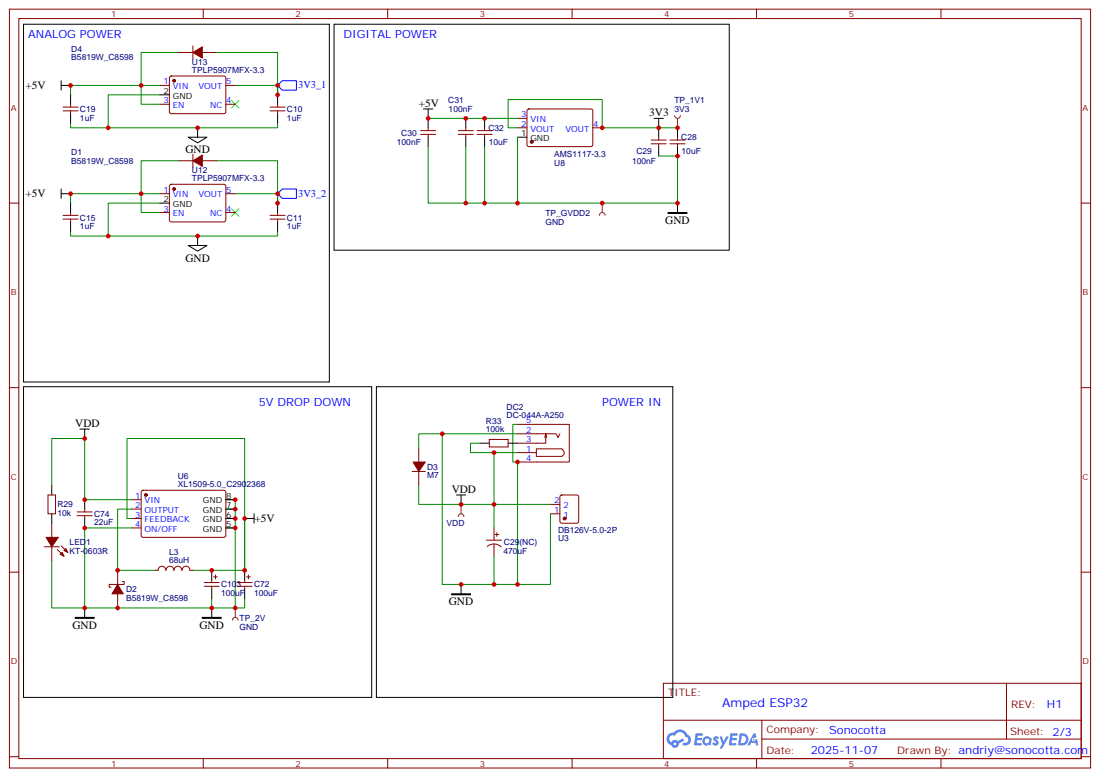
[picture p92: page 3]

Drawn By: andriy@sonocotta.com
