sonocotta/esp32-audio-dock/hardware/4-amped-esp32/rev-j/2511-amped-esp32-s3-j-pcb.pdf

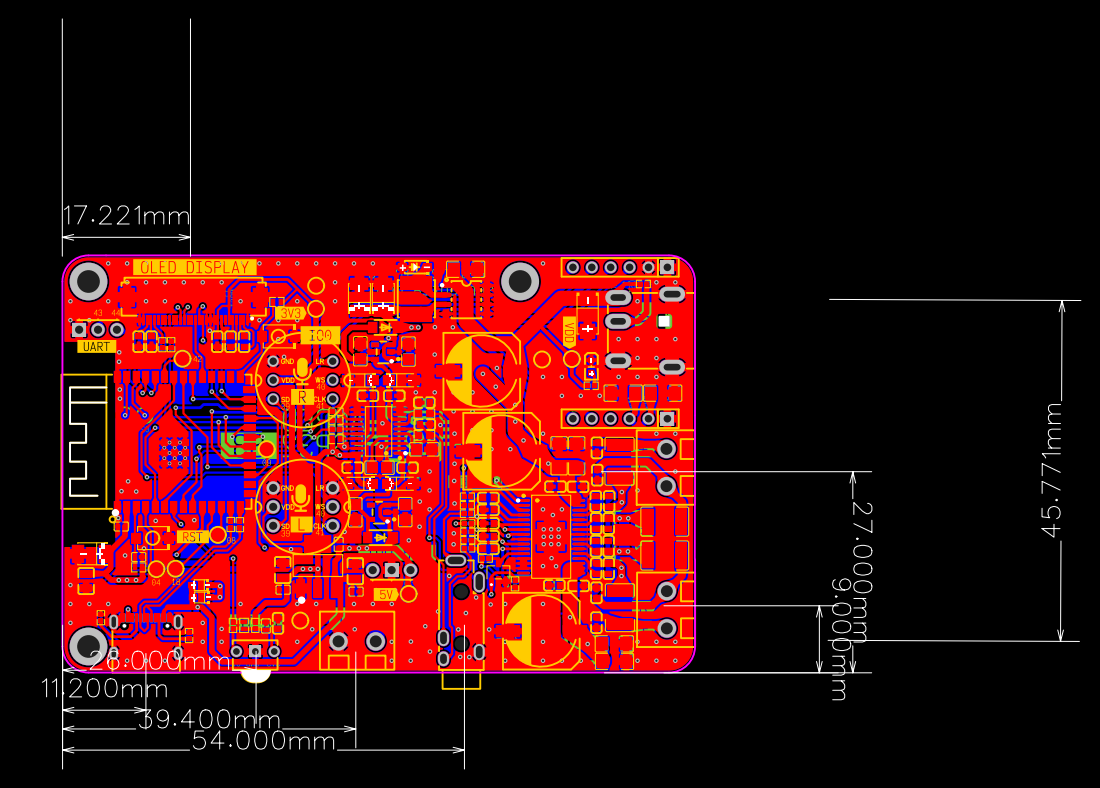
[picture p93: page 1]
