sonocotta/esp32-audio-dock/hardware/4-amped-esp32/rev-j/2511-amped-esp32-s3-j-schematic.pdf

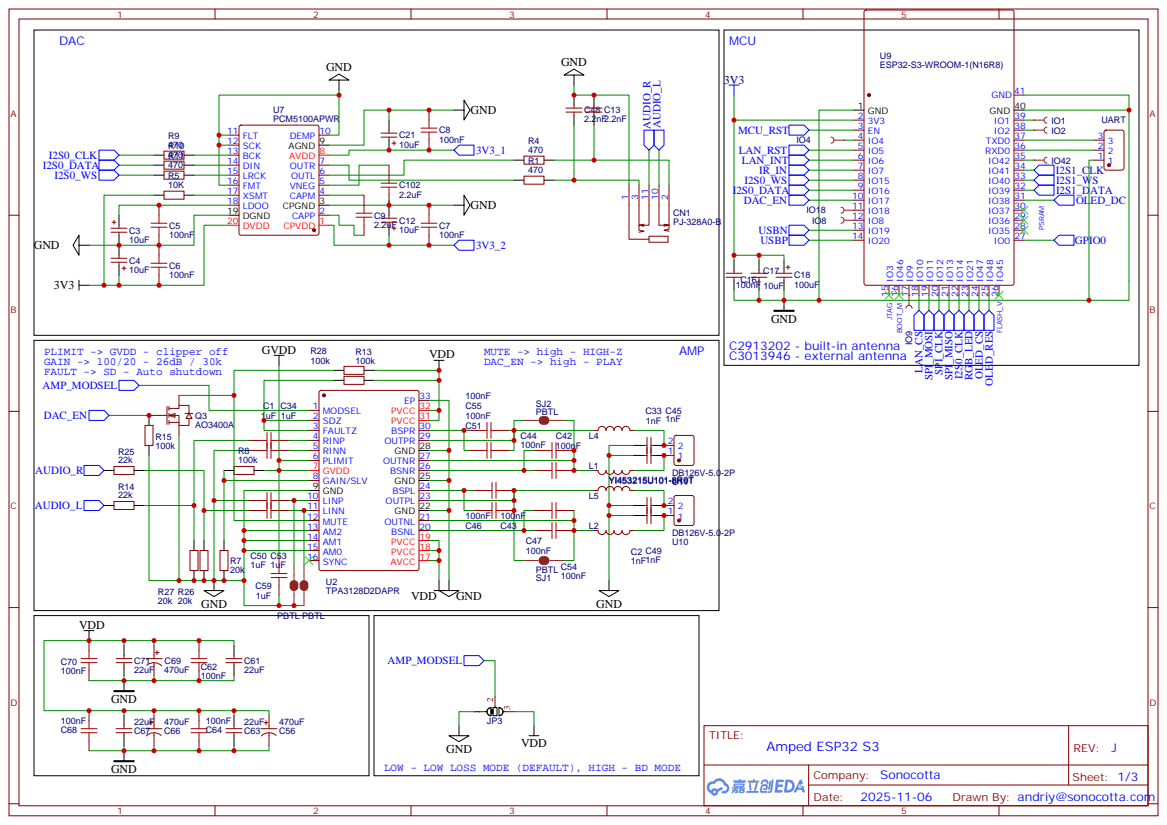
[picture p94: page 1]

PLIMIT -> GVDD - clipper off
FAULT -> SD - Auto shutdown
AMP_MODSEL

LOW - LOW LOSS MODE (DEFAULT), HIGH - BD MODE

Drawn By: andriy@sonocotta.com

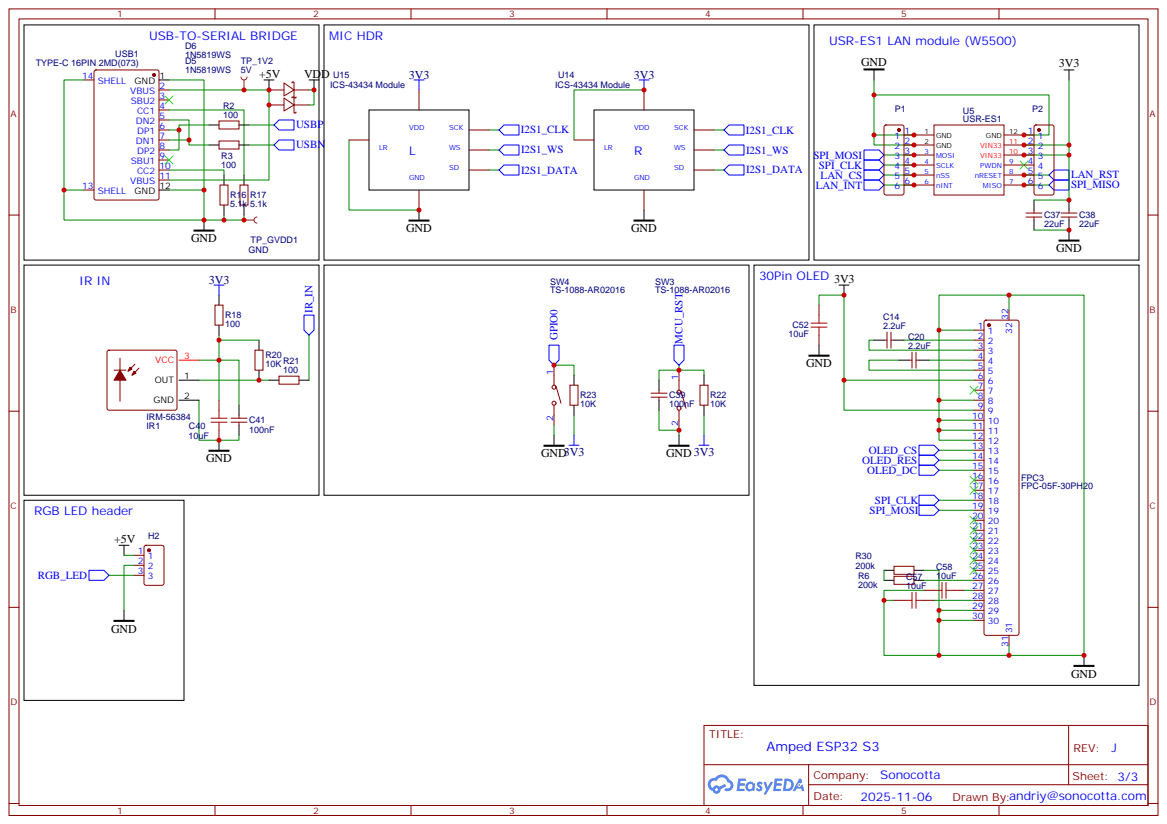
[picture p95: page 2]

USB-TO-SERIAL BRIDGE
USB1

Drawn By:andriy@sonocotta.com

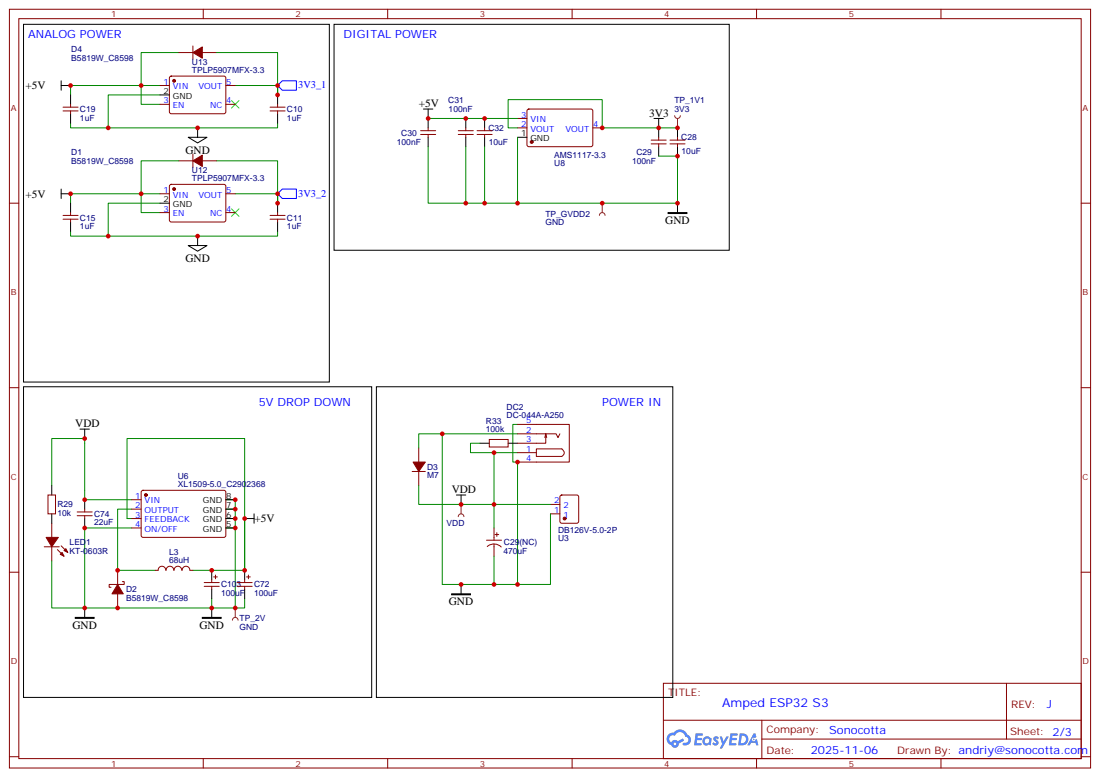
[picture p96: page 3]

Drawn By: andriy@sonocotta.com
