sonocotta/esp32-audio-dock/hardware/5-hifi-esp32-plus/rev-h1/2511-hifi-esp32s3-plus-h1-pcb.pdf

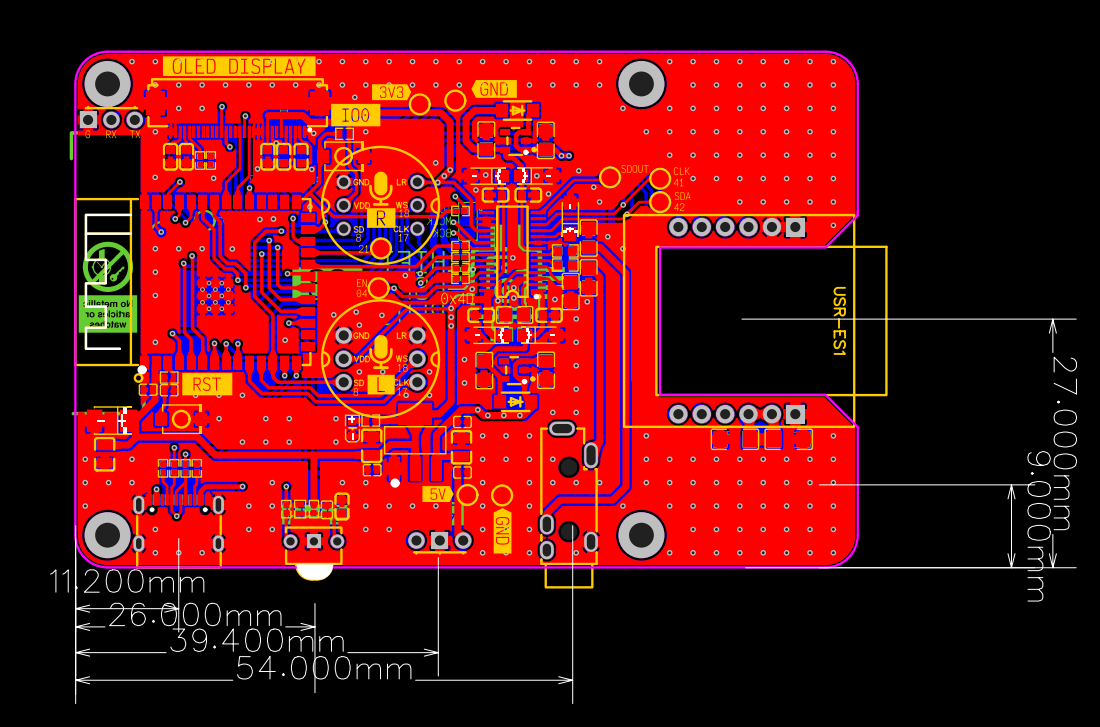
[picture p97: page 1]
