sonocotta/esp32-audio-dock/hardware/5-hifi-esp32-plus/rev-j/2511-hifi-esp32-plus-j-pcb.pdf

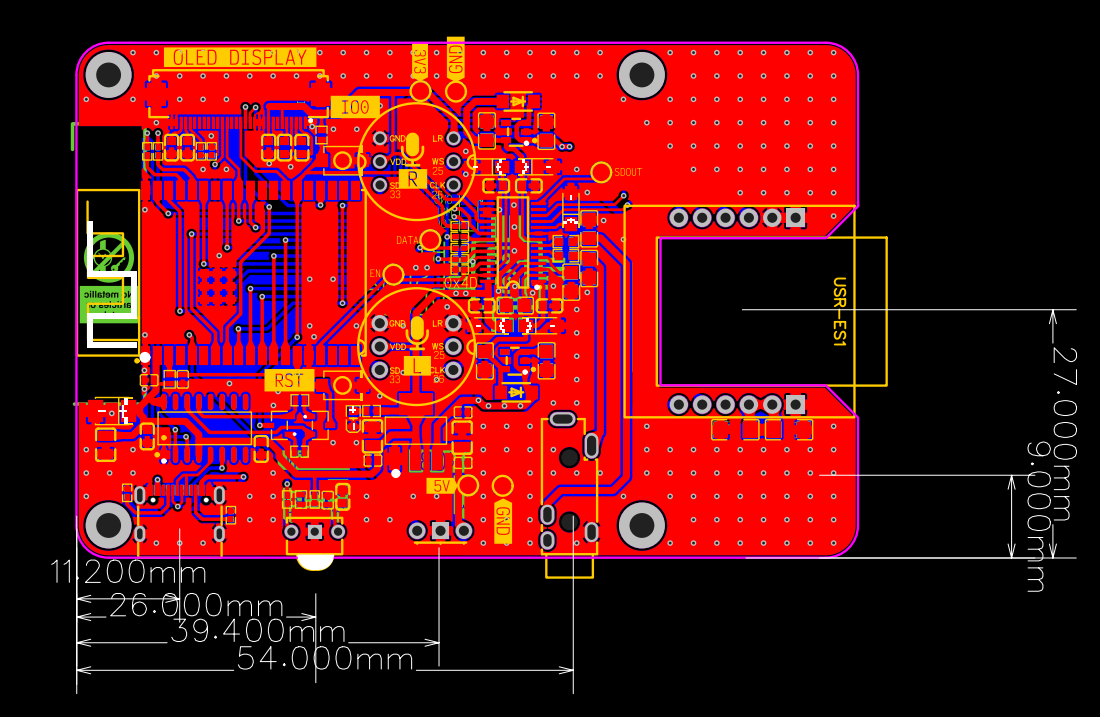
[picture p98: page 1]
