sonocotta/esp32-audio-dock/hardware/5-hifi-esp32-plus/rev-j1/2511-hifi-esp32-plus-j1-pcb.pdf

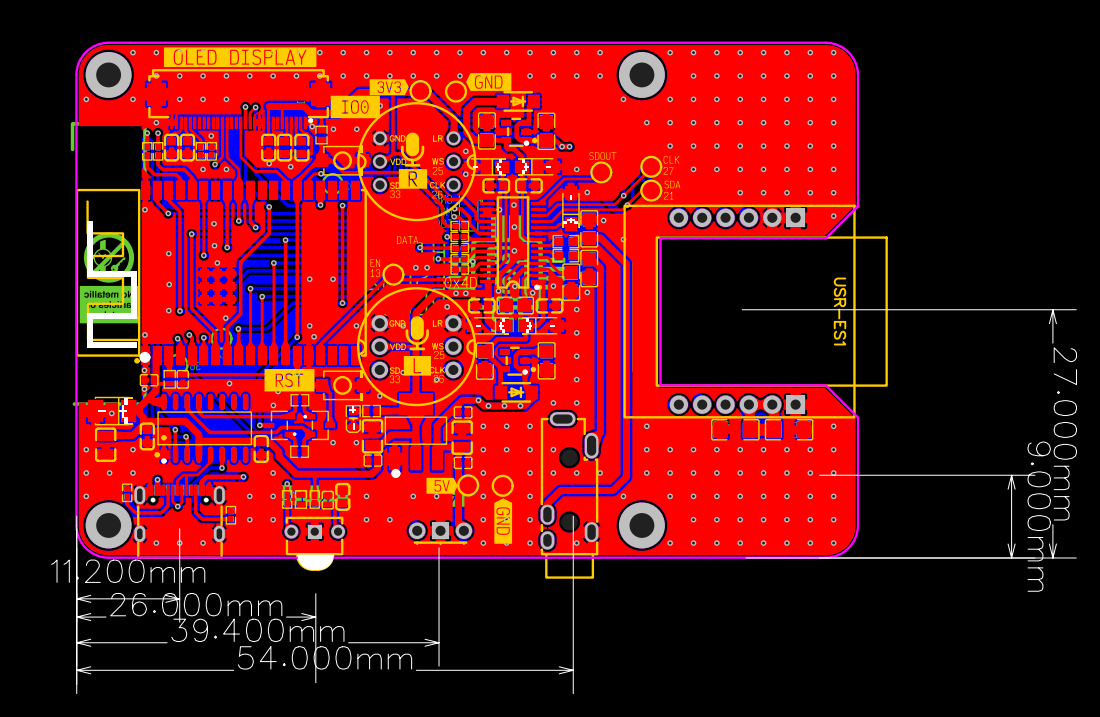
[picture p99: page 1]
