sonocotta/esp32-audio-dock/hardware/5-hifi-esp32-plus/rev-h/2510-hifi-esp32s3-plus-h-pcb.pdf

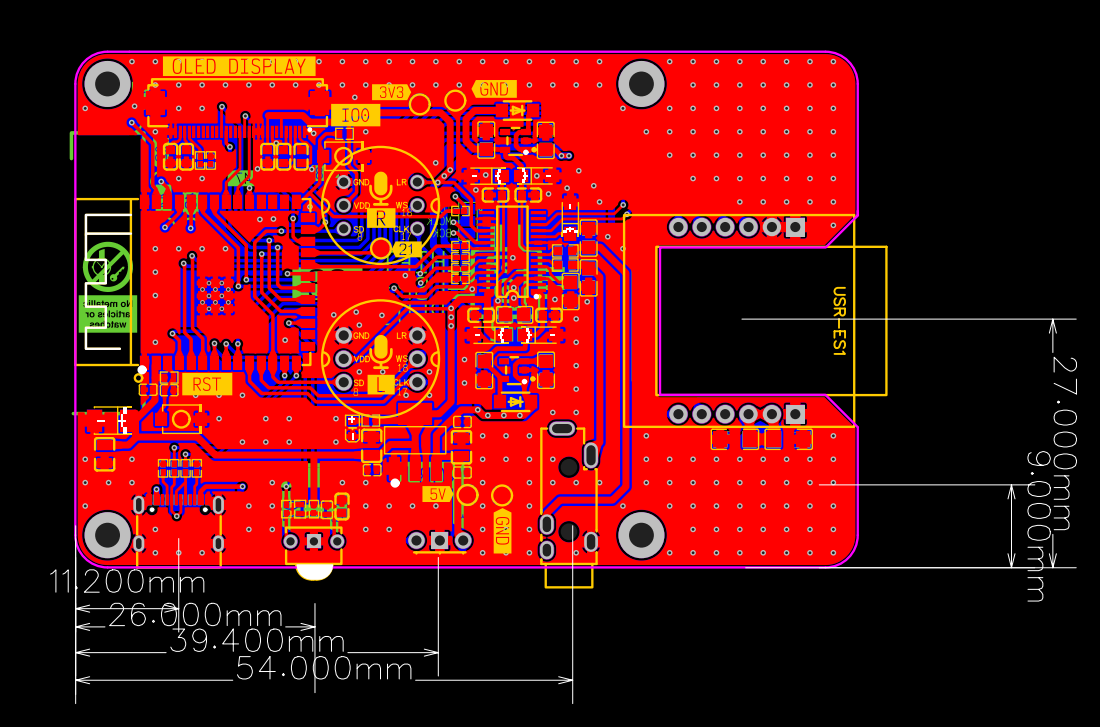
[picture p100: page 1]
