sonocotta/esp32-audio-dock/hardware/5-hifi-esp32-plus/rev-h/2510-hifi-esp32s3-plus-h-schematic.pdf

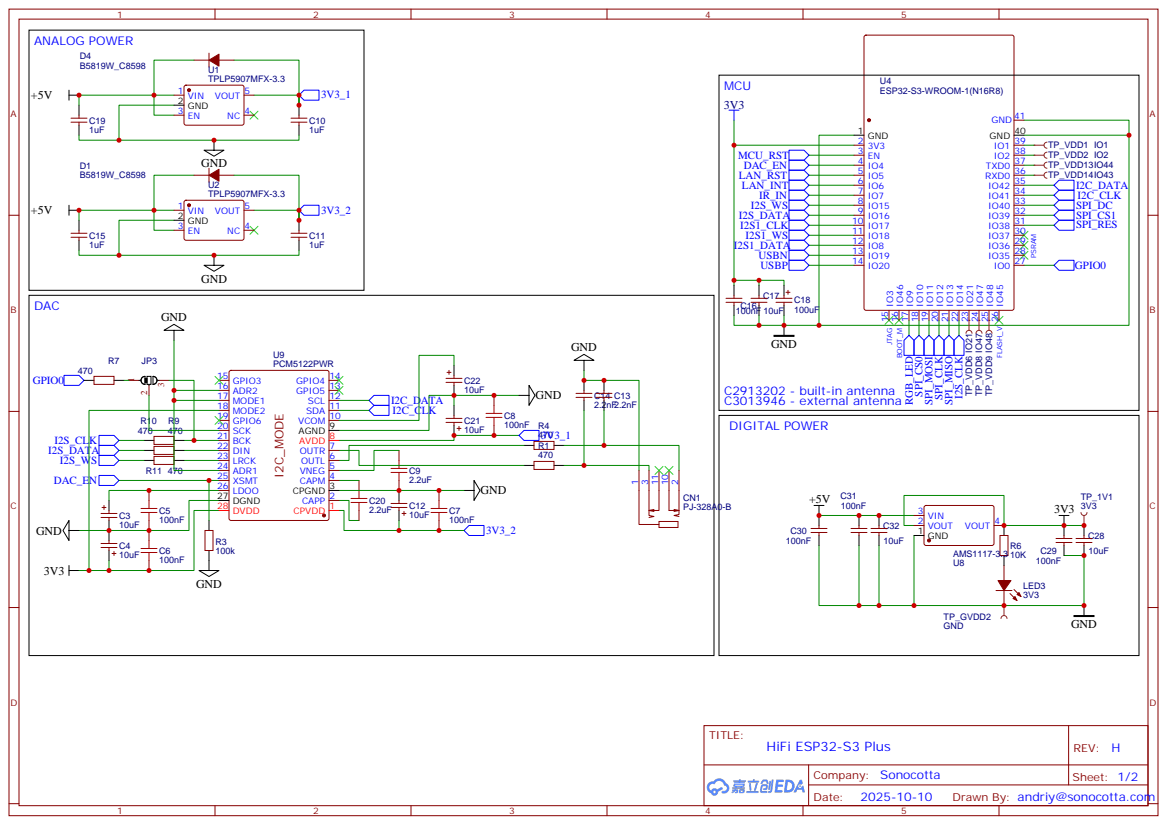
[picture p101: page 1]

Drawn By: andriy@sonocotta.com

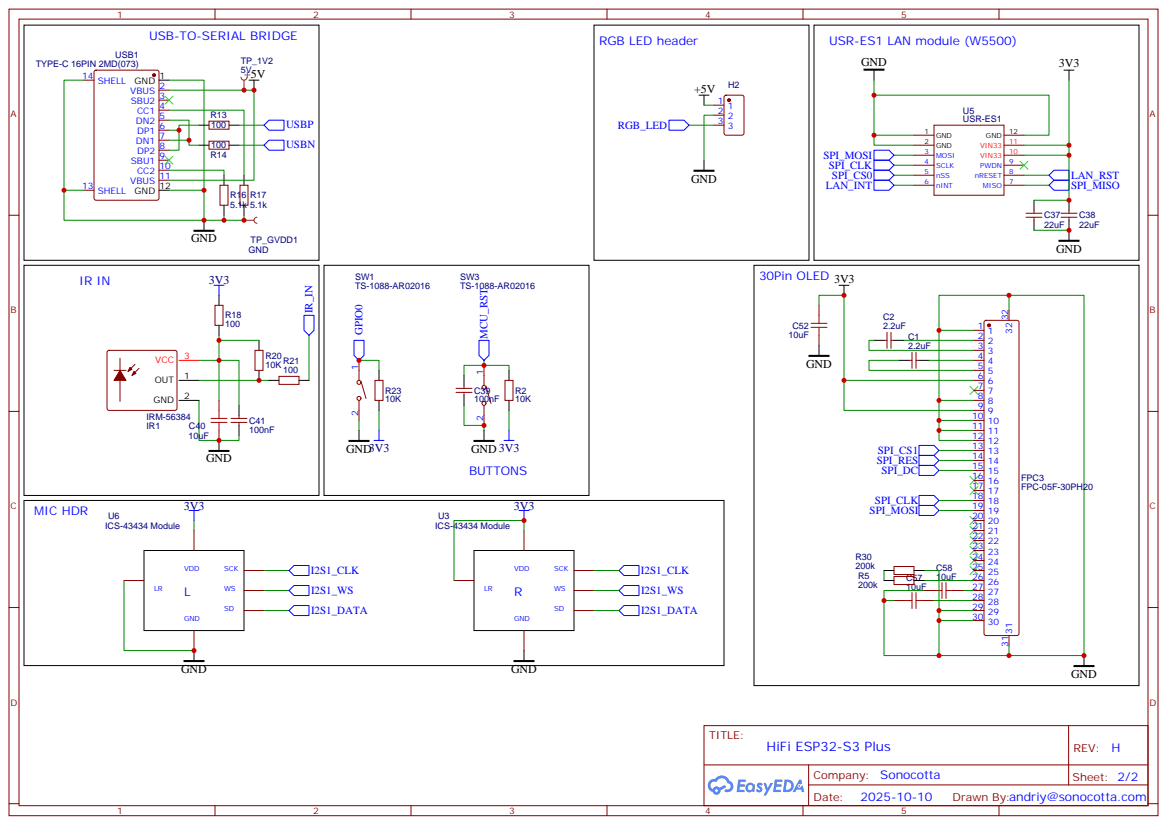
[picture p102: page 2]

Drawn By:andriy@sonocotta.com
