sonocotta/esp32-audio-dock/hardware/4-amped-esp32/rev-h/2510-amped-esp32-h-pcb.pdf

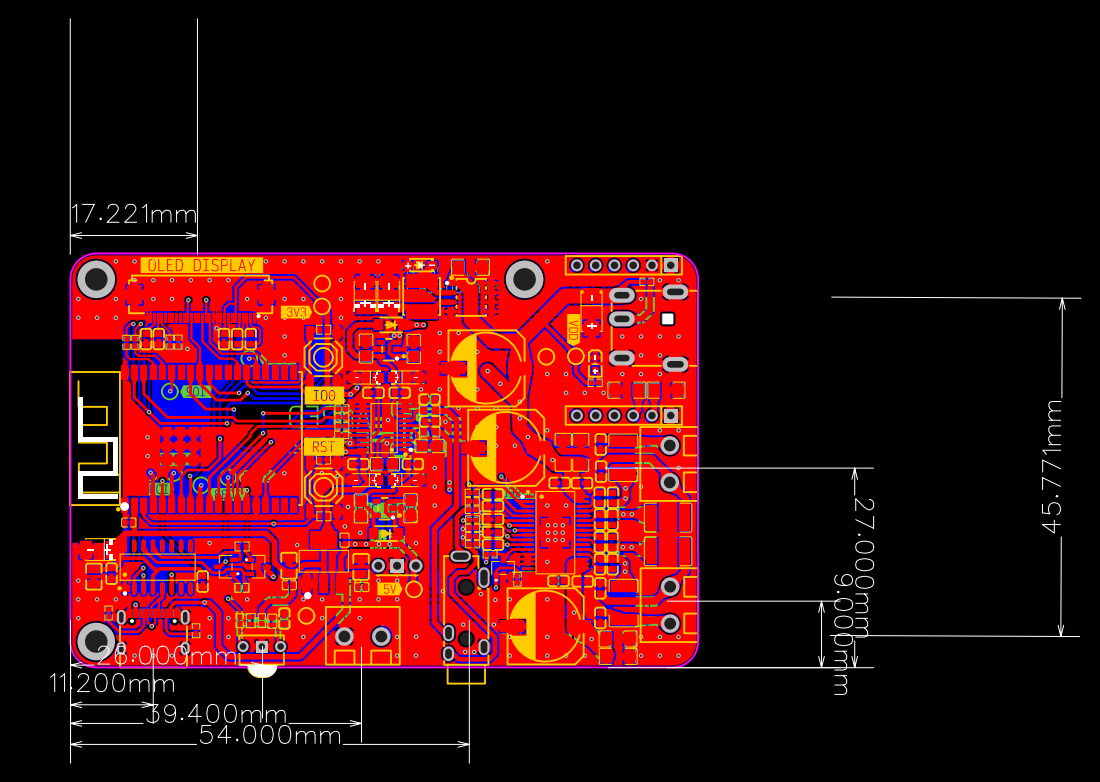
[picture p103: page 1]
