sonocotta/esp32-audio-dock/hardware/4-amped-esp32/rev-h/2510-amped-esp32-h-schematic.pdf

### U1GND ³⁹

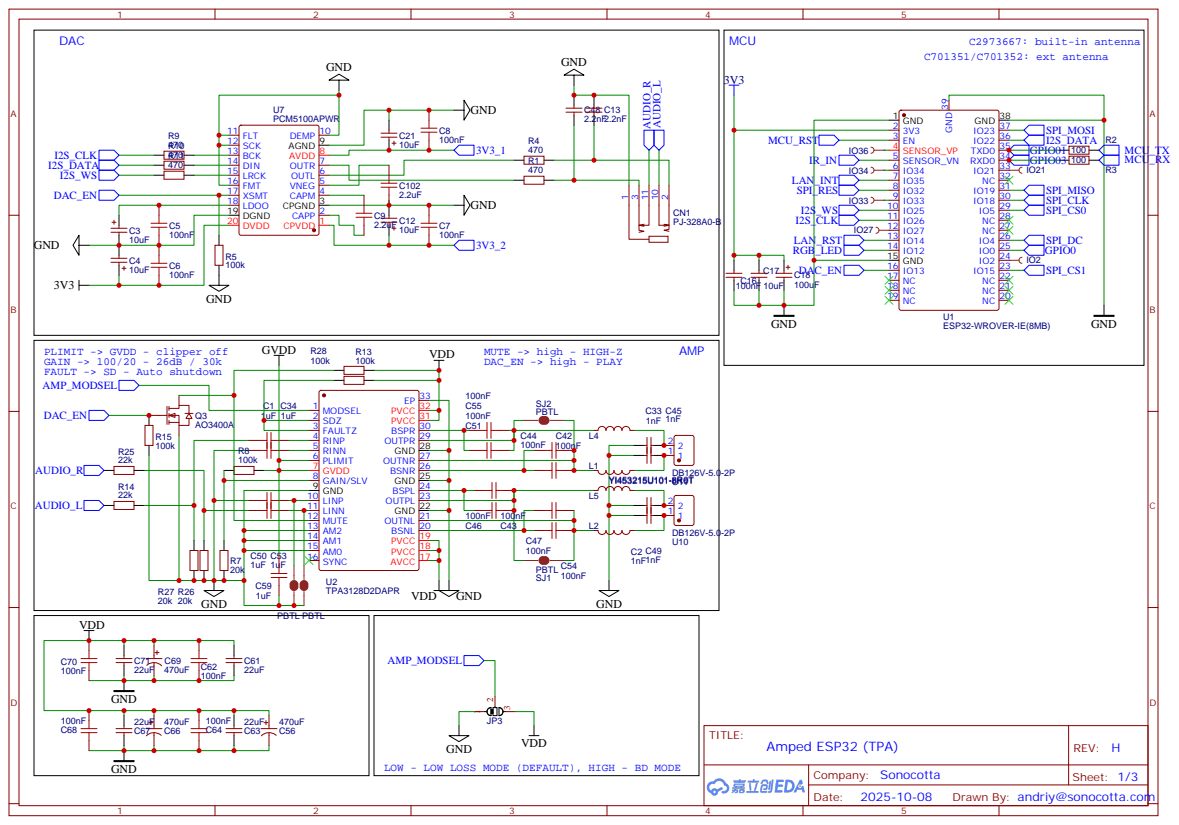
[picture p104: page 1]

PLIMIT -> GVDD - clipper off
FAULT -> SD - Auto shutdown
AMP_MODSEL

LOW - LOW LOSS MODE (DEFAULT), HIGH - BD MODE

Drawn By: andriy@sonocotta.com

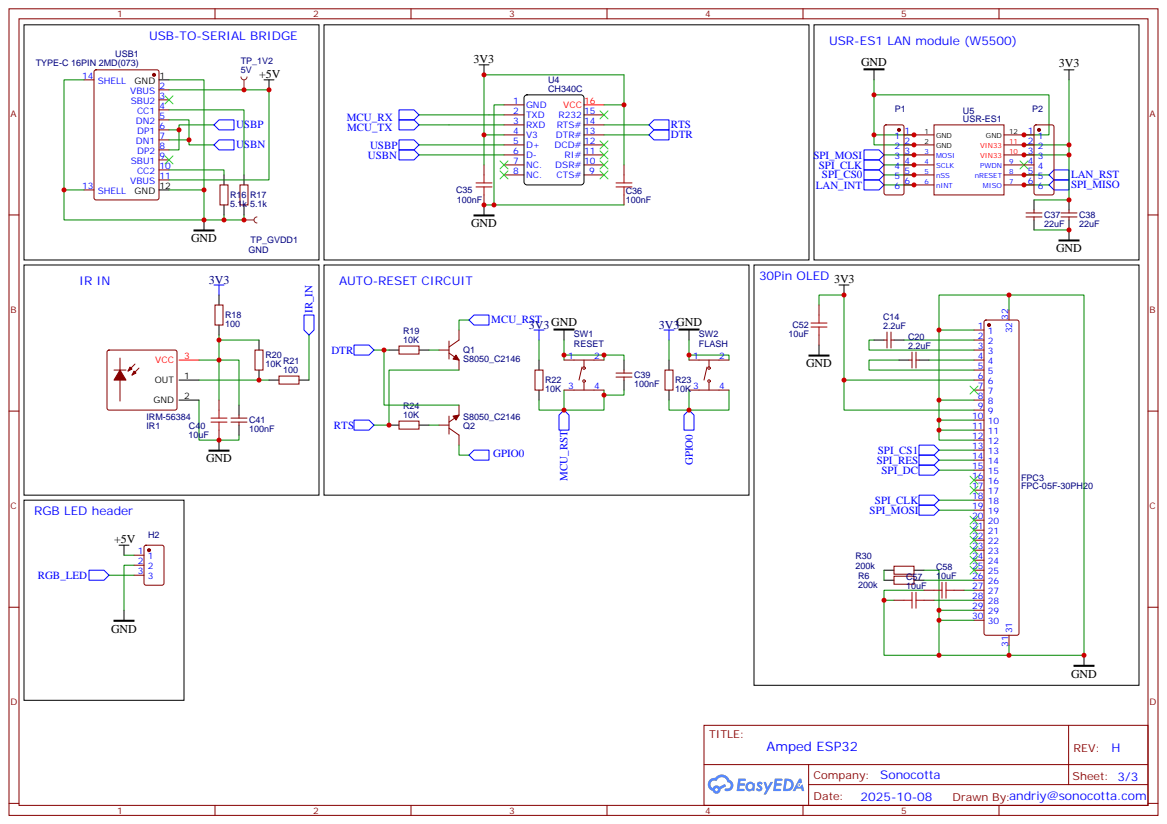
[picture p105: page 2]

USB-TO-SERIAL BRIDGE
USB1

Drawn By:andriy@sonocotta.com

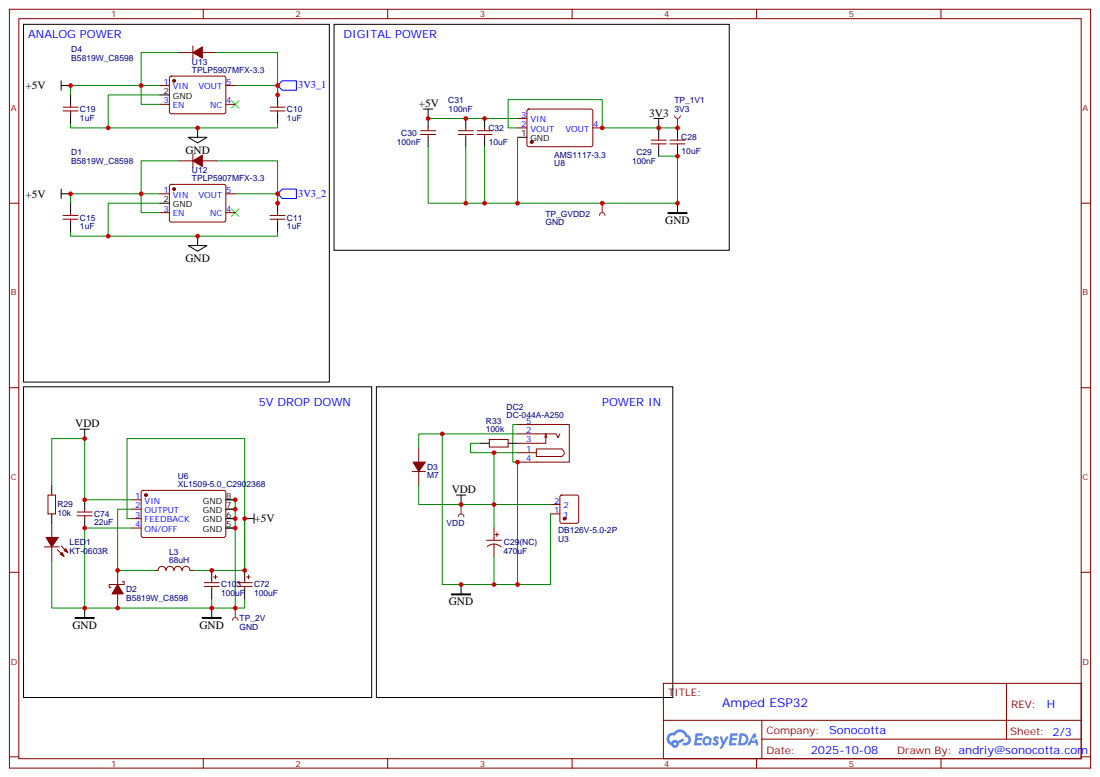
[picture p106: page 3]

Drawn By: andriy@sonocotta.com
