sonocotta/esp32-audio-dock/hardware/1-hifi-esp32/rev-f3/2509-hifi-esp32-f3-pcb.pdf

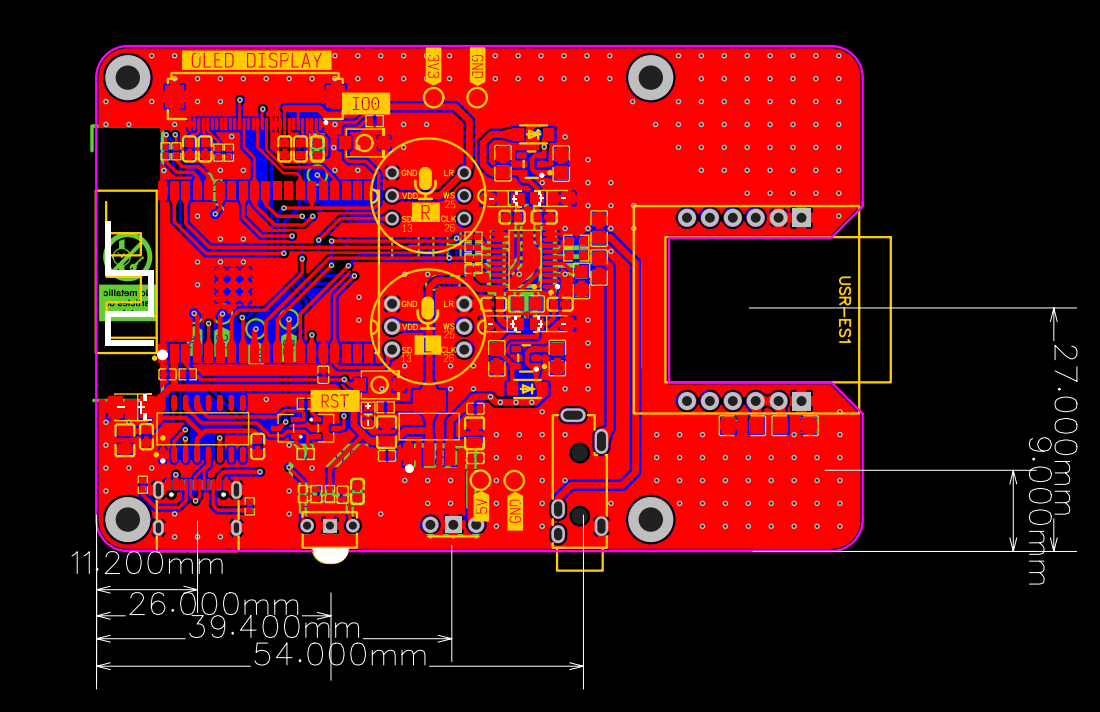
[picture p107: page 1]
