sonocotta/esp32-audio-dock/hardware/1-hifi-esp32/rev-g2/2509-hifi-esp32s3-g2-pcb.pdf

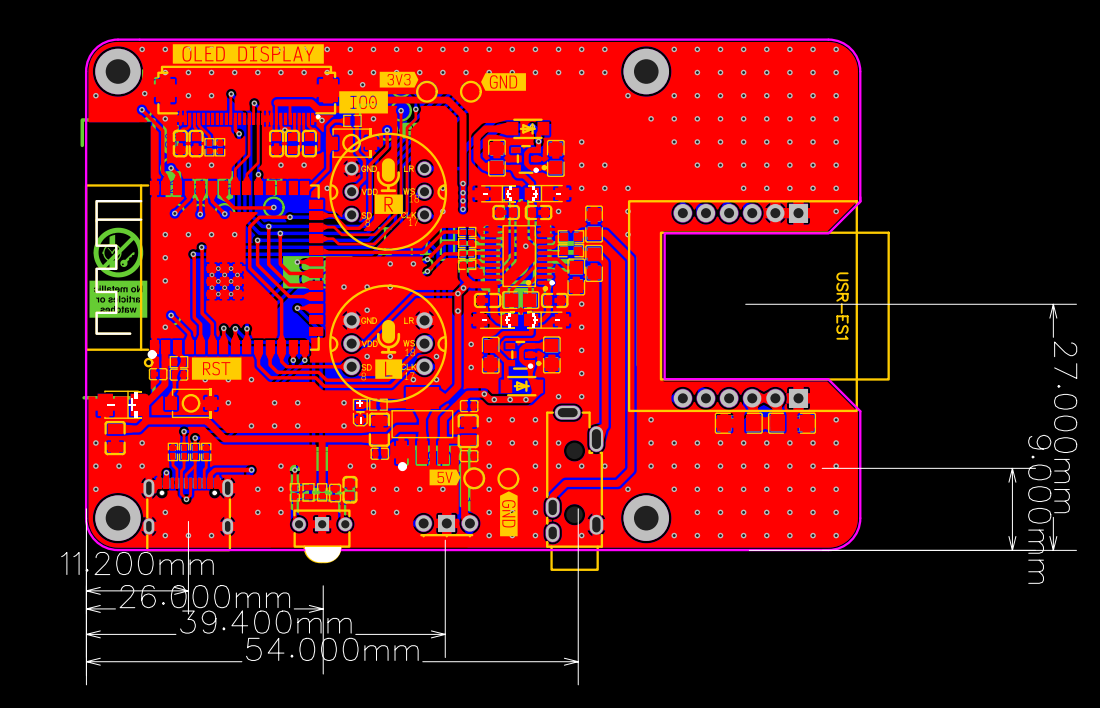
[picture p108: page 1]
