sonocotta/esp32-audio-dock/hardware/1-hifi-esp32/rev-g2/2509-hifi-esp32s3-g2-schematic.pdf

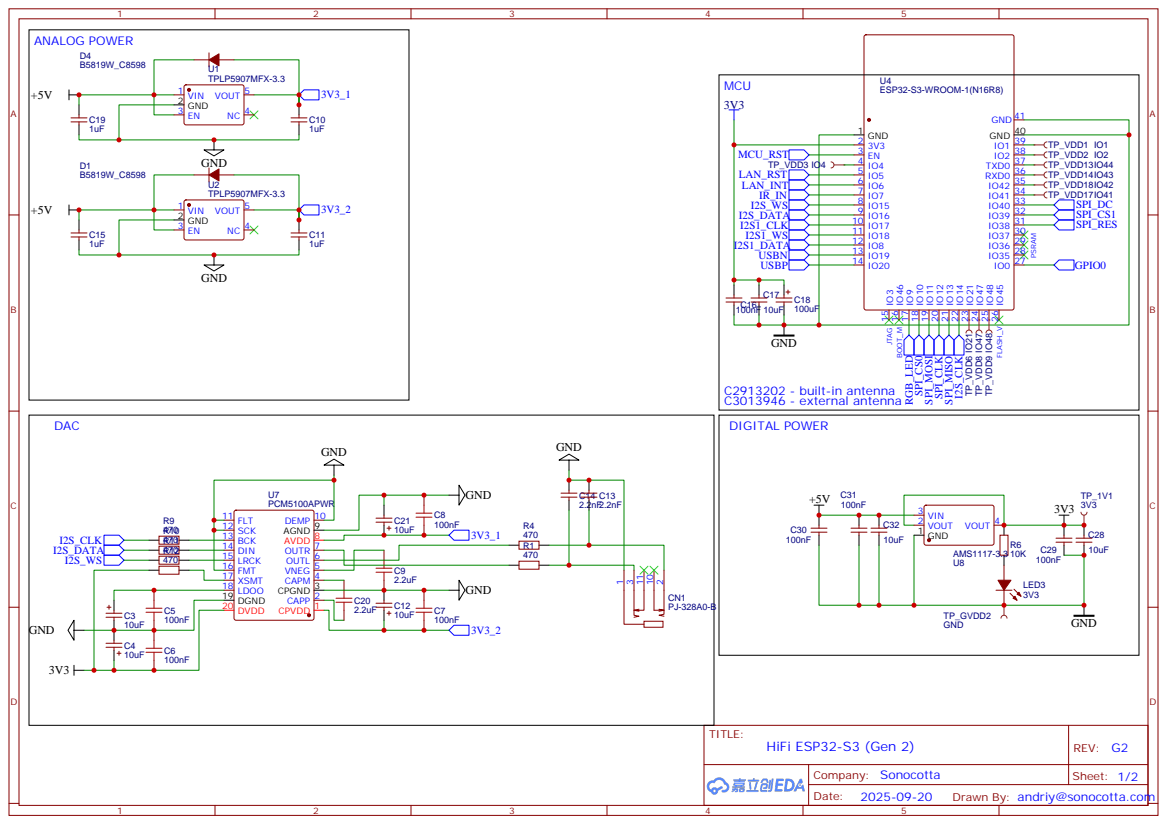
[picture p109: page 1]

Drawn By: andriy@sonocotta.com

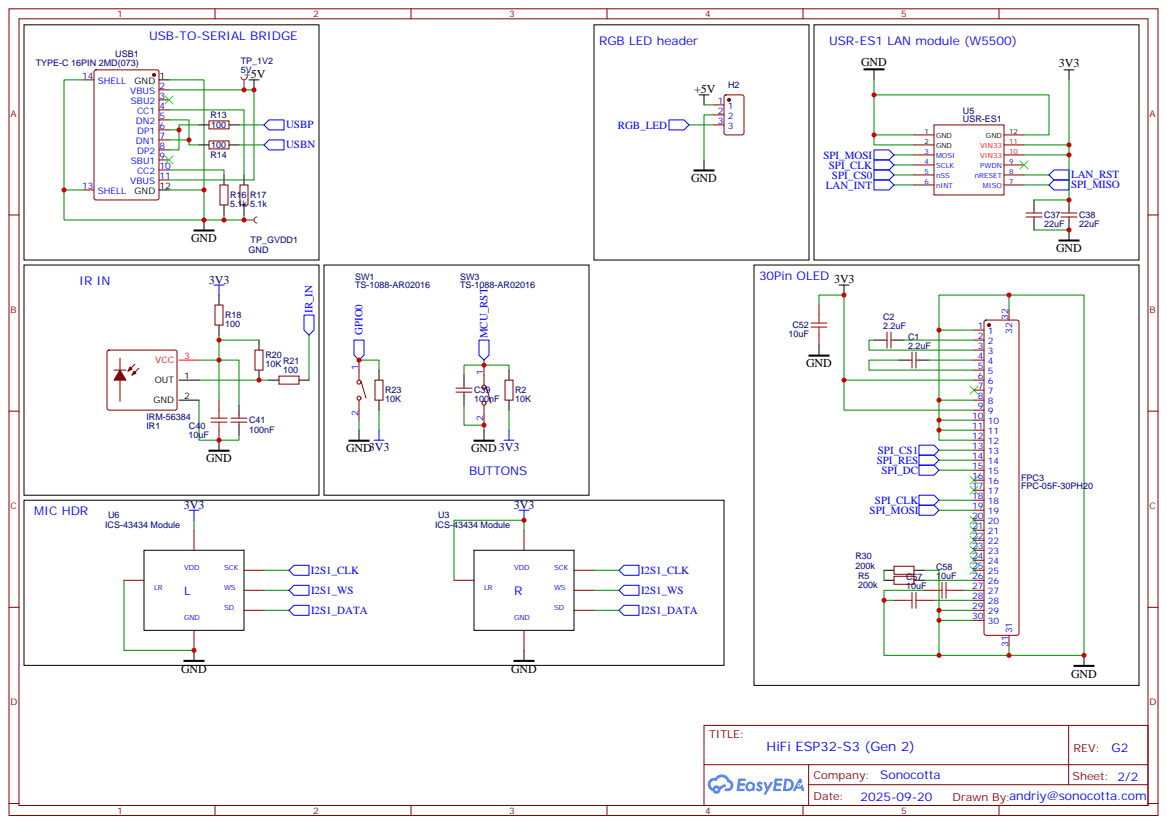
[picture p110: page 2]

Drawn By:andriy@sonocotta.com
