sonocotta/esp32-audio-dock/hardware/1-hifi-esp32/rev-g1/2501-hifi-esp-g1-pcb.pdf

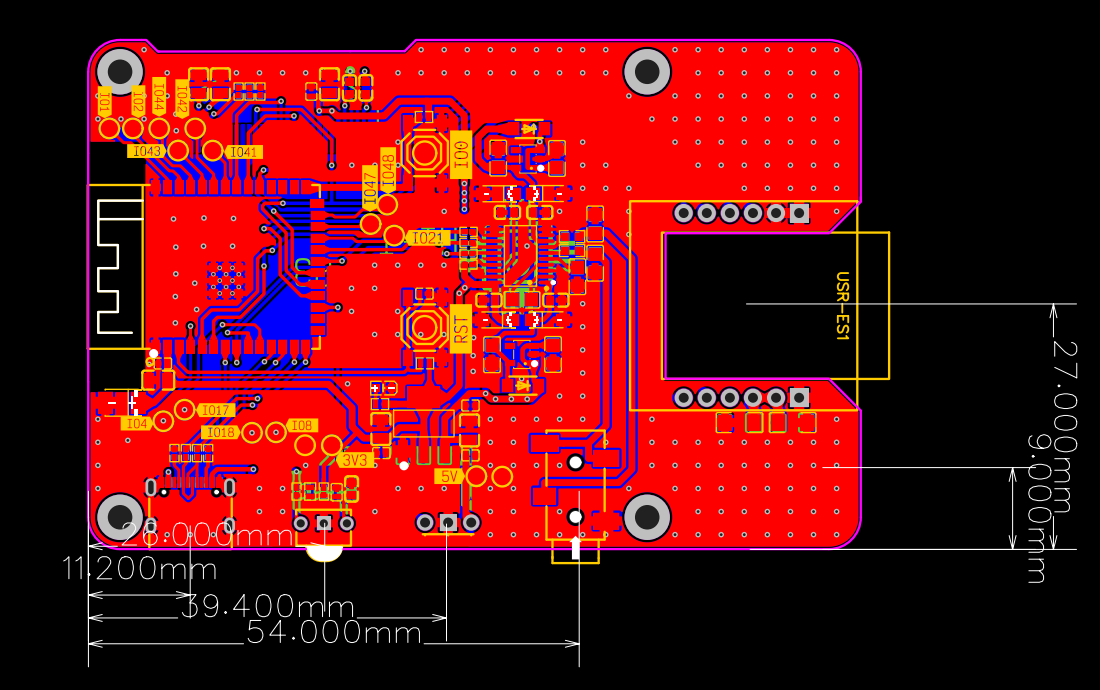
[picture p111: page 1]
