sonocotta/esp32-audio-dock/hardware/1-hifi-esp32/rev-g1/2501-hifi-esp32s3-g1-schematic.pdf

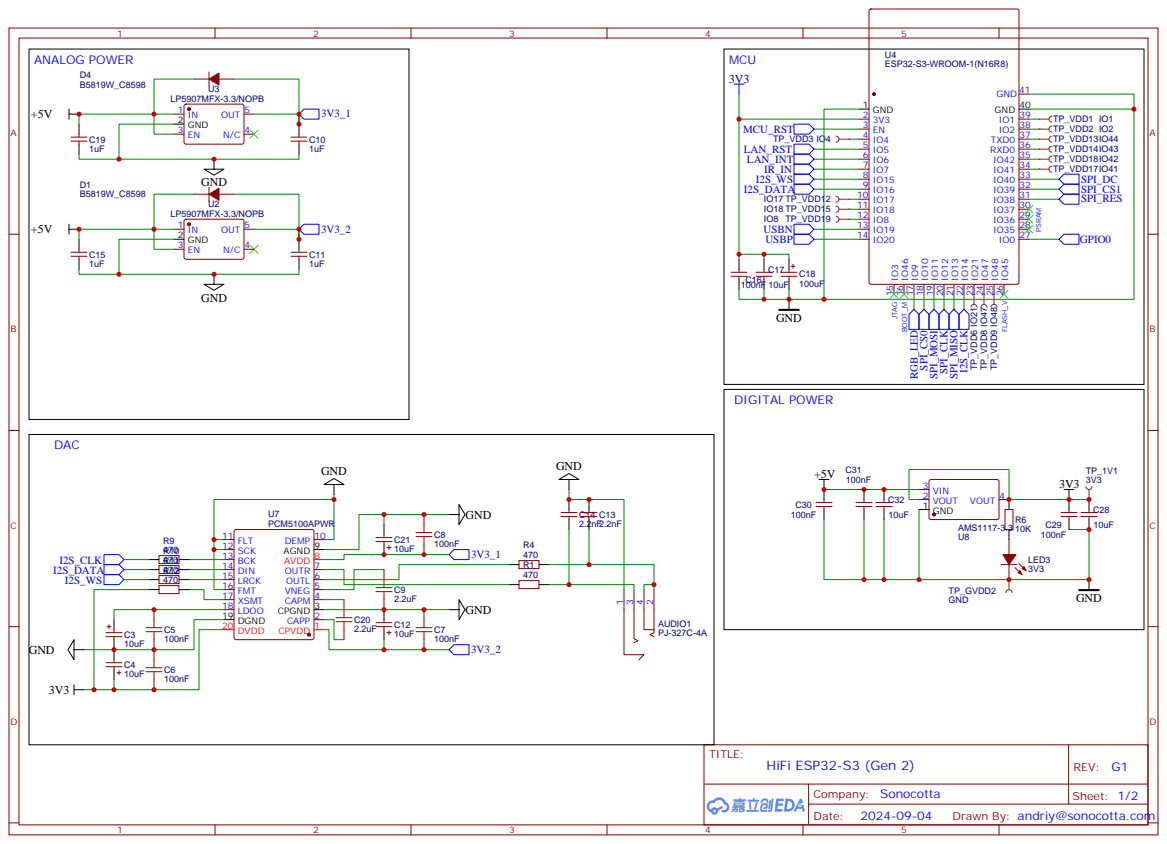
[picture p112: page 1]

Drawn By: andriy@sonocotta.com

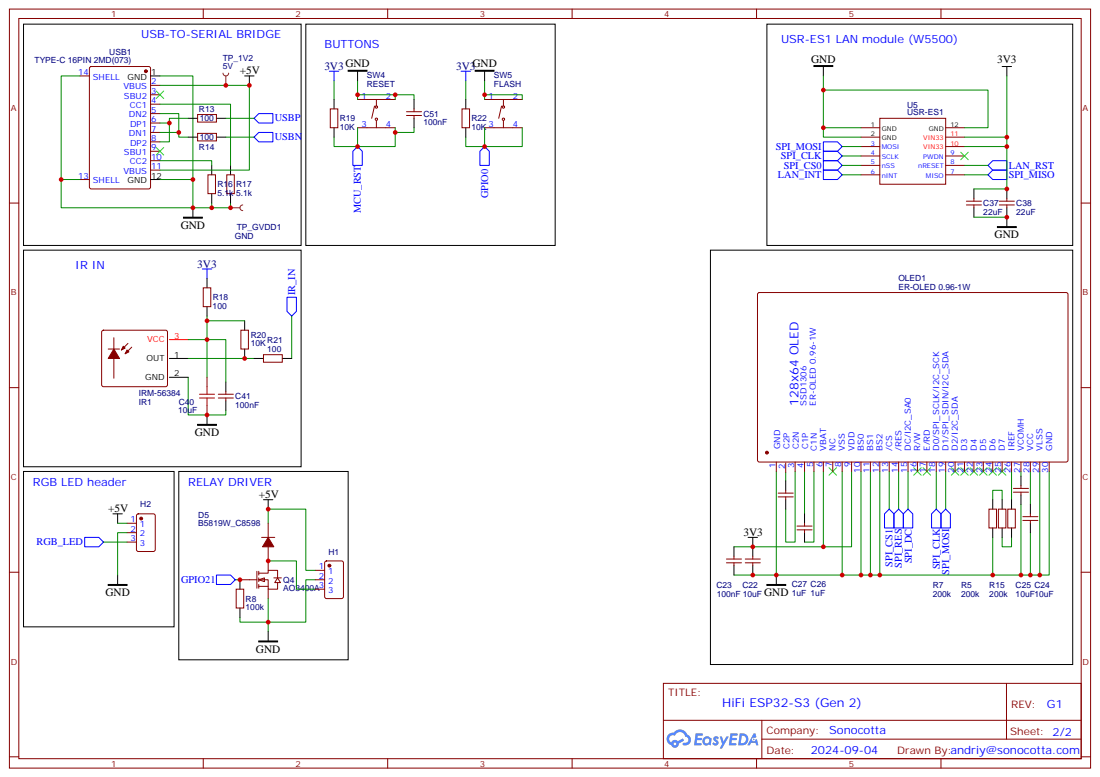
[picture p113: page 2]

Drawn By:andriy@sonocotta.com
