sonocotta/esp32-audio-dock/hardware/3-louder-esp32/rev-h3/2410-louder-esp32-h3-schematic.pdf

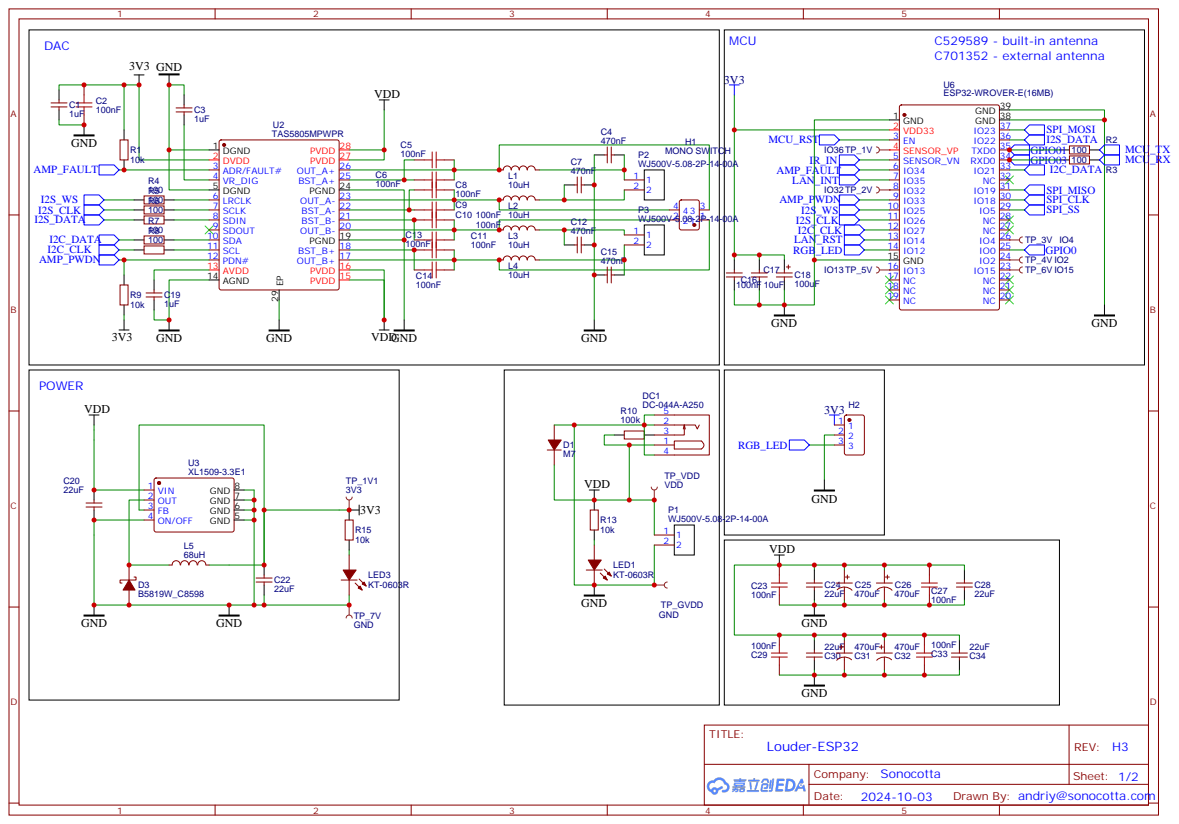
[picture p114: page 1]

Drawn By: andriy@sonocotta.com

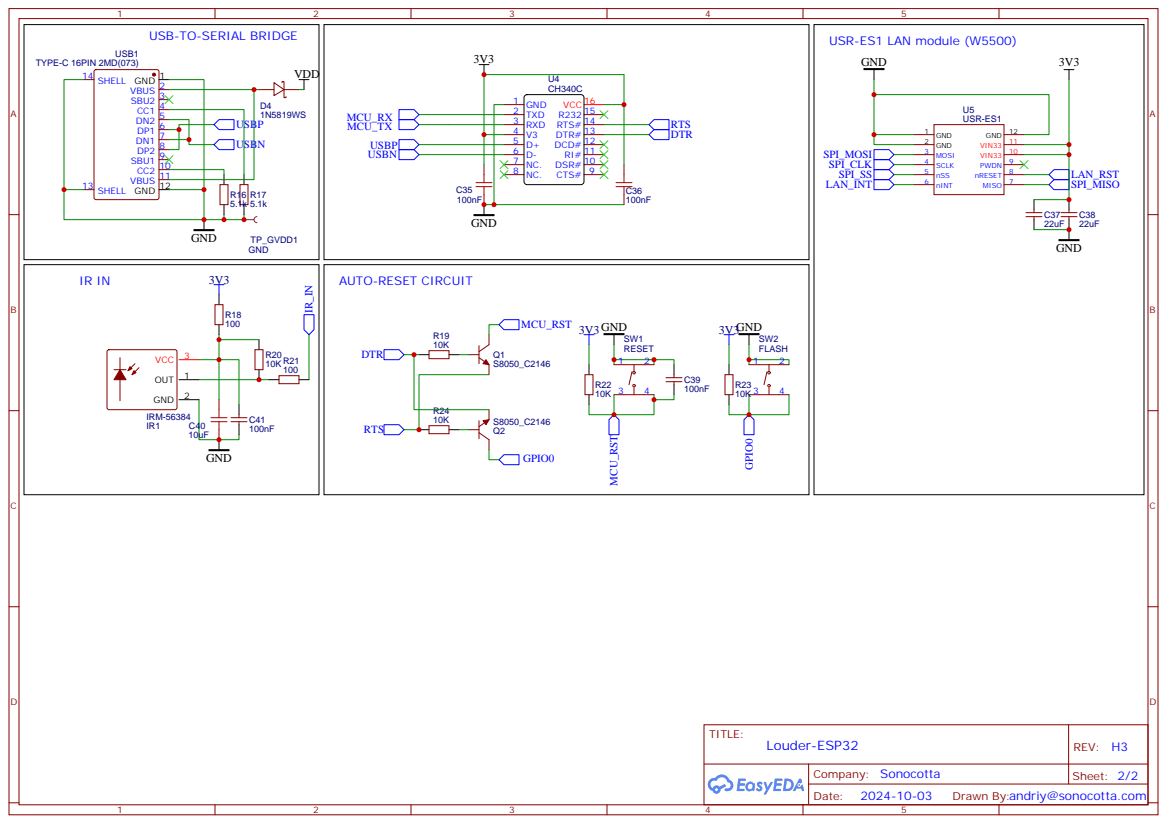
[picture p115: page 2]

Drawn By:andriy@sonocotta.com
