sonocotta/esp32-audio-dock/hardware/3-louder-esp32/rev-h3/2503-louder-esp32-h3-pcb.pdf

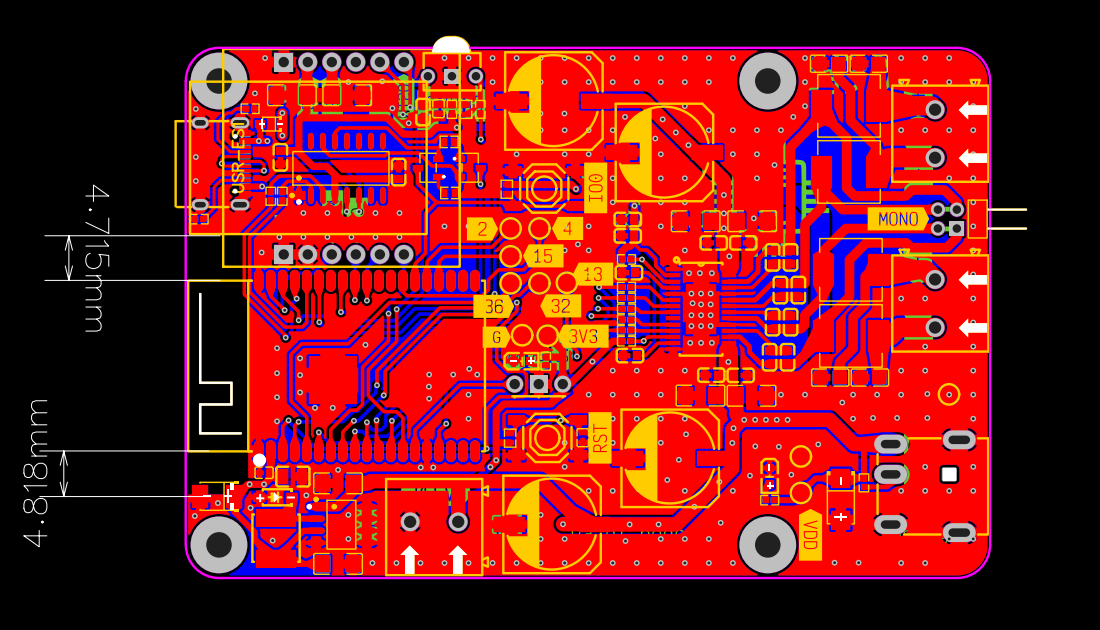
[picture p116: page 1]
