sonocotta/esp32-audio-dock/hardware/3-louder-esp32/rev-h4/2506-louder-esp32-h4-pcb.pdf

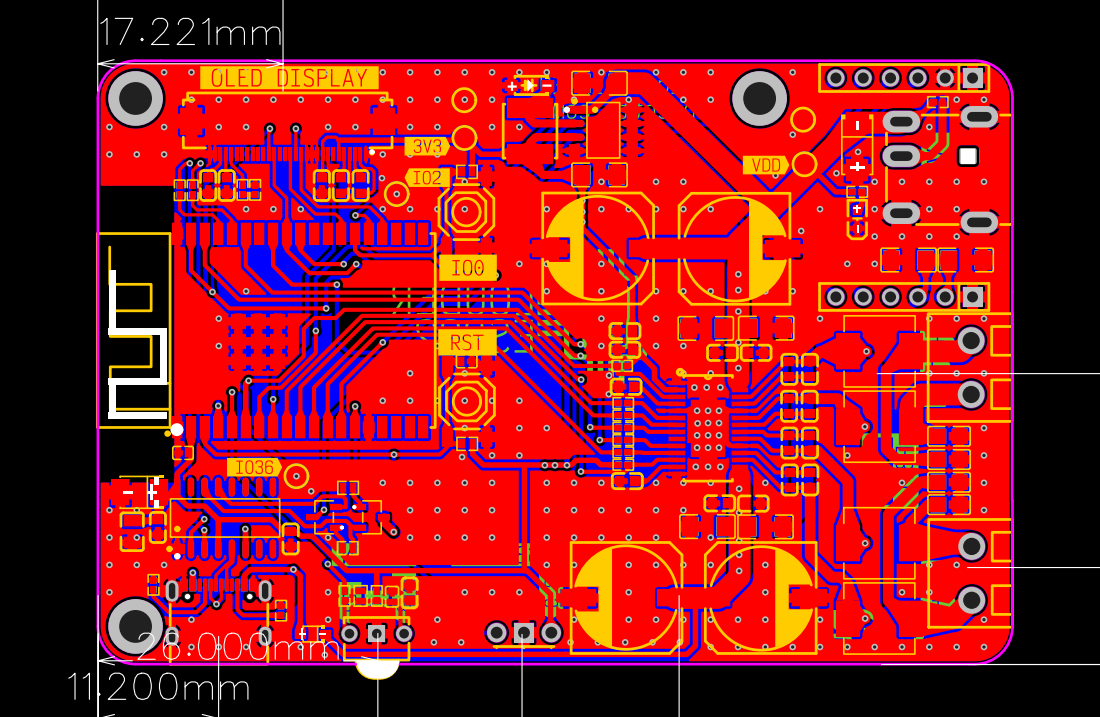
[picture p117: page 1]
