sonocotta/esp32-audio-dock/hardware/3-louder-esp32/rev-h4/2506-louder-esp32-h4-schematic.pdf

## U1GND ³⁹

## MCU

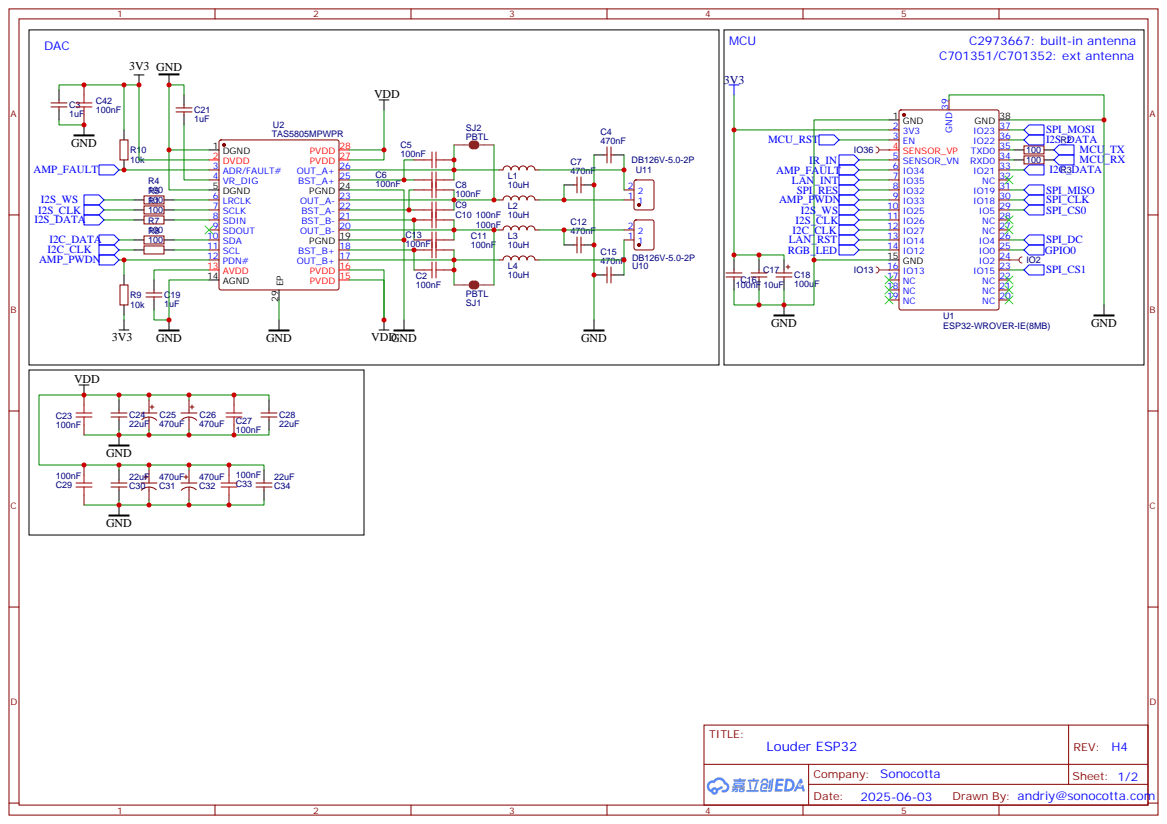
[picture p118: page 1]

Drawn By: andriy@sonocotta.com

## USB-TO-SERIAL BRIDGE USR-ES1 LAN module (W5500)

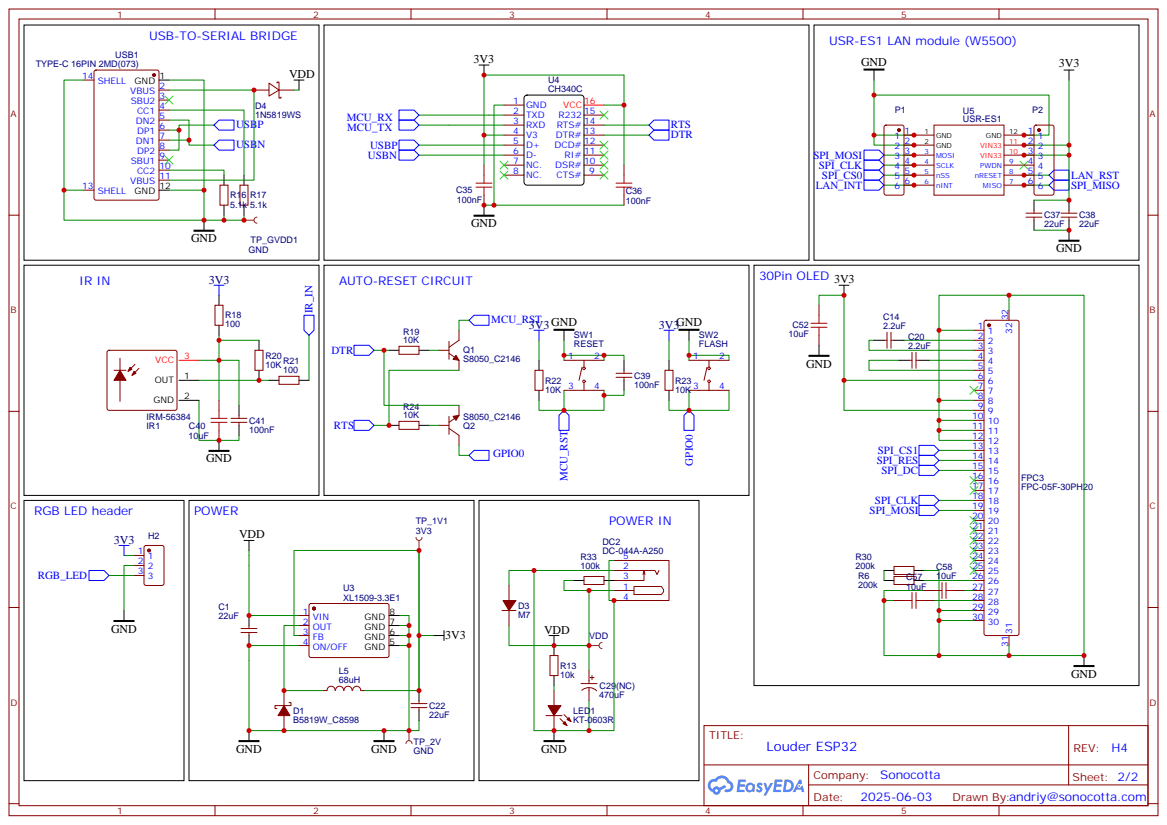
[picture p119: page 2]

Drawn By:andriy@sonocotta.com
