sonocotta/esp32-audio-dock/hardware/3-louder-esp32/rev-h5/2507-louder-esp32-h5-pcb.pdf

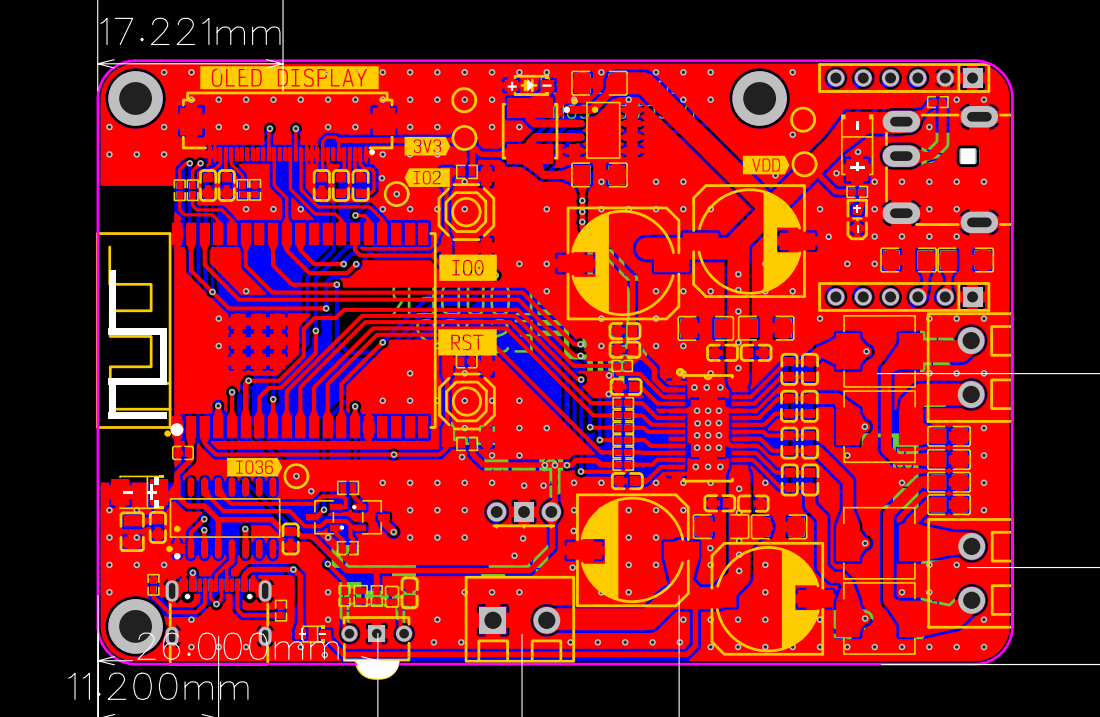
[picture p120: page 1]
