sonocotta/esp32-audio-dock/hardware/3-louder-esp32/rev-h5/2507-louder-esp32-h5-schematic.pdf

## U1GND ³⁹

## MCU

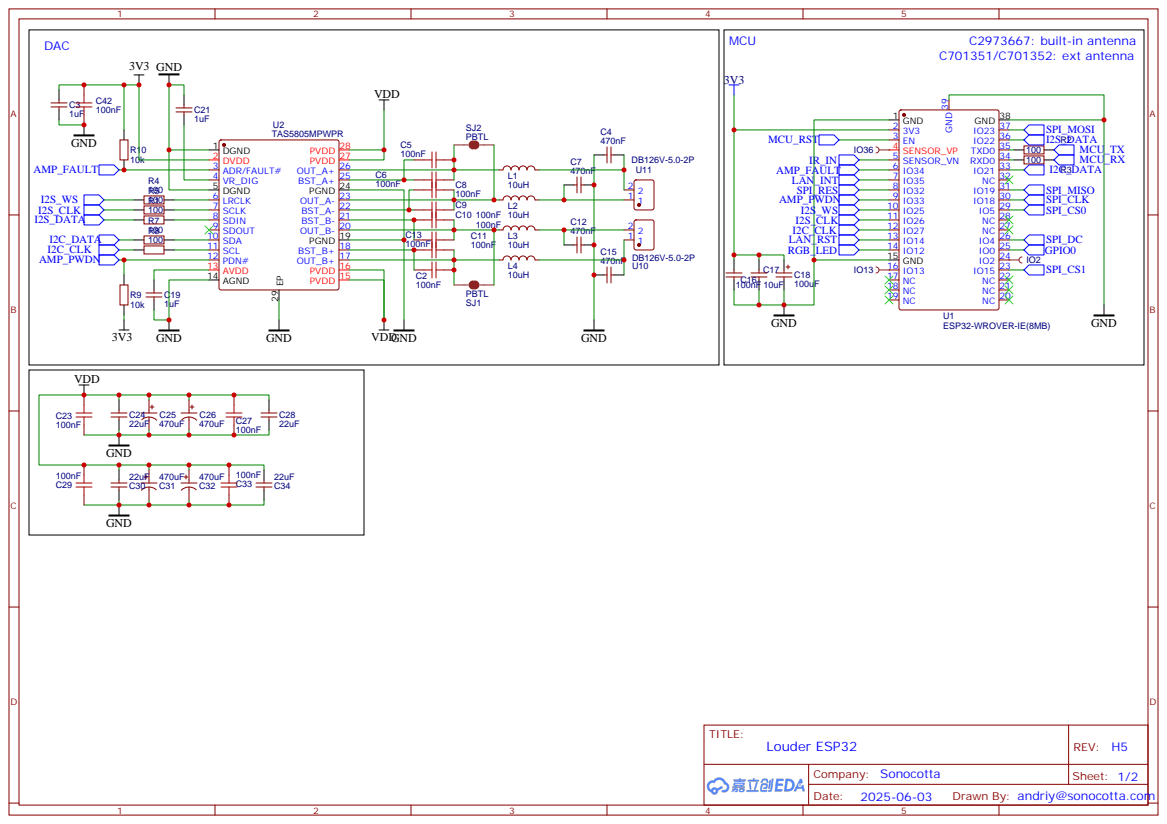
[picture p121: page 1]

Drawn By: andriy@sonocotta.com

## USB-TO-SERIAL BRIDGE USR-ES1 LAN module (W5500)

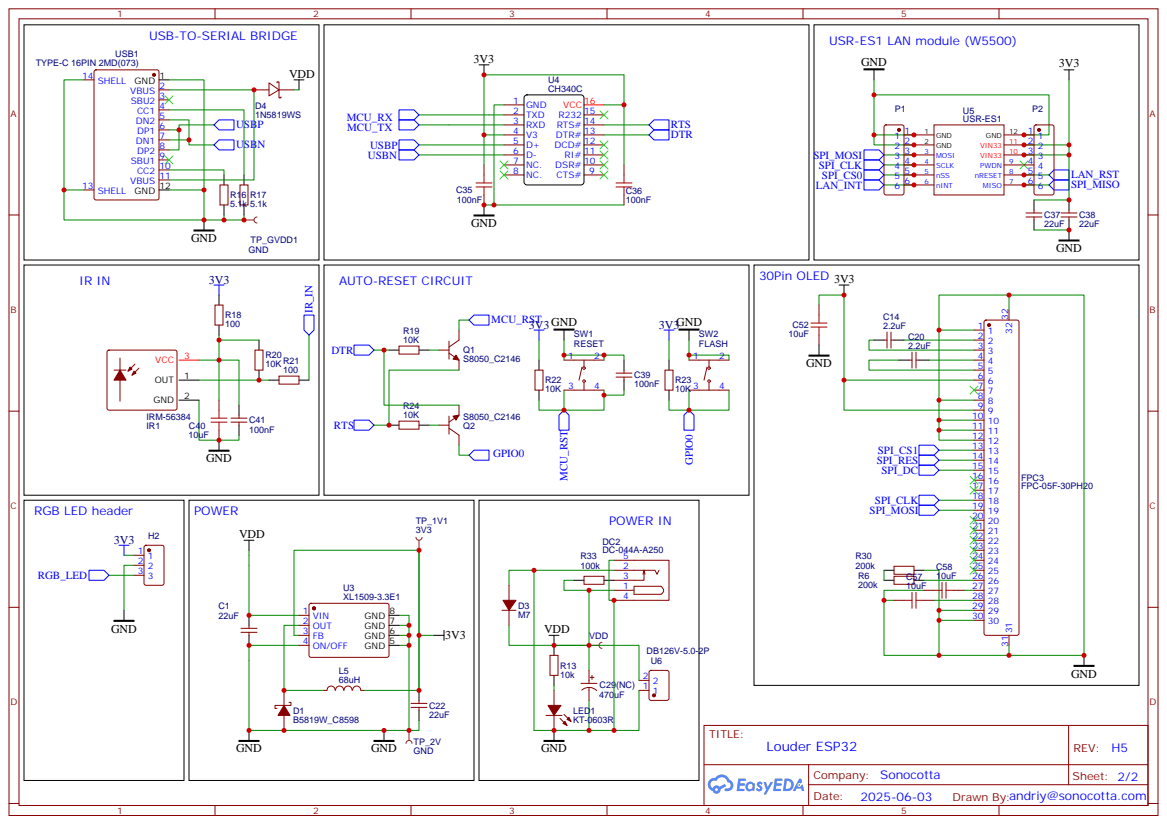
[picture p122: page 2]

Drawn By:andriy@sonocotta.com
